jorenheit/bfcpu/doc/compiling.tex

\chapter{Introduction to Acus}

\section{What This is Not}
Acus\footnote{Latin for \emph{needle}, referring to the pointer in the BF computation model.} is not a BF compiler: it is a C++ library for the development of such compilers. This chapter is \emph{not} a guide on how to use Acus. For examples and extensive API-details, please visit the Github repository at \cite{acus}. Instead, this chapter goes through the most important concepts, methods and abstractions that allow for the translation of high-level programming concepts (like function-calls and flow-control) into BF.

\begin{figure}[H]
  \centering
  
\end{figure}

\section{Motivation and History}
Up to this point, almost every BF program used to test the computer was found online and used verbatim. On some occasions, simple BF routines were written to test very specific functions of the computer, but these were borderline trivial to produce. The next goal therefore was to create a compiler that takes human-readable source code and turns that in to BF which in turn can be assembled into the binary format understood by Synapse-191.

The author has attempted to create such a language and compiler in the past: \emph{BrainFix} \cite{brainfix} is a compiler that takes a C-style language and turns it into BF. This compiler works reasonably well but has some serious limitations:
\begin{itemize}\itemsep0em 
\item No (true) function-calls: all functions are inlined. Recursion is therefore \emph{not} possible.
\item Dynamic array accesses were implemented in a way that limits the maximum array size to 256 elements.
\item Only 8-bit numbers are supported (assuming the BF tape stores 8-bit integers in its cells).
\item No signed integers.
\item No pointers or function pointers.
\end{itemize}
%
These limitations derive from naive choices during early development of the compiler, where the focus was on parsing and language design: features were bolted on rather than planned for in early stages of development. In this second, more mature, attempt to build a compiler, we started out by building a backend rather than a full compiler: \emph{Acus}. Acus is a C++ library that exposes a set of elementary assembly-like instructions (like arithmetic operations, conditional expressions and jumps) that are compiled into BF. Acus is meant to be used a compiler back-end: a layer that accepts higher-level operations and emits BF code. A front-end can then link with Acus, parse an actual programming language, call the necessary Acus functions and produce the corresponding BF. Acus can also be used on its own, since its library-functions were designed to feel a bit like an actual language, as can be seem from the \emph{Hello World} snippet of Listing \ref{lst:acushello}\footnote{Note that using Acus in this way is unintended and inconvenient: the resulting binary is a program that, when run, prints a string of BF commands to the output. That string of commands then has to be written to a file, which can then be executed by a BF computer or interpreter. When the program is modified, the C++ source has to be recompiled and the resulting executable re-run to produce the updated BF source.}

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

    int main() {
      Assembler a;

      a.program("hello", "main").begin(); {

        a.function("main").begin(); {
          a.print(literal::string("Hello, World!\n"));
          a.returnFromFunction();
        } a.endFunction();

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

\section{Challenges and Design Goals}
The main goal was to make Acus capable enough that a frontend for a language like C would have no problem implementing most of its features. These include:
%
\begin{enumerate} \itemsep0em 
\item 8-bit and 16-bit integer datatypes;
\item signed integers (both 8-bit and 16-bit);
\item arrays and strings;
\item user-defined structured types (structs);
\item arithmetic operators (\texttt{+, -, *, /, \%});
\item logic operators (\texttt{and, or, not, xor});
\item function-calls and recursion;
\item pointers and pointer arithmetic;
\item labels and conditional jumps (\texttt{goto});
\item global data.
\end{enumerate}
%
Familiar features that were \emph{not} implemented include:
\begin{enumerate} \itemsep0em 
\item floating/fixed point numbers;
\item bitwise operators;
\item member functions;
\item control-flow mechanisms like \texttt{for, while, switch, if}.
\end{enumerate}
%
Many of the above can be implemented in terms of the features provided by Acus; it was a deliberate choice not to make these part of the library in order for the library to remain as fundamental as possible.

\chapter{Acus Program Model}

\section{Basic Block Scheduling}
In the Acus model, a program consists of a series of basic blocks, sequences of code that are always executed in order, and jumps between those blocks. Each basic block ($B_i$) is compiled into its corresponding BF instructions and wrapped in a BF loop-pair (i.e.  between \texttt{[} and \texttt{]}) whose entry is controlled by generated guard code $G_i$. The complete sequence of blocks is enclosed in a main-loop, conditional on the value in a special BF-cell, the \emph{Run}-cell, which can be reset by any block when the program should be terminated. Prior to entering the main-loop a \emph{head} section $H$ is responsible for the initial setup of the data-tape and the tail-code $T$ is responsible for resetting the pointer to the \emph{Run}-cell before the closing bracket of the main-loop is encountered:

\begin{center}
  
\end{center}

The aforementioned guard-code $G_i$ compares the block-index $i$ to the value stored in another predefined cell: the \emph{TargetBlock}-cell. Only when this cell contains the exact index of the block \emph{and} the \emph{Run}-cell is still nonzero, is the loop entered and its code executed. Therefore, each block should at some point set the index of next block to be executed to keep the program going (not setting a different \emph{TargetBlock} will cause the same block to be executed ad infinitum). This approach basically implements a state-machine that can be expressed in pseudo-code as shown in Listing \ref{lst:acusprogram}. Note that, on each iteration of the main-loop, all blocks are scanned until the scheduled block is encountered. In a worst-case scenario, when block \texttt{i} is scheduled by block \texttt{i+1} (the currently exectuted block), the system will first need to check all blocks from \texttt{i+2} up to \texttt{N} before looping back to block 1 and eventually block \texttt{i}.

\begin{lstfloat}[H]
  \begin{lstlisting}[style=pseudocode]
    B = {B1, B2, ..., Bn}

    Run = 1
    TargetBlock = 1 # not necessarily block 1

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

\section{Frames and Initialization}
Each function has its own chunk of memory that it operates on, called a frame. Calling a function has the effect of advancing the data-pointer one cell beyond the end of the current current function's frame. When a BF program is executed, the pointer starts at cell 0 in frame 0, which is dedicated to hold the global data (Section \ref{sec:compiling:globalframe}). Frame 1 starts just beyond the end of frame 0; the exact offset depends on the number of global variables and their sizes. The initialization code that runs prior to entering the main loop, needs to set up both frame 0 and frame 1:
%
\begin{enumerate}
\item Set a marker (the \texttt{SeekMarker}, Section \ref{sec:compiling:seekmarker}) at the start of the data-tape (cell 0). This marker can be used as a stop-sign during dynamic pointer movements to locate the start of the global data frame (and to prevent the pointer from moving into the (undefined) negative address-space).
\item Set another marker (the \texttt{FrameMarker}) that marks the start of frame 0 (the global data frame, Section \ref{sec:compiling:globalframe}). This might seem redundant as we already marked the start of this frame with a \texttt{SeekMarker}, but since every frame has a \texttt{FrameMarker}, the global frame needs it as well for generalized algorithms to work.
\item Calculate the size of frame 0 and move the pointer to the start of frame 1 (the frame that will be used by the function that is set as the entrypoint for the program). 
\item Mark the start of frame 1 by setting the \texttt{FrameMarker} here as well.
\item Move the datapointer to the \emph{Run}-cell of frame 1 and set its value to 1.
\item While the datapointer points to the \emph{Run}-cell of frame 1, open the main-loop (guaranteed to be entered as we just set this cell to 1).
\end{enumerate}

\section{Block Guards}
The guards $G_i$ compare the value stored in the \texttt{TargetBlock} cell to their index and check if the \emph{Run} flag is still set. The results of these comparisons are and'ed together and used as the loop-condition for the block that follows immediately after. Because the block-index is known at compile-time, it can simply be subtracted from (a copy of) the \texttt{TargetBlock} value. If the result is 0, this means we should enter the block given that the \emph{Run}-cell contains a nonzero (true) value. The logic necessary to implement these checks is discussed in more detail in Section \ref{sec:compiling:logic}. A simplified BF algorithm that implements this logic could look like the snippet of Listing \ref{lst:guard}; the real algorithm is more complicated because it needs to support 16-bit block-indices (otherwise each program would be limited to only 255 code-blocks), which requires 16-bit arithmetic and logic routines (Section \ref{sec:compiling:arithmetic}).

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

\end{lstlisting}
\caption{Simplified guard code for block 3 ($G_3$). The contents of block 3 will be executed only if \texttt{f} is nonzero.}
\label{lst:bfadd}
\end{lstfloat}

\section{Example: Fibonacci}
To illustrate how a program is divided into basic blocks, a simple fibonacci number generator is shown in Figure \ref{fig:fibexample}. It consists of three functions, each of which contains multiple basic blocks. The block-ID's are shown in square brackets at the start of each block. Blocks end at control-boundaries, i.e.~ places in the code where potential jumps take place or explicitly at predefined labels.

The program starts execution in block 10, which is set as the entry-point by the initialization code (note that the initialization code of Listing \ref{lst:acusprogram} sets the entry-point to block 1; the specific example from below requires the initialization sequence to set this value to 10 instead). A function-call is immediately encountered, ending the current block. After initializing a new stack frame (this will be covered later, Section \ref{sec:noideayet}), the \emph{TargetBlock} is set to block 1: the entry-block index of the callee. This will cause control flow to skip over block 11 and loop back to block 1, which will then be entered. When control hits the conditional statement of block 3, either block 4 or 5 will be set as the next target-block, depending on the result of evaluating \texttt{i < n}. In this case, both the \texttt{if}- and \texttt{else} body contain only a single block that immediately terminates in a jump. When control eventually reaches the end of \texttt{main}, the \emph{Run}-cell is set to zero, causing flow to exit the main loop and terminate the program.

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

\chapter{Tape Abstractions}
\section{Overview}
The data-tape is considered a stack, where each function owns a stack frame. Each frame contains a return-slot (if the function returns a value), argument-slots (if the function takes arguments) and local data (variables and temporaries used in the function). A slot is a series of (logical) cells that contains a variable of some data-type, used by the function. The size of a slot depends on the number of cells required to represent the type of the variable. Instead of using single BF-cells to compose slots, logical cells or macro-cells are used. Each macro-cell contains 9 actual BF-cells, referred to as \emph{fields} from now on, each of which serves a different purpose. Central to the macro-cells are the two value-fields that hold the actual value of the logical cell. By having two value fields, we allow for 16-bit datatypes to be implemented within the same logical-cell, rather than having to allocate two macro-cells for a single 16-bit variable. The other fields hold temporary data or metadata required to perform higher level functions like arithmetic, flow control and dynamic pointer movement. When the compiler needs to generate code that moves the BF-pointer to location known only at runtime (for example when dereferencing pointers or accessing array elements by a dynamic index), these fields can hold temporary values or metadata necessary to perform the move. Other non-value fields include temporary scratch-pads (heavily used when performing arithmetic operations), payload-fields (used to transport data to locations known only at runtime) and a flag cell that is dedicated to the evaluation of loop-conditions. Having all these fields near one another on the BF-tape has the nice consequence of BF-algorithms being relatively short due to tight pointer-move-sequences.

\subsection*{Example: Fibonacci (continued)}
Figure \ref{fig:tapehierarchy} shows the tape hierarchy described above, applied to the fibonacci example from before and evaluated immediately after \texttt{fib} was first called. Even though this program made no use of any global data, this frame is still depicted for completeness' sake. Zooming in on Frame 2, used by the \texttt{fib}-function, we see how a frame starts with the slots we previously encountered in Section \ref{sec:compiling:program}: the \texttt{TargetBlock} and \texttt{Run} slots, which are used to determine where to jump next and whether to continue execution at all. Since \texttt{fib} does not return anything, no return-slot has been allocated to this frame. Instead, the local data immediately follows: first the arguments passed to the function (initialized by the caller), then the local data used within the function. Only the variables \texttt{c} and \texttt{i} have been explicitly allocated by the programmer, but temporary slots have been created by the compiler to store the result of \texttt{a + b} and \texttt{i < n}.

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

Sections \ref{sec:compiling:first} through \ref{sec:compiling:last} below will go into more detail about each of the layers of abstraction.

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

\section{Cells and Macro-Cells}
BF operates on the most fundamental level of raw cells. Each consecutive sequence of 9 such cells constitutes a logical macro-cell as mentioned before in Section \ref{sec:compiling:tape}. In this section, we will cover each of the 9 fields of a macro-cell in more detail and cover some of their use cases. 

\subsection{\texttt{Value0} and \texttt{Value1}}
The value fields together hold the semantic value of the macro-cell. The \texttt{Value0} field contains the low byte and the the \texttt{Value1} field holds the high byte of an integer of at most 16 bits. Acus implements four integer data-types using these two fields: unsigned 8-bit (\texttt{u8}), unsigned 16-bit (\texttt{u16}), signed 8-bit (\texttt{s8}) and signed 16-bit (\texttt{s16}). When referring to 8-bit values, the \texttt{Value1} field is simply ignored. Signed integers are represented using two's complement; some algorithms need to do some additional work (like evaluating the sign-bit) before applying the usual operations.

\subsection{\texttt{Scratch0} and \texttt{Scratch1}}
Many BF algorithms need temporary cells as scratch-pads. These cells can be temporarily claimed by an algorithm and must be left behind empty for the next algorithm to use. An example of a simple algorithm that makes use of these values is the non-destructive addition. Say we want to add the contents of cell \texttt{x} to those of cell \texttt{y} without destroying \texttt{x} in the process. We can achieve this by decrementing \texttt{x} while at the same time incrementing \texttt{y} until \texttt{x} becomes zero. However, in order to restore \texttt{x} to its original value, we need to use a scratch-pad to construct a copy of \texttt{x} which is moved back after the addition has been completed. This algorithm is shown in Listing \ref{lst:bfadd}, where instead of denoting pointer-movement with sequences of \texttt{<} and \texttt{>}, we simply write the name of the variable/slot to indicate a move to that (known) location on the tape.

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

  # Step 1: add x to both y and tmp, destroying x
  x[- y+ tmp+ x]

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

\subsection{\texttt{Flag}}
The \texttt{Flag} field is reserved to store a value that determines whether or not a BF-loop should be entered. An algorithm can store an intermediate, temporary, value in the flag-cell and use that as a branch or loop-condition. Whereas scratch-cells are general purpose temporary storage locations, the flag-cell is meant to be used for this purpose alone to avoid confusion. The section below includes an example that also utilizes this field in Listing \ref{lst:bfseekframe}.

\subsection{\texttt{FrameMarker}}
The \texttt{FrameMarker} field is only set when the macrocell marks the start of a new frame. When performing dynamic pointer movements, a marker like this (the \texttt{SeekMarker} is used in a similar way) can be used to move from a still unknown to a known location on the tape. Let's say we know the data-pointer is somewhere in Frame 2, but we don't know where because we just performed some (dynamic) movement (i.e. an algorithm that moves the pointer by an amount that depends on runtime data). We know that the start of the frame is to the left of the current position, so we can perform the algorithm below and be sure that we're pointing at the start of the frame when the algorithm is finished. This algorithm is shown in the pseudo-BF of Listing \ref{lst:bfseekframe}. This works because every macro-cell has the same width and because exactly one FrameMarker is set at the start of the active frame.

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

    # Assumed: there already exist implementations for assignment and
    #          the logical NOT operator.
    
    ASSIGN(Flag, NOT(FrameMarker))
    Flag [-                            # Reset flag before moving away from it
      FrameMarker  <<<<<<<<<           # Move to the frame-marker field of
                                       #   neighboring macro-cell
      ASSIGN(Flag, NOT(FrameMarker))   # Compute exit-condition
      Flag                             # Check exit-condition
    ]

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

\subsection{\texttt{SeekMarker}}
The purpose of the \texttt{SeekMarker} field is very similar to that of the \texttt{FrameMarker} field, in the sense that it is used to mark certain cells to make dynamic movement possible. For example, a known location can be marked before performing a dynamic move, in order to be able to move back to that known location using an algorithm similar to that of Listing \ref{lst:bfseekframe}. Also, when a dynamic move has been completed, its location can be marked to make future excursions to this location more efficient. Contrary to the \texttt{FrameMarker}, which is specifically used to mark the start of a frame, the \texttt{SeekMarker} field may be set for any macro-cell on the tape.

\subsection{\texttt{Payload0} and \texttt{Payload1}}
The payload fields are used to store values that need to be transported along to dynamically determined locations. Algorithms that move the pointer to such locations can be trivially extended to move data along using these fields: one for the low byte and one for the high byte of the value. Additionally (but this is not the intended use-case), a payload cell may be used as a scratch-pad (when an algorithm has exhausted the available scratch cells), provided it is not being used to transport any values at that time.

\section{Slots}
A slot is a storage location for one object. Single 8 or 16-bit integers occupy a single macro-cell, while larger objects like arrays or structs occupy a sequence of macro-cells. A slot is bound to a stack frame; its offset is defined as the index of its first macro-cell with respect to the start of the frame, not the start of the actual BF data-tape.

In addition to a name and offset, a slot holds information about its scope (to determine access, allow for name-shadowing and keep track of lifetime) and its \emph{kind}. Most slots are of the \emph{local} kind, representing data local to the current function, but slots can also be tagged \emph{global}, \emph{available} (representing a free block of memory that was previously occupied), \emph{temp} (for temporary slots that should be freed after use) and \emph{cache} (Section \ref{sec:compiling:cache}). Figure \ref{fig:slots} shows a section of a frame and how local slots could be organized given their data-types and sizes. Note that the size of a slot is expressed in terms of the number of macro-cells rather than raw BF cells.

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

\subsection{Data Types}
Slots reserve space on the tape, but the compiler also needs to know how that space should be interpreted. This is the role of data types. A data type determines how many macro-cells are needed to store a value, which sub-slots exist inside that value, and which algorithms may be used to copy, compare, increment or otherwise manipulate it.

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

\texttt{s8} &
1 &
Signed 8-bit integer, stored using the same physical layout as \texttt{u8}. \\

\texttt{u16} &
1 &
Unsigned 16-bit integer stored across both value fields of a macro-cell. \\

\texttt{s16} &
1 &
Signed 16-bit integer, stored using the same physical layout as \texttt{u16}. \\

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

\texttt{ptr<T>} &
2 &
Pointer to a value of type \texttt{T}. The type parameter determines how dereferenced storage is interpreted. The first cell contains the \texttt{FrameDepth} of the pointer, i.e. how many frames back the pointee is actually stored. The second cell stores the offset of the pointee within its frame. Refer to section \ref{sec:compiling:pointers} for more details on pointers. \\

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

\subsection{Slot Proxies and Materialization}
Most expressions encountered by the compiler can be resolved directly into a slot. For example, assume \texttt{x} is an array of structs that contain an \texttt{age} field, e.g. 

\begin{lstlisting}
  struct Person {
    id:  u16
    age: u8
  };

  let x: array<Person, 5>;
\end{lstlisting}

In this context, the expressions \texttt{x}, \texttt{x[2]} and \texttt{x[2].age} all refer to known slots or sub-slots (assuming square brackets represent array indexing and a dot represents field access for struct objects). The compiler knows in which slot the array \texttt{x} is stored, it knows how to find the offset of element 2 and it knows how to find the offset of the \texttt{age} field.

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

For the purposes of this chapter, slot proxies should therefore be understood as compiler-level access paths. They bridge the gap between the static memory layout known at compile-time and the dynamic addresses that sometimes have to be computed at runtime. This idea becomes especially important in the caching system (Section \ref{sec:compiling:cache}), which is designed to limit unnecessary materialization and synchronization events.

\subsection{Local Memory Management}
Declaring a local variable means reserving a slot inside the current function frame. The slot is assigned a type, a size and an offset relative to the start of the frame. From that point onward, the variable name refers to this slot until it goes out of scope. Since the offset is fixed, accessing a local variable does not require a runtime search through the tape.

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

\section{Frames and Calls}
A frame groups all data belonging to one function activation. Each frame contains the local control cells, optional return storage, arguments, named locals and compiler-generated temporaries (and cached values). Function calls can then be viewed as transitions between frames: the caller prepares the callee frame, moves the data-pointer to the start of the frame and sets the \texttt{TargetBlock} value to the callee's entry block. When a function returns, the data-pointer is moved back to the caller's frame and execution continues at the first block beyond the call. Each of these steps will be described in more detail in the sections below.

\subsection{Reference Frames}
Each stack frame acts as a frame of reference, or coordinate system, to the data-pointer. Since function calls happen dynamically, stack frames are allocated dynamically as well. This means that the compiler has no way of knowing where the data-pointer is located in an absolute sense (i.e. with respect to the start of the BF-tape). Instead, it keeps track of the pointer-location with respect to the start of the current frame. Pushing a new frame on top of the stack and moving the pointer to the start of this frame can then be seen as performing a coordinate transformation - or rebase - of the pointer: the origin is now in the frame of the callee rather than the caller. 

\subsection{Global Data Frame}
Global data is allocated in its own frame at the very start of the data-tape, i.e. frame 0. This frame is not owned by any function and is accessible from any other frame to fetch data from or write to. Like dynamic array accesses or pointer dereferences, a global slot is accessed through a slot-proxy and will be materialized locally before any work can be done on it. This introduces synchronization issues accross call-boundaries, which will be addressed in Section \ref{sec:compiling:cache}. In the sections below, the concept of (stack) frames refers to a frames actually tied to the functions being executed, not the global frame.

\subsection{Frame Layout}
The exact layout of a frame depends on the nature of the function that it belongs to, depending on the return-type and number of arguments it takes. However, each instance of a function-call will cause an identical frame-layout to be generated as a result. In general, a frame is laid out as follows (in terms of macro-cells):
\begin{enumerate}
\item \texttt{TargetBlock}: a macro-cell who's \texttt{Value} fields are set to the index of the next block scheduled for execution and who's \texttt{FrameMarker} is set to 1, indicating the start of a new frame.
\item \texttt{Run}: a macro-cell dedicated to store a local copy of the program's \emph{run}-state. As soon as this flag is set to 0 (from any frame), none of the blocks will execute and the main loop will be aborted.
\item \texttt{ReturnSlot}: Depending on the return-type of the function, a slot is allocated to hold the return-value. Note that this slot is located at a fixed offset, so it can be reached easily even from within the caller's frame in order to fetch the return-value. If the function returns \texttt{void}, this slot does not exist at all.
\item \texttt{Locals}: Data local to the frame, which can be categorized further:
  \begin{enumerate}
  \item local variables (including function-arguments), organised in slots as discussed before in Section \ref{sec:compiling:slots}.
  \item compiler-generated temporaries
  \item cached materializations
  \end{enumerate}
\end{enumerate}

\subsection{Calls, Returns and Meta-Blocks}
\paragraph{Calls} To call a function, the caller has to perform the following actions:
\begin{enumerate}
\item Set the caller's \texttt{TargetBlock} to the ID of a compiler-generated meta-block. This is the continuation that will run after the callee returns (see Section \ref{sec:compiling:metablocks} below).
\item Copy or materialize the function arguments into the argument slots of the next frame. The offsets are known relative to the caller's frame, so this does not require a runtime search.
\item Initialize the control cells of the callee frame: its \texttt{Run} cell is set and its \texttt{TargetBlock} is set to the callee's entry block.
\item Move the data pointer to the start of the callee frame and treat this position as the new origin.
\end{enumerate}
After these steps, the runtime naturally dispactches to the block who's ID is now stored in the \texttt{TargetBlock} cell of the freshly initialized stack frame.

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

Propagatin the \emph{run}-flag like this makes early termination compositional: if a callee stops the program, the caller observes the same stopped state after the return metablock has run. This allows a (builtin) function like \texttt{abort()} to be implemented.

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

\chapter{Code Generation}
Before discussing larger compiler structures such as caching and dynamic access, it is useful to look at the small Brainfuck idioms from which Acus builds its generated code. Many of the algorithms in this section are simple in isolation, but together they form the vocabulary used to express higher-level operations on the tape. Moving or copying values, constructing constants or adding numbers together are all small patterns that appear repeatedly in the generated output.

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

\section{Clearing, Moving and Copying Values}
One of the simplest useful BF idiom is destructive movement: consume one cell while adding its value somewhere else. From that, one can build addition and non-destructive copying by introducing temporary storage. Basically all other algorithms rely on repeated applications of these idioms.

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

\section{Constant Factories}
Constructing known values is fundamental to creating meaningful programs. Even a simple \emph{Hello World} requires the compiler to construct those characters somewhere in memory. The simplest and most naive way of setting a BF cell to some known value, e.g. \texttt{n}, is to concatenate \texttt{n} plus-commands. For example, the expression \texttt{x = 20} can be compiled to:
\begin{lstlisting}[style=brainfuck]
  # SET(x, 20)
  x [-] ++++++++++ ++++++++++ # 23 characters + initial move sequence
\end{lstlisting}
Notice that the cell containing \texttt{x} is first cleared using \texttt{[-]}, since we generally cannot assume that it already contains zero (even if it was freshly allocated). This particular example adds 23 characters to the generated BF output (excluding the initial move); larger values obviously produce more characters. The number of characters needed to set a cell to some constant value $c$ is simply:
\begin{align}
  N_1(x\leftarrow c) = 3 + c + m(x)
\end{align}
where $m(x)$ is the number of move-commands necessary to reach the slot of \texttt{x} from the current pointer position.

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

\vspace{0.5cm}\noindent\begin{minipage}{\linewidth}
\begin{lstlisting}[style=brainfuck]
  # SET(x, 20)
  # Assumes s is an empty scratch cell
  
  x [-]         
  s ++++ [      
    x +++++     
    s -        
  ]
\end{lstlisting}
\end{minipage}
%
Instead of 23 characters, this algorithm adds only 15 non-movement characters to the program. In general, when $c$ can be factored into $a$ and $b$, the number of BF characters necessary to construct this value is:
\begin{align}
  N_2(x\leftarrow ab, s) = 6 + a + b + m(x) + 3m(x, s)
\end{align}
where $m(x,s)$ is the number of move-commands necessary to move between the scratch-cell \texttt{s} and the target cell \texttt{x}. This value depends on the exact layout of a macro-cell but can be as low as 2 when the scratch-fields are right next to the value-fields. In the case where $m(x,s)=2$, the difference between both methods for this specific example is
\begin{align}
  N_1 - N_2 &= 3 + 20 + m(x) - (6 + 4 + 5 + m(x) + 3\cdot 2) \\
            &= 23 - 21 = 2.
\end{align}
In this small example the saving is only two characters, while the runtime cost increases because the generated loop must be executed. Luckily the benefit from the second method increases along with the value of $c$. Acus has a precomputed table of factors for all numbers up to 128 (listed in Appendix \ref{sec:appendix:factorytable}). Larger values can be reached by decrementing using the minus command to come down from 255 rather than up from 0 (BF cells wrap around after being decremented beyond 0). Each factorization $a\times b$ is chosen in such a way that it minimizes the sum $a+b$ (and consequently the number of output characters). In some cases (e.g. when $c$ itself is prime), it is better to factor a number close to $c$ and correct for the difference after doing the multiplication. For example, the optimal way to construct the value 31 is to first construct 30, then add 1, i.e. $31 = 5\times6 + 1$ for a total cost of 24 characters (as opposed to 34) for a gain of 10 characters per construction. Figure \ref{fig:constants} shows the number of characters generated for every constant up to 128 (the graph would be symmetric around this number when going from 129 to 255), for both methods. Acus implements both the naive and factorizing method and picks whichever produces the least amount of code.

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

\section{Addition and Subtraction}
\subsection{Addition (8-bit)}
The algorithm for addition is much like that of copying, the difference being that the target cell is never cleared in advance. When the right-hand-side (rhs) of an expression of the form \texttt{x += y} may be destroyed, the algorithm is very short and efficient:

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

\subsection{Addition (16-bit)}
Adding 16-bit numbers together is much more involved and no BF pseudocode will be listed for this reason. Instead the higher-level pseudocode of Listing \ref{lst:16bitadd} illustrates the process. First, the low bytes are added together as usual. If the resulting value is less than its original value, this means that the cell has overflowed and we need to carry a 1 to the high byte. This requires multiple scratch-cells to hold temporary copies and helpers. Moreover, we need to be able to do a less-than comparison and branch on the result to carry if necessary. The implementation of this operator is discussed below in Section \ref{compiling:less}.

\vspace{0.5cm}\noindent\begin{minipage}{\linewidth}
\begin{lstlisting}[style=pseudocode]
  # 16-bit version of x += y
  xLowBefore = low(x)
  low(x) += low(y)          # normal 8-bit add
  if low(x) < xLowBefore:
    high(x) += 1            # carry on overflow
  high(x) += high(y)        # normal 8-bit add
\end{lstlisting}
\end{minipage}

\subsection{Subtraction}
The subtraction algorithms are symmetric to the ones for addition, where increments are substituted for decrement operations and instead of checking for overflow, we check for underflow in the 16-bit case (i.e. wether the result has grown after doing the 8-bit subtraction on the low byte).

\subsection{Signed Integers}
For signed integers, no special algorithms have to be used at all. Since signedness is encoded using two's complement representation, addition and subtraction already work out of the box. Signedness becomes more important for comparisons, where the same bit pattern may represent a different ordering depending on how it is interpreted (as signed or unsigned).

\section{Multiplication and Division}
\subsection{Multiplication (8-bit)} Multiplication can be implemented in terms of repeated addition, much like we already did in the constant factory optimization. To evaluate the expression \texttt{x *= y}, we do the following:
\begin{enumerate}
\item Make a copy of the operand \texttt{x}.
\item Clear \texttt{x}
\item Repeatedly decrease \texttt{y} while adding the original value of \texttt{x}, stored in the copy, to \texttt{x} itself.
\end{enumerate}
The steps above are the generalized version of the algorithm, which can be optimized further for edge cases where \texttt{y = 0}, \texttt{y = 1} or even for powers of 2.

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

\subsection{Multiplication (16-bit)} A naive 16-bit algorithm can simply follow the exact same procedure by relying on 16-bit addition. However this leads to a lot of additions for large factors, which can slow down the runtime significantly. Instead, we can perform a small series of 8-bit multiplications and additions to get the same result, realizing that the 16-bit number is stored as a 2-digit base-256 number. That is, every 16-bit integer $x$ can be written as
%
\begin{align}
  x = x_0 + 256\cdot x_1,
\end{align}
%
where $x_0$ and $x_1$ are the low and high bytes of $x$ respectively. Multiplication then becomes:
%
\begin{align}
  z = x \times y &= (x_0 + 256x_1)(y_0 + 256y_1) \\
                 &= x_0y_0 + 256\cdot(x_1y_0 + x_0y_1) + 256^2\cdot(x_1y_1)
\end{align}
%
The final term only contributes to bits beyond the lowest 16 bits, so it can be discarded when the result is stored as a 16-bit value. This means that the low and high byte of the product $z$ can be expressed as
%
\begin{align}
z_0 &= x_0 y_0 \bmod 256 \\
z_1 &= \left(x_0 y_1 + x_1 y_0 + \left\lfloor \frac{x_0 y_0}{256} \right\rfloor \right) \bmod 256 
\end{align}
%
Therefore, the 16-bit product can be computed using three 8-bit multiplications. The low byte of the result comes from the low byte of $x_0y_0$, while the high byte receives the carry from this product together with the low bytes of the two cross-products.

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

  low(z)  = low(p0)
  high(z) = low(p1 + p2) 
\end{lstlisting}
\end{minipage}

\subsection{Division (8-bit and 16-bit)}
Unsigned division is implemented using repeated subtraction. Given two values \texttt{x} and \texttt{y}, the goal is to compute a quotient \texttt{q} and remainder \texttt{r} such that
%
\begin{align}
x = qy + r, \qquad 0 \leq r < y.
\end{align}
%
The simplest way to do this is to repeatedly subtract \texttt{y} from a running remainder until doing so would make it negative. The number of successful subtractions is the quotient, while the value left behind is the remainder.

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

  while r >= y:
  r -= y
  q += 1
\end{lstlisting}
\end{minipage}

The actual BF implementation cannot test \texttt{r >= y} directly. Instead, this comparison is implemented using scratch cells: temporary copies of \texttt{r} and \texttt{y} are decremented together until one of them reaches zero. If the copy of \texttt{y} reaches zero first, the subtraction is safe and the loop may continue. If the copy of \texttt{r} reaches zero first, the next subtraction would underflow and the algorithm terminates. The original values must either be preserved during this test or reconstructed afterwards, which makes division considerably more expensive than addition or multiplication.

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

Division by zero is not meaningful in this model and has to be handled separately by the compiler or by the generated program. In the current arithmetic model, unsigned division should therefore be understood as an operation that assumes a nonzero divisor.

\subsection{Signed Multiplication and Division}
Signed multiplication and division are implemented as thin layers around the corresponding unsigned algorithms. First, the sign bit of the left-hand side is inspected. If it is set, the value is negated in-place and a temporary flag is set to indicate that the final result should be negative. The right-hand side is copied into temporary storage before its sign is inspected, so the original divisor or multiplier does not have to be modified. If this copy is negative, it is negated as well and the result-sign flag is toggled. At this point, both operands have been converted to positive values, while the temporary flag records whether the original operands had opposite signs.

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

\section{Boolean Operations}
All of the usual logic and comparison operators have been implemented in Acus, which allow the programmer to build complex logical expressions. Some of these logical building blocks will be explained below.

\subsection{Conversion to Bool}
The simplest boolean conversion is one where an integer is transformed into either a 0 or 1, depending on its truth-value (any non-zero is considered \emph{true}). To accomplish this, the value of the operand \texttt{x} is moved into a scratch cell, leaving \texttt{x} empty. We then branch off the value of \texttt{s}: if non-zero, \texttt{x} is set back to 1. If the conditional block is not entered, \texttt{x} remains 0.

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

\paragraph{Logical Not} The not-operator does the exact opposite of a boolean conversion. It transforms its operand into 1 when it's value equals 0 and vice versa for any non-zero values. The algorithm is almost identical to that of \texttt{BOOL(x)}: instead of setting \texttt{x} to 0 and incrementing it in the loop-block, we set it to 1 and decrement it inside the loop.

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

\subsection{Logical And}
The \texttt{AND} operator is implemented using a nested BF-loop block. The operands are used to decide if those blocks should be entered. The result is then set in the inner loop, which can only be reached if both operands evaluate to \emph{true}.

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

\subsection{Logical Or}
If we compare the logical \texttt{AND} algorithm to two switches wired in series, where current can only flow if both switches are turned on, the \texttt{OR} algorithm is its parallel counterpart. Each of the operands guards a loop and if either one of them is entered, the result is set to \emph{true}.

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

\subsection{Equality}
In testing for equality, we rely on the fact that $x-y=0$ when $x=y$ to implement a routine that calculates \texttt{NOT(x - y)}.

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

\subsection{Less Than}
This operator was already used before in the implementation of 16-bit addition, to determine the value of the carry-bit. It is implemented by reducing both of its operators simultaneously, until either one of them reaches zero. If the rhs is still non-zero when this happens, the lhs must have been the smaller of the two. This turns out to be a pretty tedious algorithm when expressed in BF so instead it is presented in pseudo-code below. Other comparison operators are implemented similarly.

\vspace{0.5cm}\noindent\begin{minipage}{\linewidth}
\begin{lstlisting}[style=pseudocode]
  # LT(x, y)

  while x AND y:
    --x
    --y

  x = NOT(y)
\end{lstlisting}
\end{minipage}

\subsection{Signed Comparisons}
Comparisons on signed integers cannot use the unsigned implementations discussed before. Instead, the exact form of the algorithm depends on the sign-bits of both of the argument. A runtime check has to be done to determine which one of four branches must be taken. For example, for the less-than operator, if its operands are both signed:

\begin{enumerate}
\item If both are positive, use the unsigned algorithm.
\item If the lhs is negative and the rhs is positive (or zero), return 1 immediately.
\item If the lhs is positive (or zero) and the rhs is negative, return 0 immediately.
\item If both are negative, use the unsigned greater-than algorithm on their absolute values.
\end{enumerate}

This requires an algorithm to evaluate the sign of an integer and one to take its absolute value. To get the sign-bit of an 8-bit value $x$ (1 if negative, 0 otherwise), we simply compute the result of $x >= 128$ (using the unsigned greater-equal operator). Values with bitpatterns identical to unsigned values from 128 on are interpreted as negative numbers (i.e. have their highest bit set) in two's complement representation.

To calculate the absolute value of a signed integer, its sign-bit is first calculated. If not set, the value can remain unmodified since it's already positive. If the sign-bit \emph{is} set, it can be negated simply by subtracting it from 0.

\vspace{0.5cm}\noindent\begin{minipage}{\linewidth}
\begin{lstlisting}[style=brainfuck]
  # ABS(x)
  # Assumes s to be an empty scratch-cell

  SUB_FROM(s, x)
  MOVE(s, x)
\end{lstlisting}
\end{minipage}

\section{Pointer Movement}
BF has no random access instruction; the only way to reach a cell is to move the data-pointer (simply referred to as the \emph{pointer} from now on) step by step. This makes pointer movement one of the central code-generation problems in Acus. 

\subsection{Static Pointer Movement}
In most scenario's, when the source and destination locations are known at compile time, pointer movement is straightforward: emit the required number of \texttt{<} or \texttt{>} commands. This is the common case for local slot operations within a frame, where the compiler can keep track of the current pointer position relative to the frame origin.

\subsection{Dynamic Pointer Movement}
The most interesting pointer-movement algorithms are the ones where the target is not known until runtime. Examples include array access by a runtime index and pointer dereferencing. These algorithms rely on metadata stored in macro-cells: markers, counters and payload fields are used so that the BF pointer can search through structured tape data and stop at the correct logical cell. We can distinguis between two different classes of dynamic pointer movement: \emph{marker-based} and \emph{offset-based} moves. In marker-based moves, the pointer moves along the tape until it hits some pre-set marker. In offset-based moves, the offset is stored in the payload cells and dragged along with the pointer while being reduced; when the payload becomes zero, the destination has been reached. 

\subsubsection{Marker-Based}
This method relies on a marker-field, the \texttt{FrameMarker} or \texttt{SeekMarker}, being set beforehand. We can then move the pointer into the corresponding field of the current cell and move in some direction until the marker is hit.

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

\subsubsection{Offset-Based}
The second class of dynamic pointer movement relies on a runtime value representing the offset being stored on the tape itself. For example, in the expression \texttt{x[i]}, \texttt{i} is a variable stored on the tape that contains the offset with respect to the start of the array \texttt{x} in terms of the size of the element-type of \texttt{x}. To reach a specific offset, the pointer is moved to the start of the array (known at compile-time) and the offset-value is copied or moved into its payload-fields (a single one for 8-bit values and both of them for 16-bit values). The pointer is then moved to the right while the payload is moved along and decremented. When the payload hits zero, the required offset has been reached.

\vspace{0.5cm}\noindent\begin{minipage}{\linewidth}
\begin{lstlisting}[style=brainfuck]
  # TO_OFFSET(b, i)
  # b = base address
  # i = index/offset wrt base

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

\subsection{Payload Transport}
Dynamic writes are harder than dynamic reads because data has to be carried to a location that is not statically known. Acus solves this by moving values through designated payload fields. The payload travels along with the dynamic traversal and is deposited when the target macro-cell is found.

For marker-based movements, the payload can simply be moved along with the pointer because the payload fields are not used to perform the move itself. For offset-based movements, the payload-fields already serve the purpose of containing the offset itself and cannot be used to transport the new value. Instead the usual offset-based method described in Section \ref{sec:compiling:dynamicmove:offset} is used to find the element, where a marker is planted. Then, the marker-based method is used to move the payload to that position and overwrite its value-field(s).

\chapter{Caching} \label{sec:compiling:cache}
Slot proxies (Section \ref{sec:compiling:slotproxies}) allow expressions to remain abstract until their value is needed. However, repeatedly materializing the same proxy can duplicate work. For example, accessing the same array element several times in a block should not require materializing the element locally each time. Instead, multiple accesses can be cached and a writeback occurs only when necessary, for example at control-flow boundaries.

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

To implement this caching system, dependencies between proxies need to be carefully maintained. During compilation, a dependency graph is built and used to determine which cache-entries have become dirty and which ones need to be flushed back into their actual storage location. This section will go over the different techniques and compromises that were made in their implementation.

\section{Cache Graphs}
A cache entry connects a logical proxy to a concrete slot that currently holds its materialized value. Entries can be marked dirty when modified or invalidated/removed when there is no guarantee that its value still represents the actual referred-to data.

Figure \ref{fig:cachegraph} shows a simplified representation of a cache graph, where each entry (node) contains information about the proxy that it represents, the physical location of the cached slot, and its parent- and child-nodes. An proxy \texttt{A} is considered a parent of proxy \texttt{B} if the canonical storage location of \texttt{B} is a subset of that of \texttt{A}. For example, given the expression \texttt{x[i][j]}, the expression \texttt{x[i]} is represented by a proxy that itself will be cached (assuming \texttt{i} is not known at compile-time). Therefore, to materialize the element \texttt{x[i][j]} we first need to materialize \texttt{x[i]} and their cache-entries are in a parent-child relation: \texttt{x[i]} is the parent of \texttt{x[i][j]} because the storage slot of \texttt{x[i]} encloses that of \texttt{x[i][j]}.

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

\section{Flushing and Invalidation}

\subsection{Dirty Entries} In the example of Figure \ref{fig:cachegraph}, all entries are \emph{clean} (i.e. not \emph{dirty}), since none of the expressions involving them modified their contents. The expression \texttt{x[i][j] = 3} would have the effect of writing the value 3 to the cache slot and marking its corresponding entry as dirty. Dirty entries must at some point be flushed into their parent to make sure that all changes applied to a cached object eventually propagate into canonical storage. 

\subsection{Flushing} Flushing an entry means writing its contents back into its parent (either another cached slot or canonical storage). An entry needs to be flushed in the following scenarios:
%
\begin{enumerate}
\item The entry is marked \emph{dirty} and a parent somewhere up in the cache hierarchy is materialized. If the dirty entry is multiple parents removed, this causes all intermediate parents to be flushed as well. For example, if \texttt{x[i][j]} is dirty and \texttt{x} is materialized, the dirty \texttt{x[i][j]} is flushed into \texttt{x[i]}, which then becomes dirty and is subsequently flushed into \texttt{x} itself. The entire path from \texttt{x[i][j]} to \texttt{x} is now clean.
\item Whenever a control-flow boundary is crossed. For example, at jumps or function-calls, the entire cache is cleared by flushing all entries (starting at the deepest child-nodes) back into their canonical storage. This makes sure that all flow-paths see the correct data.
\item Whenever a pointer is dereferenced. Because pointers can refer to anything (of some type) at runtime, the entire cache is cleared to make sure that the pointee is up-to-date when fetched by the dereferencing algorithm.
\item Before cache-invalidation. In scenario's where a cache entry is invalidated (removed from the tree), it is flushed back before doing so. Cache invalidation is discussed in more detail below.
\end{enumerate}

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

\subsection{Invalidation} Entries can be invalidated when an external dependency or (indirect) parent is modified. In the example of Figure \ref{fig:cachegraph} the entries \texttt{x[i]} and \texttt{x[i][j]} have been materialized in cache using the value stored in slot \texttt{i} at that time. When the value of \texttt{i} is modified, the proxy refers to a new object and the entry has become invalid. When this is about to happen, the invalidated proxy has to be flushed (if dirty) \emph{before} modifying the dependency, after which it (and its descendants) can be removed from the cache tree.

\subsection{Writes}
Writing to a proxy will, as mentioned before, cause its cached entry to be marked \emph{dirty}. When the object is overwritten independently from its original value, there is no need to materialize that value at all. For example, when compiling the expression \texttt{x[i][j] = 3}, the value stored initially in \texttt{x[i][j]} is completely irrelevant. In such cases, a new entry for the proxy \texttt{x[i][j]} is created and marked dirty immediately and no materialization algorithm has to be executed.

\subsection{Example} The listing below shows a more complete version of code that leads to the cache hierarchy of Figure \ref{fig:cachegraph}. At the lines marked \texttt{(a)} and \texttt{(b)}, the graph from Figure \ref{fig:cachegraph} is generated. Then, at line \texttt{(c)}, a new value is assigned to \texttt{x[i][j]}. This assignment expression will write the value \texttt{3} directly to the already cached slot for the proxy \texttt{x[i][j]} and mark this entry as \emph{dirty}. At the next expression (line \texttt{(d)}), a new proxy (\texttt{x[i][k]}) is materialized, which shares a parent (\texttt{x[i]}) with the now dirty entry \texttt{x[i][j]}. Therefore, before materializing \texttt{x[i][k]}, the dirty entry is flushed upwards into \texttt{x[i]}, after which its dirty-state is cleared and \texttt{x[i][k]} can be materialized. Finally, at line \texttt{(e)}, the value of \texttt{i} is modified. All cache-entries that depend on \texttt{i} (the left branch of the graph) therefore need to be invalidated. In this example these entries have just been flushed and are still clean, so there is no need to flush them prior to deletion.

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
