jorenheit/bfcpu/website/content/tex/compilation.tex

\chapter{Introduction to Acus}
\label{sec:compilation:introduction}

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

\begin{figure}[H]
  \centering
  
\end{figure}

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

    int main() {
      Assembler a;

      a.program("hello", "main").begin(); {

        a.function("main").begin(); {
          a.print(literal::string("Hello, World!\n"));
          a.returnFromFunction();
        } a.endFunction();

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

\chapter{Acus Program Model}
\label{sec:compilation:programmodel}

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

\begin{center}
  
\end{center}

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

\begin{lstfloat}[H]
  \begin{lstlisting}[style=pseudocode]
    B = {B1, B2, ..., Bn}

    Run = 1
    TargetBlock = 1 # not necessarily block 1

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

\section{Frames and Initialization}
\label{sec:compilation:framesinit}
Each function has its own chunk of memory that it operates on, called a frame. Calling a function has the effect of advancing the data-pointer one cell beyond the end of the current current function's frame. When a BF program is executed, the pointer starts at cell 0 in frame 0, which is dedicated to hold the global data (Section \ref{sec:compilation:globalframe}). Frame 1 starts just beyond the end of frame 0; the exact offset depends on the number of global variables and their sizes. The initialization code that runs prior to entering the main loop, needs to set up both frame 0 and frame 1:
%
\begin{enumerate}
\item Set a marker (the \texttt{SeekMarker}, Section \ref{sec:compilation:seekmarker}) at the start of the data-tape (cell 0). This marker can be used as a stop-sign during dynamic pointer movements to locate the start of the global data frame (and to prevent the pointer from moving into the (undefined) negative address-space).
\item Set another marker (the \texttt{FrameMarker}) that marks the start of frame 0 (the global data frame, Section \ref{sec:compilation:globalframe}). This might seem redundant as we already marked the start of this frame with a \texttt{SeekMarker}, but since every frame has a \texttt{FrameMarker}, the global frame needs it as well for generalized algorithms to work.
\item Calculate the size of frame 0 and move the pointer to the start of frame 1 (the frame that will be used by the function that is set as the entrypoint for the program). 
\item Mark the start of frame 1 by setting the \texttt{FrameMarker} here as well.
\item Move the datapointer to the \emph{Run}-cell of frame 1 and set its value to 1.
\item While the datapointer points to the \emph{Run}-cell of frame 1, open the main-loop (guaranteed to be entered as we just set this cell to 1).
\end{enumerate}

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

The program starts execution in block 10, which is set as the entry-point by the initialization code (note that the initialization code of Listing \ref{lst:acusprogram} sets the entry-point to block 1; the specific example from below requires the initialization sequence to set this value to 10 instead). A function-call is immediately encountered, ending the current block. After initializing a new stack frame (this will be covered later, Section \ref{sec:compilation:frames}), the \emph{TargetBlock} is set to block 1: the entry-block index of the callee. This will cause control flow to skip over block 11 and loop back to block 1, which will then be entered. When control hits the conditional statement of block 3, either block 4 or 5 will be set as the next target-block, depending on the result of evaluating \texttt{i < n}. In this case, both the \texttt{if}- and \texttt{else} body contain only a single block that immediately terminates in a jump. When control eventually reaches the end of \texttt{main}, the \emph{Run}-cell is set to zero, causing flow to exit the main loop and terminate the program.

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

The sections below go into more detail about each of the layers of abstraction.

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

\section{Cells and Macro-Cells}
\label{sec:compilation:macrocells}
BF operates on the most fundamental level of raw cells. Each consecutive sequence of 9 such cells constitutes a logical macro-cell as mentioned before in Section \ref{sec:compilation:tape}. In this section, we will cover each of the 9 fields of a macro-cell in more detail and cover some of their use cases. 

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

  # Step 1: add x to both y and tmp, destroying x
  x[- y+ tmp+ x]

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

In addition to a name and offset, a slot holds information about its scope (to determine access, allow for name-shadowing and keep track of lifetime) and its \emph{kind}. Most slots are of the \emph{local} kind, representing data local to the current function, but slots can also be tagged \emph{global}, \emph{available} (representing a free block of memory that was previously occupied), \emph{temp} (for temporary slots that should be freed after use) and \emph{cache} (Section \ref{sec:compilation:cache}). Figure \ref{fig:slots} shows a section of a frame and how local slots could be organized given their data-types and sizes. Note that the size of a slot is expressed in terms of the number of macro-cells rather than raw BF cells.

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

\texttt{s8} &
1 &
Signed 8-bit integer, stored using the same physical layout as \texttt{u8}. \\

\texttt{u16} &
1 &
Unsigned 16-bit integer stored across both value fields of a macro-cell. \\

\texttt{s16} &
1 &
Signed 16-bit integer, stored using the same physical layout as \texttt{u16}. \\

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

\begin{lstlisting}
  struct Person {
    id:  u16
    age: u8
  };

  let x: array<Person, 5>;
\end{lstlisting}

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

For the purposes of this chapter, slot proxies should therefore be understood as compiler-level access paths. They bridge the gap between the static memory layout known at compile-time and the dynamic addresses that sometimes have to be computed at runtime. This idea becomes especially important in the caching system (Section \ref{sec:compilation:cache}), which is designed to limit unnecessary materialization and synchronization events.

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

When a slot is freed, either because a local variable leaves scope or because a temporary can be dismissed, its region is marked as available. The contents of the underlying macro-cells are not necessarily cleared immediately; freeing a slot only means that the compiler is allowed to reuse that region for later storage. When a new slot is allocated, a sufficiently large available region may be split into an occupied part and a smaller remaining available part. Conversely, when a slot is freed, neighbouring available regions are merged back together. This prevents the local frame from becoming unnecessarily fragmented and allows larger slots to be allocated later when enough adjacent macro-cells have become free. This management system is discussed in more detail in Section \ref{sec:compilation:memorymanagement}.

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

\subsection{Global Data Frame}
\label{sec:compilation:globalframe}
Global data is allocated in its own frame at the very start of the data-tape, i.e. frame 0. This frame is not owned by any function and is accessible from any other frame to fetch data from or write to. Like dynamic array accesses or pointer dereferences, a global slot is accessed through a slot-proxy and will be materialized locally before any work can be done on it. This introduces synchronization issues accross call-boundaries, which will be addressed in Section \ref{sec:compilation:cache}. In the sections below, the concept of (stack) frames refers to a frames actually tied to the functions being executed, not the global frame.

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

\subsection{Calls, Returns and Meta-Blocks}
\label{sec:compilation:metablocks}
\paragraph{Calls} To call a function, the caller has to perform the following actions:
\begin{enumerate}
\item Set the caller's \texttt{TargetBlock} to the ID of a compiler-generated meta-block. This is the continuation that will run after the callee returns (see Section \ref{sec:compilation:metablocks} below).
\item Copy or materialize the function arguments into the argument slots of the next frame. The offsets are known relative to the caller's frame, so this does not require a runtime search.
\item Initialize the control cells of the callee frame: its \texttt{Run} cell is set and its \texttt{TargetBlock} is set to the callee's entry block.
\item Move the data pointer to the start of the callee frame and treat this position as the new origin.
\end{enumerate}
After these steps, the runtime naturally dispactches to the block who's ID is now stored in the \texttt{TargetBlock} cell of the freshly initialized stack frame.

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

\chapter{Memory Management}\label{sec:compilation:memorymanagement}
\section{Overview}
Whenever a variable is declared to Acus, the allocator will look for available space in the current stack-frame. From the allocator's point of view, named locals, compiler temporaries and cache slots are all typed slots inside the current frame. They differ only in who requests them and when they are released.

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

\begin{enumerate}\itemsep0em
\item Freed slots are marked \texttt{Available} and can be re-used.
\item Declarations can be scoped to reduce the lifetime of variables. Variable slots will become \texttt{Available} when the variable goes out of scope.
\item Temporary slots declared by the compiler are freed immediately after use.
\item Adjacent \texttt{Available} slots are merged to accommodate larger data types.
\item \texttt{Available} slots will split into smaller parts when a variable with a size smaller than that of the slot is allocated to it.
\end{enumerate}

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

\subsection{Heap Allocation}
While technically possible, Acus does not support heap-allocation. This would require a separate heap-frame and a runtime system that keeps track of the memory layout in that frame (including de-allocation, block splitting and block merging). The runtime overhead that would arise from managing the heap at runtime would be so costly that it was decided to not implement this as a feature. However, a front-end might emulate heap-allocation using the global frame. One could certainly write algorithms on top of Acus to reserve a specific amount of raw data in the global frame and manage it using existing features.

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

\section{Clearing, Moving and Copying Values}
\label{sec:compilation:movecopy}
One of the simplest useful BF idiom is destructive movement: consume one cell while adding its value somewhere else. From that, one can build addition and non-destructive copying by introducing temporary storage. Basically all other algorithms rely on repeated applications of these idioms.

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

  low(z)  = low(p0)
  high(z) = low(p1 + p2) 
\end{lstlisting}
\end{minipage}

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

  while r >= y:
  r -= y
  q += 1
\end{lstlisting}
\end{minipage}

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

\vspace{0.5cm}\noindent\begin{minipage}{\linewidth}
\begin{lstlisting}[style=pseudocode]
  # LT(x, y)

  while x AND y:
    --x
    --y

  x = NOT(y)
\end{lstlisting}
\end{minipage}

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

  SUB_FROM(s, x)
  MOVE(s, x)
\end{lstlisting}
\end{minipage}

\section{Pointer Movement}
\label{sec:compilation:pointers}
BF has no random access instruction; the only way to reach a cell is to move the data-pointer (simply referred to as the \emph{pointer} from now on) step by step. This makes pointer movement one of the central code-generation problems in Acus. 

\subsection{Static Pointer Movement}
\label{sec:compilation:staticmove}
In most scenario's, when the source and destination locations are known at compile time, pointer movement is straightforward: emit the required number of \texttt{<} or \texttt{>} commands. This is the common case for local slot operations within a frame, where the compiler can keep track of the current pointer position relative to the frame origin.

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

\section{Flushing and Invalidation}
\label{sec:compilation:flushinvalidate}

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

\section{Move Semantics}
The algorithms for moving and copying BF cells are very similar: copying means we simultaneously move to the target-cell and a scratch cell, only for the scratch-cell to be emptied back into the source location. Obviously, we should move and avoid the full copy algrithm whenever possible. Therefore, if we can prove that the source is expendible, we can just move its contents out of it to a new location. Acus tries to find as many opportunities as possible to move instead of copy. For example in the following situations:
\begin{enumerate}\itemsep0em
\item Assignment from a temporary expression. e.g. \texttt{x = y + z}, where \texttt{y + z} is a temporary which does not outlive the statement anyway. 
\item Flushing cache-entries that are about to be deleted. When a cache-tree is flushed prior to it being deleted, we can move instead of copy towards the root.
\end{enumerate}

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

\section{Primitive and BF Merging}
\subsection{Merging Primitives}
Before generating actual BF characters, Acus will produce a series of primitives, each of which represents a relatively simple sequence of BF instructions on a slightly higher level (Table \ref{tab:primitives}). Sequences of primitives can sometimes be merged into shorter sequences or even no-ops. For example, if the primitive \texttt{MoveRelative(3)} is immediately followed by the primitive \texttt{MoveRelative(6)}, they can be merged into a single \texttt{MoveRelative(9)}. This leads to a series of merge-rules, listed in Table \ref{tab:mergerules}. By applying these rules iteratively to the generated sequence of primitives, the program can be shrunk significantly in post-processing.

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

  \texttt{MovePointerRelative(x)} & Move the pointer by \texttt{x} cells (positive means to the right). \\
  \texttt{ChangeValue(c)} & Change the current value by an amount \texttt{c}. \\
  \texttt{ZeroCell} & Set the current value to \texttt{0} using \texttt{[-]}. \\
  \texttt{ZeroCellPlus} & Set the current value to \texttt{0} using \texttt{[+]}. \\
  \texttt{ConstructConstant(c)} & Construct the value \texttt{c} in the current cell. \\
  \texttt{MoveData(x)} & Move the contents of the current cell to relative position \texttt{x}. \\
  \texttt{CopyData(x)} & Copy the contents of the current cell to relative position \texttt{x}. \\
  \texttt{Add(x)} & Add the value of the cell at relative position \texttt{x} to the value of the current cell. \\
  \texttt{Subtract(x)} & Subtract the value of the cell at relative position \texttt{x} from the value of the current cell. \\
  \texttt{Boolean} & Set the current cell to its boolean value. \\
  \texttt{Not} & Set the current cell to its logical not value. \\
  \texttt{Or(x)} & Set the current value to the logical OR of this value and the value inside the cell at relative offset \texttt{x}. \\
  \texttt{And(x)} & Set the current value to the logical AND of this value and the value inside the cell at relative offset \texttt{x}. \\
  \texttt{Xor(x)} & Set the current value to the logical XOR of this value and the value inside the cell at relative offset \texttt{x}. \\
  \texttt{Equal(x)} & Set the current value to 1 if it's equal to the value in the cell at relative offset \texttt{x}, 0 otherwise. \\
  \texttt{Less(x)} & Set the current value to 1 if it's less than the value in the cell at relative offset \texttt{x}, 0 otherwise. \\
  \texttt{LessOrEqual(x)} & Set the current value to 1 if it's less than or equal to the value in the cell at relative offset \texttt{x}, 0 otherwise. \\
  \texttt{Greater(x)} & Set the current value to 1 if it's greater than the value in the cell at relative offset \texttt{x}, 0 otherwise. \\
  \texttt{GreaterOrEqual(x)} & Set the current value to 1 if it's greater than or equal to the value in the cell at relative offset \texttt{x}, 0 otherwise. \\
  \texttt{Cmp(c)} & Set the current value to 1 if it's equal to the compile-time constant \texttt{c}, 0 otherwise. \\
  \hline
  \caption{Acus primitives.}
  \label{tab:primitives}   
\end{longtable}

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

\texttt{ZeroCell} & \texttt{ZeroCell} & \texttt{ZeroCell} \\
\texttt{ZeroCell} & \texttt{ZeroCellPlus} & \texttt{ZeroCell} \\
\hline

\texttt{ZeroCellPlus} & \texttt{ZeroCellPlus} & \texttt{ZeroCellPlus} \\
\texttt{ZeroCellPlus} & \texttt{ZeroCell} & \texttt{ZeroCellPlus} \\
\hline

\texttt{MovePointerRelative(x)} & \texttt{MovePointerRelative(y)} & \texttt{MovePointerRelative(x + y)} \\
\hline

\texttt{ConstructConstant(c)} & \texttt{ChangeBy(d)} & \texttt{ConstructConstant(c + d)} \\
\texttt{ConstructConstant(c)} & \texttt{ConstructConstant(d)} & \texttt{ConstructConstant(d)} \\
\texttt{ConstructConstant(c)} & \texttt{ZeroCell} & \texttt{ZeroCell} \\
\texttt{ConstructConstant(c)} & \texttt{ZeroCellPlus} & \texttt{ZeroCellPlus} \\
\texttt{ConstructConstant(c)} & \texttt{Boolean} & \texttt{ConstructConstant(c != 0)} \\
\texttt{ConstructConstant(c)} & \texttt{Not} & \texttt{ConstructConstant(c == 0)} \\
\texttt{ConstructConstant(c)} & \texttt{Cmp(d)} & \texttt{ConstructConstant(c == d)} \\
\hline

\texttt{ChangeBy(c)} & \texttt{ChangeBy(d)} & \texttt{ChangeBy(c + d)} \\
\texttt{ChangeBy(c)} & \texttt{ZeroCell} & \texttt{ZeroCell} \\
\texttt{ChangeBy(c)} & \texttt{ZeroCellPlus} & \texttt{ZeroCellPlus} \\
\texttt{ChangeBy(c)} & \texttt{ConstructConstant(d)} & \texttt{ConstructConstant(d)} \\
\hline

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

\texttt{Boolean} & \texttt{Boolean} & \texttt{Boolean} \\
\texttt{Boolean} & \texttt{Not} & \texttt{Not} \\
\hline

\texttt{Not} & \texttt{Boolean} & \texttt{Not} \\
\texttt{Not} & \texttt{Not} & \texttt{Boolean} \\
\hline

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

\hline
\caption{Primitive merge rules.}
\label{tab:mergerules} 

\end{longtable}

\subsection{Merging BF}
As a final pass, after all primitives have been lowered into actual BF character, Acus will scan the resulting source code for cancellation opportunities: sequences of consecutive \texttt{+} and \texttt{-} or \texttt{<} and \texttt{>} commands that can be collapsed. The primitive-merging rules already do this to some extend by merging \texttt{ChangeValue} and \texttt{MovePointerRelative} primitives, but that does not capture all opportunities. For example, when a \texttt{MovePointerRelative} primitive is followed by another that, when lowered to BF, starts with a sequence of \texttt{>} commands, these can be merged or cancelled in the final result.
