jorenheit/bfcpu/doc/img/images.odp

Memory

Program

Data

CPU

Registers

R1

⋮

Rn

ALU

Control Unit

IO

Output Devices

Input Devices

## Slide 2

CPU

Registers

R1

⋮

Rn

ALU

Control Unit

IO

Output Devices

Input Devices

Program Memory

Data
Memory

## Slide 3

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
Control Unit

Control Unit

⋮

⋮

Instruction
Flags
Cycle

Control signals

A,V

S

FB

4

Flags

Cycle

CC

3

Z

Instruction

ROM

DP

16

Data Bus

RAM

Address Bus

Keyboard

Screen

SP

8

## Slide 4

Address:

Data Array:

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
Data Pointer

## Slide 5

Address:

Data (RAM)

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
Data Pointer
(DP = 4)

## Slide 6

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
Microcode ROM’s

State

Instruction

Cycle

ROM 2

ROM 1

ROM 0

Address

16-23

8-15

0-7

⋮

## Slide 7

PLACEHOLDER

## Slide 8

555 Output

Flip-Flop Output

Decoder Clock

Module Clock

## Slide 9

Button

Monostable 1

Monostable 2
