jorenheit/bfcpu/doc/architecture.tex

\chapter{Synapse-191 Architecture} \label{sec:architecture}
\section{Hardware Overview} \label{sec:architecture:overview}
A true BISC implementation is a direct representation of the abstract BF machine described in Section \ref{sec:brainfck}, consisting of an array of memory-cells together with a pointer pointing to one of these cells. The pointer can move along the array while modifying its contents one step at a time. Figure \ref{fig:simplerepresentation} illustrates an example intermediate state of such a system. Consider the BF program ``\texttt{>>>>>+.}'', applied to the initial conditions shown in the example. The pointer would take 5 steps to the right, landing on cell 9 which contains the number 41. It will then increment and output this value, displaying 42 on the screen (assuming a screen of some sort is used as the output device and it is displaying numbers directly rather than interpreting them as ASCII).

\begin{figure}[H]
  \centering
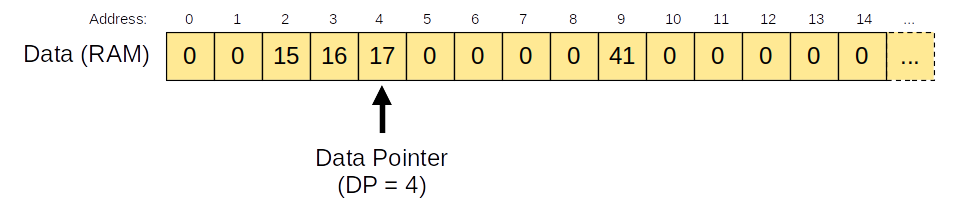
[picture p33: doc/img/simple_representation.png]
  
  \caption{Example state of a BF machine.}
  \label{fig:simplerepresentation}
\end{figure}

In a physical system, the data-tape would be a large memory space in RAM and the data pointer is a register that holds a value representing an address within that space. The pointer is moved by simply changing the value stored in the data pointer register. Modifying values in regular systems happens inside the ALU (Arithmetic and Logic Unit), which is capable of addition, subtraction, multiplication and many more mathematical and logical operations. No full-blown ALU is needed in a BISC implementation because of the simplicity of the modifying operations: values only need to be incremented or decremented (this goes for both the data pointer and the data itself), which can be done directly at the register level when up/down binary counters like the 74LS193 integrated circuit are used. The program (a sequence of BF instructions) is stored in Read-Only Memory (ROM), whereas the data is stored in Random Access Memory (RAM). Instructions (4-bit) are fed from ROM into a control unit (CU) together with a set of flags (see \ref{sec:architecture:flags}) that encode the state of the machine. Depending on the state and current instruction, the CU sets the appropriate control signals for each of the modules (memory, registers and I/O) in order for the system to perform the appropriate actions. Table \ref{tab:modules} lists the components of this BISC implementation, whereas Figure \ref{fig:architecture} shows the (conceptual) connections between those modules. In the sections below, each of these connections will be clarified further. The actual implementation on the logic/hardware level is described in Chapter \ref{sec:implementation}.

\begin{table}[H]
  \centering
  \begin{tabulary}{\linewidth}{|C|C|C|}
    \hline
    \textbf{Full Name} & \textbf{Short Name} & \textbf{Description} \\
    \hline
    Data Memory & RAM & Represents the data tape in the BF model; this is where the data is stored. \\\hline
    Program Memory & ROM & Separate from RAM, which is where the program's instructions are stored. \\\hline
    Data Pointer Register & DP & 16-Bit counting register that represents the pointer in the BF model; points to data in RAM. \\\hline
    Data Register & D & 8-Bit counting register that represents the value currently pointed to by the DP. \\\hline
    Instruction Pointer Register & IP & 16-Bit Counting register that contains the address of the current instruction; points to data in ROM.\\\hline
    Stack Pointer Register & SP & 8-Bit counting register that holds a value pointing inside the stack-space in RAM; used to implement loops.\\\hline
    Loop Skip Register & LS & 8-Bit counting register, used to skip over loops.\\\hline
    Flag Registers A \& B & FA/FB & 4-Bit registers used to buffer flag values that encode the state of the system. \\\hline
    Instruction Register & I & 4-Bit register that buffers the currently active instruction. \\\hline
    Control Unit & CU & System that translates the current instruction into sequences of control signals. \\\hline
    Register Driver & RD & Subsystem of the CU that centralizes increment and decrement operations. \\ \hline
  \end{tabulary}
  \caption{Overview of the modules that make up the physical BISC implementation.}
  \label{tab:modules}
\end{table}

\begin{figure}[H]
  \centering
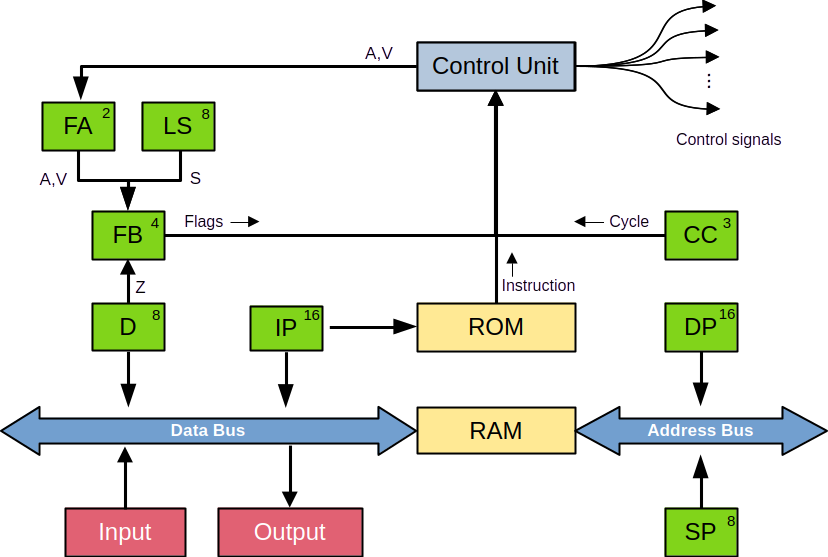
[picture p34: doc/img/bfcpu_architecture.png]
  
  \caption{Connections between modules in the BF processor.}
  \label{fig:architecture}
\end{figure}

\section{Flags} \label{sec:architecture:flags}
The state of the system is encoded using five flags: K, V, A, S, and Z. These flags were introduced to simplify control logic and enable performance optimizations during execution. Each flag serves a specific purpose, as explained below:

\paragraph{K-Flag} The K-flag is used for communication between the system and the IO Module, which run asynchronously. The flag is set by the IO Module and reset by the system to let each other know when certain data transactions have been completed.

\paragraph{A-Flag} The A-flag is set when the value in the DP register was modified, i.e.~when the data pointer has been shifted to a new cell. This is an architectural optimization to minimize the number of reads from and writes to RAM. Consider a long sequence of \texttt{+} or \texttt{-} instructions, which are very common in BF programs. A naive implementation of, for example, the \texttt{+} instruction, would consist of 3 steps: read the current value from RAM into D, increment the value in D, write the result back to RAM. However, when it is known that the data pointer has not been changed, we can keep operating on the copy in D. Only when the address has been changed (A was set), should we load the new value into D before modifying it.

\paragraph{V-Flag} The V-flag allows for another optimization, similar to that of the A-flag. Whenever the value in the D register has been modified, the V-flag is set. When the DP is about to change its value, through the \texttt{<} and \texttt{>} commands, the V-flag is checked. If set, we store the modified value back into RAM before moving the pointer. If not, the value hasn't changed and does not need to be synchronized into RAM. The number of cycles to complete long sequences of pointer move-commands is decreased substantially using this approach.

\paragraph{S-Flag} The S-flag is used to skip over blocks of code, primarily when skipping over loop-blocks. It is set when a loop should not be entered, causing all following commands to be ignored until the matching closing bracket is reached. Similarly, it is used at boot to skip over entire programs until the selected program is reached (when multiple BF programs have been written to the same program ROM).

\paragraph{Z-Flag} The Z-flag is set by the D register whenever it contains the value zero. This allows control-flow to branch on the value of the current cell, allowing for the implementation of loops.

\paragraph{Performance Gains} The number of cycles saved from using the A and V flags depends on the program that is running; programs with long and frequent sequences of \texttt{+}, \texttt{-}, \texttt{<} or \texttt{>} commands will benefit more than those with fewer or shorter sequences. To investigate the actual impact, a test suite of BF programs was put together and run in an emulator (a modified version of the C example shown in Listing \ref{lst:bfint}). The BF source for each of these programs is shown in Appendix \ref{sec:appendix:testsuite}. The modified interpreter contains a table of the number of cycles necessary to execute each instruction, depending on the aforementioned flags. This allows for a quantitative comparison between the naive implementation (load, modify, store) and the cache-like approach using the A and V flags. The results are shown in Figure \ref{fig:avresults}; a 16 to 22\% decrease was observed when using the A and V flags.

\begin{figure}[H]
  \centering
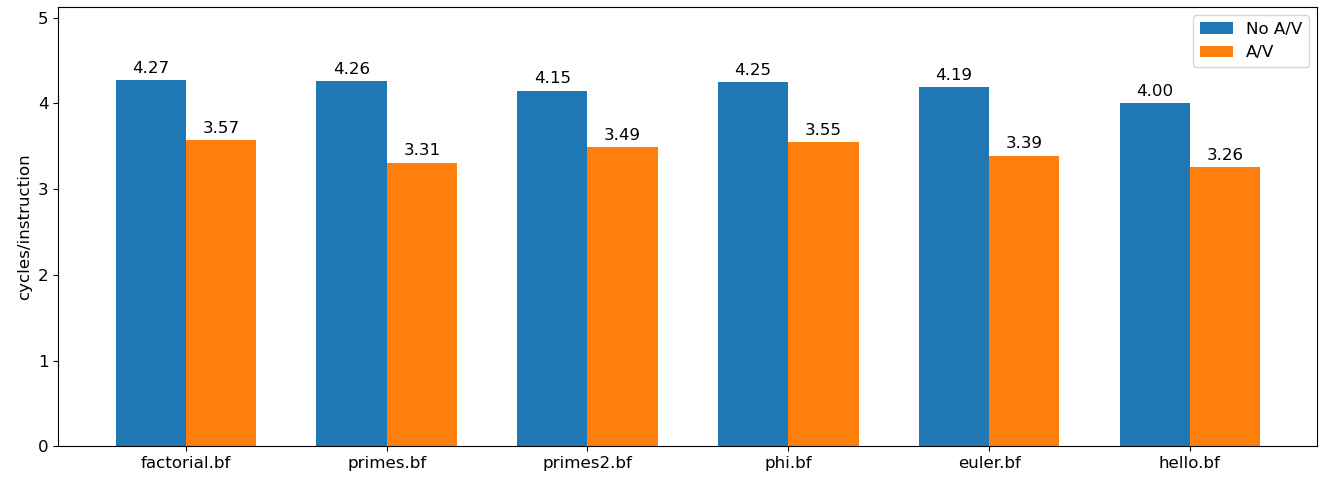
[picture p35: doc/img/avresults.png]
  
  \caption{The number of cycles per BF instruction drops by around 20\% when using the A and V flags.}
  \label{fig:avresults}
\end{figure}

\section{Data Pointer Register (DP)} \label{sec:architecture:dp}
The data-pointer corresponds to the pointer as specified in the BF-language. It points to some value in memory beyond the stack ($\ge$ 0x0100, see \ref{sec:architecture:sp}) and can be either incremented (moved right) or decremented (moved left) using the \texttt{>} and \texttt{<} instructions. Whenever the value pointed to by DP is modified by \texttt{+} or \texttt{-}, it is loaded into the D-register (see \ref{sec:architecture:d}), where it can be modified before being stored back into RAM.

\subsection*{Inputs}
The DP should be able to increment and decrement (corresponding to the \texttt{<} and \texttt{>} commands), and should be able to be enabled/disabled because of its connection to the address bus of the RAM (the Stack Pointer (SP; see \ref{sec:architecture:sp}) is also connected to this bus). While all other modules have the ability to be reset, the DP is the only register that can be reset (to 0x0100) at runtime. This is necessary during boot, when all the data cells need to be initialized to 0 (see \ref{sec:sequences:bootloading}).

\begin{enumerate}
\itemsep0em 
\item EN - Enable - Assert the stored 16-bit value onto the address bus.
\item U - Up - Increment the stored value.
\item D - Down - Decrement the stored value.
\item R - Reset - Reset the value to 0x0100, the start of the data section of RAM.
\end{enumerate}

\subsection*{Outputs}
\begin{enumerate}
\itemsep0em   
\item DP\_OUT - 16 bits, asserted onto the address bus when enabled (EN high).
\end{enumerate}

\section{Data Register (D)} \label{sec:architecture:d}
The data register holds a representation of the value currently pointed to by the DP and can be incremented and decremented (using the \texttt{+} and \texttt{-} commands). This register provides the Z-flag to signify that its current value is 0. Among other things, this flag can be used to determine whether or not to enter a loop.

\subsection*{Inputs}
\begin{enumerate}
\itemsep0em   
\item D\_IN - 8 bits - Data inputs, connected to the data bus.
\item EN - Enable - Assert the stored value onto the data bus.
\item LD - Load - Load data from the bus into D.
\item U - Up - Increment the stored value.
\item D - Down - Decrement the stored value.
\end{enumerate}

\subsection*{Outputs}
\begin{enumerate}
\itemsep0em 
\item D\_OUT - 8 bits - Data outputs, connected to the data bus.
\item SET\_Z - Set Zero Flag - High when the register stores a zero, connected to FB.
\end{enumerate}

\section{Instruction Pointer Register (IP)} \label{sec:architecture:ip}
The IP Register stores the instruction pointer (16-bits), which keeps track of the instruction that is currently being executed. It points to a certain address in ROM (which stores the program) and is usually incremented after each instruction has finished executing, in order to move to the next instruction. However, when the processor encounters the \texttt{[}-instruction (and a loop is entered), its value is stored in RAM at the location pointed to by the stack pointer (SP, see \ref{sec:architecture:sp}). When the matching \texttt{]}-instruction is encountered, this value can be loaded back into the IP in order to jump back to the start of the loop if needed.

\subsection*{Inputs}
\begin{enumerate}
\itemsep0em 
\item IP\_IN - 16 bits - Data inputs, connected to the data bus.
\item EN - Enable - Assert the stored value onto the data bus.
\item LD - Load - Load data from the bus into IP.
\item U - Up - Increment the stored value.
\end{enumerate}

\subsection*{Outputs}
\begin{enumerate}
\itemsep0em 
\item IP\_OUT - 16 bits - Data outputs, connected to the data bus and the address inputs of program-ROM;
\end{enumerate}

\section{Stack Pointer Register (SP)} \label{sec:architecture:sp}
The stack is the first part of RAM (addresses 0x0000 - 0x00FF) and is reserved to keep track of addresses in ROM that might need to be jumped to when flow encounters a loop-end instruction (\texttt{]}). The stack-pointer (SP) points to an address in this space; it is incremented whenever a new jump-address is pushed to the stack and decremented whenever an address is popped off the stack. In this implementation, the SP is an 8-bit value, which means that at most 256 different values can be stored onto the stack before the SP overflows (wraps around back to 0) and starts overwriting previous values. This would happen if a BF program was loaded that has more than 256 nested \texttt{[]}-pairs (and each of those loops is entered). Although possible, it is very unlikely to happen for the simple programs we intend to run. In Chapter \ref{sec:results}, where the required stack size is measured for a suite of test programs, this is confirmed; the largest value found for any required stack size in these programs was only 17, leaving plenty of space for even more complex programs.
  
\subsection*{Inputs}
\begin{enumerate}
\itemsep0em 
\item EN - Enable - Assert the stack-pointer onto the address-bus.
\item U - Up - Increment the stack-pointer.
\item D - Down - Decrement the stack-pointer.
\end{enumerate}

\subsection*{Outputs}
\begin{enumerate}
\itemsep0em 
\item SP\_OUT - 8 bits - connected to the address bus of RAM.
\end{enumerate}

\section{Loop Skip Register (LS)} \label{sec:architecture:ls}
The Loop Skip (LS) register is a counter that indicates whether or not we're in the process of skipping a loop. In BF, a loop (\texttt{[}) is only entered when the value currently pointed to is nonzero. In the case that it is zero, execution resumes beyond its matching loop-end instruction (\texttt{]}). When it is determined that a loop must be skipped (based on the Z-flag provided by the D-register), the LS register is incremented from 0 to 1 and the S-flag is set. This flag will remain set as long as the value in LS is nonzero, indicating that the system is in a skip-state. Subsequent instructions are then skipped until either another (nested) loop-start or a closing loop-end is encountered. On the former, the LS is incremented again while on the latter the LS is decremented. This has the effect that the LS becomes 0 again after the \texttt{]} that matches the original \texttt{[} which led to the skip. Normal execution occurs as soon as LS has become 0 again and the S-flag is reset back to 0.

\subsection*{Inputs}
\begin{enumerate}
  \itemsep0em
\item U - Up - Increment the stored value.
\item D - Down - Decrement the stored value.
\end{enumerate}

\subsection*{Outputs}
\begin{enumerate}
\itemsep0em 
\item SET\_S - Skip flag - set when its value is nonzero, connected to FB.
\end{enumerate}

\section{Flag Registers (FA and FB)} \label{sec:architecture:flag-registers}
\paragraph{FA} The first flag register (FA) holds two flag values, A and V, which are used to indicate that either the address (A) or value (V) has changed during one of the previous instructions. For instance, if D was incremented (or decremented), the V-flag is set to indicate a change of the \emph{value} being pointed to: the value in RAM is now outdated. When DP is incremented (or decremented), the A-flag is set to indicate a change of the current \emph{address}, meaning that the value in D is now outdated. For a more detailed description of the function and application of these flags, refer to Sections \ref{sec:sequences:+-} and \ref{sec:sequences:<>}.

\paragraph{FB} On the zeroth cycle of every instruction, these flags are latched into the FB register together with the Z and S-flags (set by the D and LS registers) for a total of 4 flags. This happens simultaneously with loading the next instruction into the instruction register (I, see \ref{sec:architecture:i}) and is not refreshed until loading the next instruction to make sure that the flag-state remains constant throughout the execution of the current instruction.

\paragraph{K-Flag} The previously mentioned K-flag is specific to interactions with the IO-module and is not buffered in either of the flag registers. It is discussed more thoroughly in Sections \ref{sec:sequences:output} and \ref{sec:sequences:input}.

\subsection*{Inputs}
\begin{enumerate}
\itemsep0em 
\item SET\_A - Assert the address-change-flag onto FA.
\item SET\_V - Assert the value-change-flag onto FA.
\item LD(FA) - Load A and V into FA (if set).
\item LD(FB) - Load A, V (previously buffered in FA), Z and S (from D and LS) into FB. 
\end{enumerate}

\subsection*{Outputs}
\begin{enumerate}
\itemsep0em 
\item F\_OUT - 4 bits - connected to the instruction decoder inside the Control Unit.
\end{enumerate}

\section{Instruction Register (I)} \label{sec:architecture:i}
The instruction register I buffers the current instruction pointed to by the IP. The instruction is loaded from program ROM into I at the start of every new instruction (cycle 0), right after IP has been incremented. Its outputs are used as part of the microcode address that goes into the decoder of the CU (see Figure \ref{fig:decoder} in Chapter \ref{sec:sequences}).

\subsection*{Inputs}
\begin{enumerate}
\itemsep0em 
\item LD(I) - Load the instruction pointed to by IP.
\end{enumerate}

\subsection*{Outputs}
\begin{enumerate}
\itemsep0em 
\item I\_OUT - 4 bits - connected to the instruction decoder inside the Control Unit.
\end{enumerate}

\section{Register Driver} \label{sec:architecture:registerdriver}
Rather than having a separate signal for each of the INC/DEC inputs of each register (e.g.~INC\_D, INC\_LS, etc.), a driver module was designed (see \ref{sec:implementation:registerdriver}) to drive registers that support modification of their contents (increment/decrement). In addition to a universal INC/DEC signal, three Register Select (RS) bits are used to index the target register. This approach has two advantages:
\begin{enumerate}
\item It decreases the number of control signals needed;
\item The logic needed to drive the counting registers (74LS193) only needs to be implemented once.
\end{enumerate}

The driver module accepts 5 control signals: 3 register-select signals (RS0 through RS2), INC and DEC. Using 3 register-select signals, up to 8 ($2^3$) registers can be selected, though only 5 need to be driven by the driver. Table \ref{tab:registers} contains an overview of each of the registers and the control signals they support. When all RS-signals are off, no register is selected.

\begin{table}[H]
  \centering
  \begin{tabular}{c|c|c|c|c|c|c}
    Register & \#Bits & EN  & LD  & INC  & DEC & RS2$|$RS1$|$RS0 \\ \hline 
    D        & 8      & x   & x   & x    & x   & 0$|$0$|$1 \\
    DP       & 16     & x   &     & x    & x   & 0$|$1$|$0 \\ 
    SP       & 8      & x   &     & x    & x   & 0$|$1$|$1 \\ 
    IP       & 16     & x   & x   & x    &     & 1$|$0$|$0 \\ 
    LS       & 8      &     &     & x    & x   & 1$|$0$|$1 \\ 
    FA       & 4      &     & x   &      &     & not addressable \\ 
    FB       & 4      &     & x   &      &     & not addressable  \\
    I        & 4      &     & x   &      &     & not addressable \\
  \end{tabular}
  \caption{Control signals available on each of the registers. The flag and instruction registers are not connected to the register driver.}
  \label{tab:registers}
\end{table}

\subsection*{Inputs}
\begin{enumerate}
  \itemsep0em
\item RS0 - Register Select Bit 0
\item RS1 - Register Select Bit 1
\item RS2 - Register Select Bit 2
\item INC - Increment selected register
\item DEC - Decrement selected register
\end{enumerate}

\subsection*{Outputs}
\begin{enumerate}
\itemsep0em 
\item U - 5 bits - Up signals - Connected to the U input of all registers that support the INC operation.
\item D - 5 bits - Down-signals - Connected to the D input of all registers that support the DEC operation.
\end{enumerate}

\section{Cycle Counter (CC)} \label{sec:architecture:cc}
Almost every BF instruction requires multiple cycles to complete. Therefore, in addition to the instruction and state, a cycle counter is used to determine the control signals that should be sent out at each step of the instruction. This cycle counter is implemented as a 3-bit counting register (allowing for at most 8 cycles per instruction) that increments on every clock cycle and sends its output to the control unit. Its only control signal is the clear signal (CLR) which resets the count to 0, in order to fetch the next instruction.

\subsection*{Inputs}
\begin{enumerate}
\itemsep0em
\item CLR - Cycle Reset - Reset the count to 0;
\end{enumerate}

\subsection*{Outputs}
\begin{enumerate}
\itemsep0em
\item CC\_OUT - 3 bits - Current value of the register (0--7).
\end{enumerate}

\section{Data Memory (RAM)}  \label{sec:architecture:ram}
RAM is divided into two parts: stack and data. The first 256 bytes (0x0000 - 0x00FF) make up the stack and are indexed by the stack pointer (\ref{sec:architecture:sp}). The data (corresponding to the BF tape) is stored at addresses 0x0100 through 0xFFFF and is indexed by the data pointer (\ref{sec:architecture:dp}). Its address lines are connected to the address bus, which in turn receives its value from either the DP or the SP. Its data lines are bidirectional and are connected to the data bus. When the Write Enable (WE) signal is active, data can be read from the bus and written into RAM. When instead the Output Enable (OE) signal is active, the current value in RAM (determined by the address on the address bus) is asserted onto the data bus.

\subsection*{Inputs}
\begin{enumerate}
\itemsep0em 
\item DATA\_IN - 16 bits - Input data, connected to the data bus.
\item ADDR\_IN - 16 bits - Address lines, connected to the address bus;
\item OE - Output Enable - Assert the value stored at the current address onto the data bus;
\item WE - Write Enable - Write the value on the data bus into the current address.
\end{enumerate}

\subsection*{Outputs}
\begin{enumerate}
\itemsep0em 
\item DATA\_OUT - 16 bits - Output data, connected to the data bus (same physical lines as DATA\_IN).
\end{enumerate}

\section{Program Memory (ROM)} \label{sec:architecture:rom}
The actual BF instructions are stored in Read-Only-Memory (ROM) and are addressed by the IP (\ref{sec:architecture:ip}). A 4-bit instruction is stored at the address pointed to by the IP. It is sent to the CU where it is used to determine the set of control signals, together with the flags and cycle counter.

\subsection*{Inputs}
\begin{enumerate}
\itemsep0em 
\item ADDR\_IN - 16 bits - Address lines, connected to the IP.
\end{enumerate}

\subsection*{Outputs}
\begin{enumerate}
\itemsep0em 
\item INS\_OUT - 4 bits - Instruction data, connected to the CU.
\end{enumerate}

\section{Screen (SCR)}  \label{sec:architecture:scr}
The output module (which is assumed to be a screen) will be attached to the data bus and will display whatever is on the bus when enabled using the EN signal. Because the output is handled asynchronously by some peripheral that will, from the perspective of the CPU, be viewed as a black box, it needs a flag to acknowledge a successful data-transfer. This is done through the K-flag, which is set by the peripheral after reading data from the data bus (this flag is shared with the input device for a similar purpose). The K-flag can only be reset by the CU using the CLR\_K signal, indicating that the transfer procedure has been completed.
\subsection*{Inputs}
\begin{enumerate}
\itemsep0em 
\item DATA\_IN - 8 bits - connected to the data bus.
\item EN: Enable - Display the contents of the bus. The format of the output (ASCII, hex, etc) may vary depending on the implementation of the output device.
\item CLR\_K - Clears the K-flag - connected to the CU (this signal is shared with the input module, KB; see \ref{sec:architecture:kb}).
\end{enumerate}

\subsection*{Outputs}
None.

\section{Keyboard (KB)} \label{sec:architecture:kb}
The input device to the computer is assumed to be a keyboard of some sort\footnote{At a later stage in the process of building the CPU, a Random Number Generator (RNG) was implemented as a second input device to support a common Brainfuck extension, where the \texttt{?}-command is used to generate a random number in the currently active cell.} that implements a buffer from which some 8-bit value can be requested. The control unit can assert the enable signal of this device and should then wait until the K-flag is set, at which point the data should be ready to be read from the data bus. It is left up to the implementation of the peripheral to decide what to do when there is nothing in the input buffer (either wait for user input or return 0). The K-flag, which is shared with the output peripheral, is reset to communicate that the data has been transferred and the input device can yield control of the data bus back to the system.

\subsection*{Inputs}
\begin{enumerate}
\itemsep0em 
\item EN - Enable - Make the contents of the input buffer available on the data bus.
\item CLR\_K - Clears the K-flag - connected to the CU (this signal is shared with the output module, SCR; see \ref{sec:architecture:scr}).
\end{enumerate}

\subsection*{Outputs}
\begin{enumerate}
\itemsep0em 
\item DATA\_OUT - 8 bits - Output data, connected to the data bus.
\end{enumerate}

\section{Control Unit} \label{sec:architecture:cu}
Each of the aforementioned components/modules has one or more control inputs that determine what happens on the next clock cycle. For example, some register-modules can be told to load a value from their input, increment or decrement the currently stored value, or do nothing at all. It is the Control Unit (CU) that supplies the appropriate control signals to each of the modules before the next clock pulse occurs, depending on the current instruction and state determined by the flags and cycle counter. The implementation details of how this is done in hardware are discussed in Chapter \ref{sec:implementation}.

\subsection*{Inputs}
\begin{enumerate}
\itemsep0em
\item CC\_IN - 3 bits - Cycle counter input lines.
\item INS\_IN - 4 bits - Instruction input lines (from program ROM).
\item FLAGS\_IN - 5 bits - Flag input lines (from FB and K).
\end{enumerate}

\subsection*{Outputs}
\begin{enumerate}
\itemsep0em 
\item HLT - Halt Clock
\item RS0 - Register Select, bit 0
\item RS1 - Register Select, bit 1
\item RS2 - Register Select, bit 2
\item INC - Increment selected register
\item DEC - Decrement selected register
\item CLR\_DP - Reset DP
\item EN\_SP - Enable SP to address bus \footnote{Note that there is no EN\_DP since this signal is mutually exclusive with EN\_SP; whenever one is set, the other is unset and vice versa.}
\item OE\_RAM - Output Enable RAM
\item WE\_RAM - Write Enable RAM
\item EN\_IN - Enable input (keyboard) to data bus
\item EN\_OUT - Enable output device
\item SET\_V - Set V-flag in FA
\item SET\_A - Set A-flag in FA
\item LD\_FBI - Load FB and I
\item LD\_FA - Load FA
\item EN\_IP - Enable IP
\item EN\_D - Enable D to data bus
\item LD\_D - Load D
\item LD\_IP - Load IP
\item CLR\_CC - Reset Cycle Counter
\item CLR\_K - Clear the K-flag in the IO module
\item END - Program End Signal
\item ERR - Error Signal
\end{enumerate}
