jorenheit/bfcpu/doc/flashback.tex

\chapter{Flashback} \label{sec:appendix:flashback}
\newpage

\vfill
\begin{figure}[H]
  \center
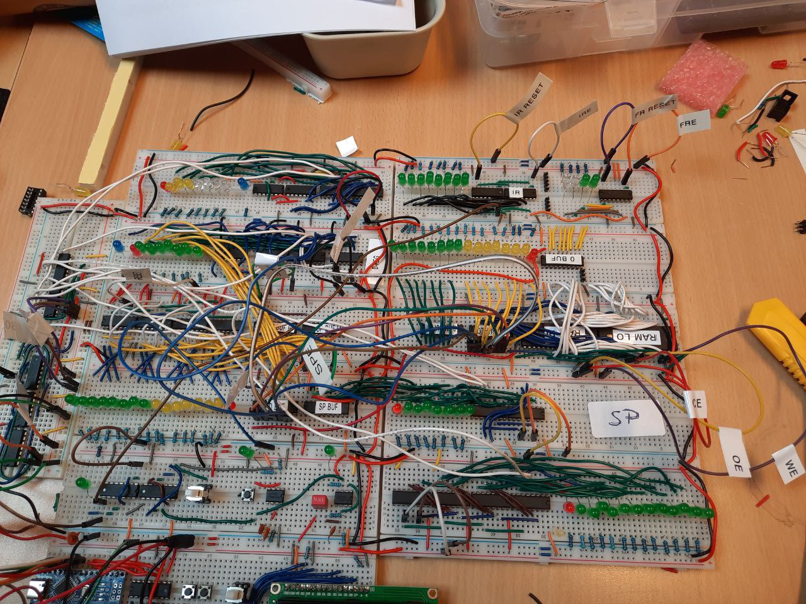
[picture p44: doc/img/pics/9.jpg]
  
  \caption{Early prototyping in 2024.}
  \label{fig:prototype1}  
\end{figure}
\vfill
\begin{figure}[H]
  \centering
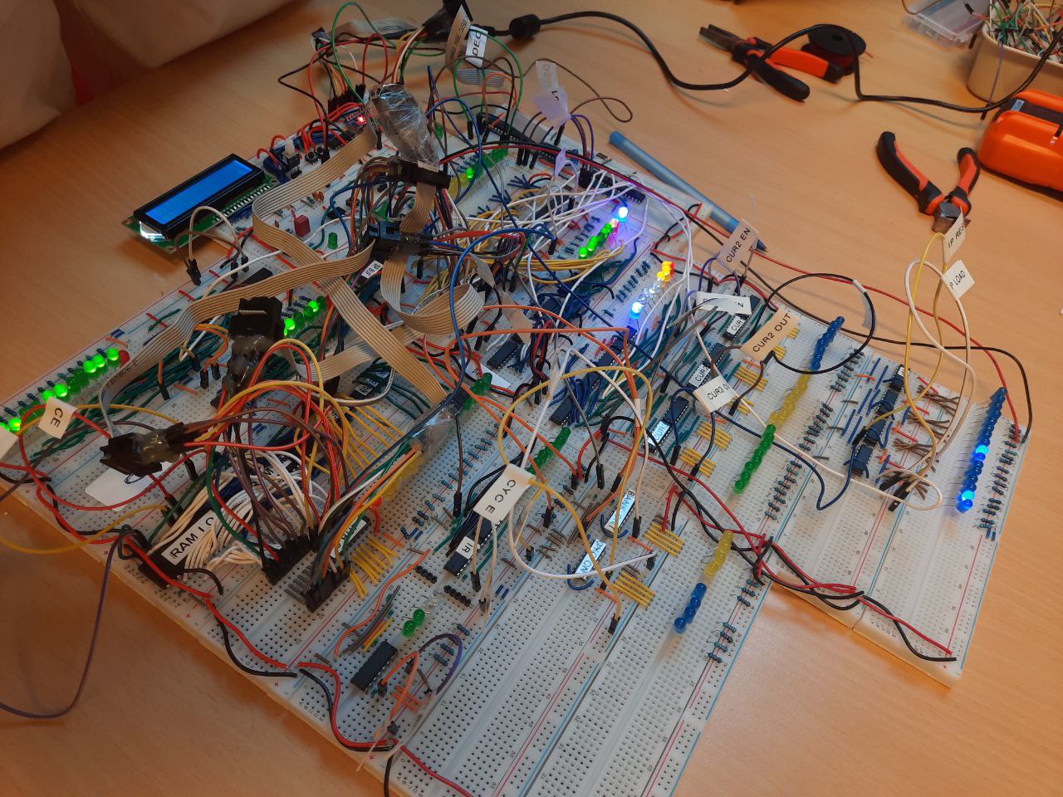
[picture p45: doc/img/pics/10.jpg]
  
  \caption{Early prototyping in 2024.}
  \label{fig:prototype2}
\end{figure}
\vfill

\newpage

\vfill
\begin{figure}[H]
  \centering
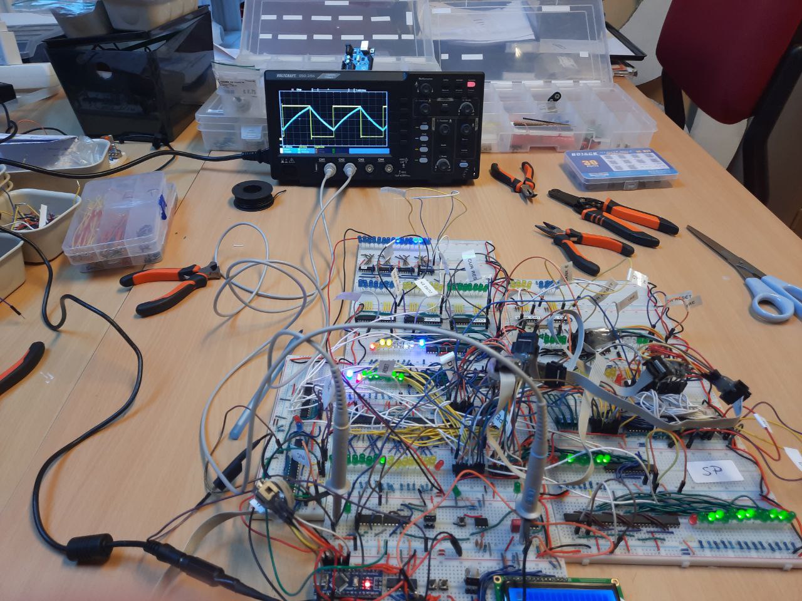
[picture p46: doc/img/pics/11.jpg]
  
  \caption{Early prototyping in 2024.}
  \label{fig:prototype3}
\end{figure}
\vfill
\begin{figure}[H]
  \centering
  
  \caption{Early prototyping in 2024.}
  \label{fig:messy1}
\end{figure}
\vfill

\newpage

\vfill
\begin{figure}[H]
  \centering
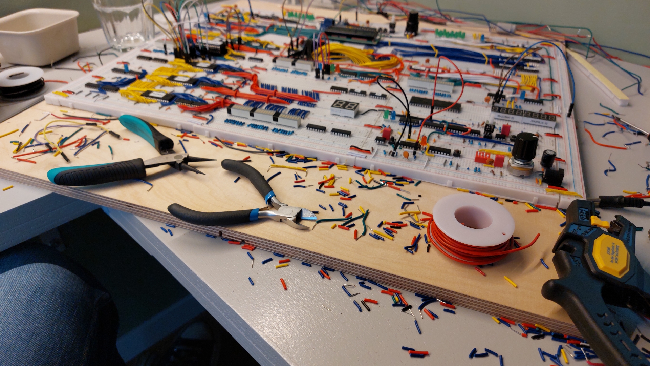
[picture p47: doc/img/pics/IMG-20250208-WA0007.jpeg]
  
  \caption{Wire stripping can quickly lead to a mess.}  
  \label{fig:messy2}
\end{figure}
\vfill
\begin{figure}[H]
  \centering
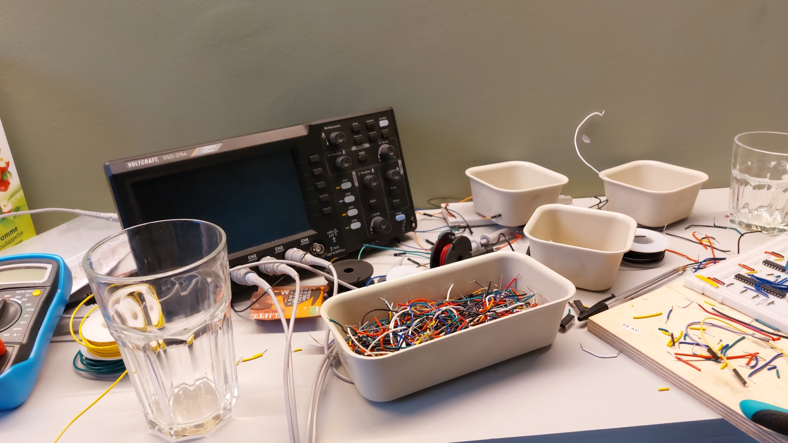
[picture p48: doc/img/pics/IMG-20250208-WA0010.jpeg]
  
  \caption{A typical view when building and debugging the system.}
  \label{fig:earlybuild1}
\end{figure}
\vfill

\newpage

\vfill
\begin{figure}[H]
  \centering
  
  \caption{Registers and RAM first put together, the system starts to take shape.}  
  \label{fig:earlybuild2}    
\end{figure}
\vfill
\begin{figure}[H]
  \centering
  
  \caption{An early version of the IO module, including an Arduino Nano, was added to the system.}
  \label{fig:earlybuild3}
\end{figure}
\vfill

\newpage

\vfill
\begin{figure}[H]
  \centering
  
  \caption{The (segmented) control unit starts to take shape. The bottom-middle section contains the logic for sequentially fetching the three parts of the control word from different sections in the MC EEPROM chip.}
  \label{fig:earlybuild4}
\end{figure}
\vfill
\begin{figure}[H]
  \centering
  
  \caption{The (segmented) control unit starts to take shape even more. A display for showing the current instruction was added (7-segment display, bottom left).}
  \label{fig:earlybuild5}
\end{figure}
\vfill

\newpage

\vfill
\begin{figure}[H]
  \centering
  
  \caption{First (somewhat) working version of the system.}
  \label{fig:firstbuild}
\end{figure}

\vfill
\begin{figure}[H]
  \centering
  
  \caption{Final build of the system, including 3D-printed parts and many pretty lights.}
  \label{fig:finalbuild}
\end{figure}
\vfill
