jorenheit/bfcpu/doc/references.tex

\begin{thebibliography}{99} \label{resources}
\bibitem{bfwiki} Wikipedia, \emph{Brainfuck}, https://en.wikipedia.org/wiki/Brainfuck
\bibitem{esolangs-bf} Esolangs, \emph{Brainfuck}, https://esolangs.org/wiki/Brainfuck
\bibitem{esolangs-rbf} Esolangs, \emph{Brainfuck}, https://esolangs.org/wiki/Random\_Brainfuck
\bibitem{vonneumann-wiki} Wikipedia, \emph{Von Neumann Architecture},\\https://en.wikipedia.org/wiki/von\_neumann\_architecture
\bibitem{beneater} Ben Eater, \emph{Build an 8-bit computer from scratch}, https://eater.net/8bit
\bibitem{stefanheule} Stefan Heule, \emph{How Many x86-64 Instructions Are There Anyway?},\\https://stefanheule.com/blog/how-many-x86-64-instructions-are-there-anyway/, 2016
\bibitem{danielmangum} Daniel Mangum, \emph{RISC-V Bytes: Introduction to Instruction Formats},\\https://danielmangum.com/posts/risc-v-bytes-intro-instruction-formats/, 2021
\bibitem{hello} unknown author, \emph{Wikipedia} https://en.wikipedia.org/wiki/Brainfuck
\bibitem{brainfix} Joren Heit, \emph{GitHub} https://github.com/jorenheit/brainfix
\bibitem{acus} Joren Heit, \emph{GitHub} https://github.com/jorenheit/acus
\bibitem {firstfit} Wikipedia, \emph{First-fit bin packing} https://en.wikipedia.org/wiki/First-fit\_bin\_packing
\bibitem{phi} Marijn Stevens, \emph{GitHub}, \\https://github.com/MarijnStevens/brainfuck-collection/blob/master/bf/golden2.b
\bibitem{euler} Daniel B. Cristofani, \emph{brainfuck.org}, https://brainfuck.org/e.b
\bibitem{primes} Troemax, \emph{Reddit}, \\https://www.reddit.com/r/brainfuck/comments/847vl0/prime\_number\_generator\_in\_brainfuck/
\bibitem{primes2} Alexandru, \emph{Stack Exchange}, \\https://codegolf.stackexchange.com/questions/84/interpret-brainfuck
\bibitem{tictactoe} Mixtela, \emph{GitHub}, https://github.com/mitxela/bf-tic-tac-toe
\bibitem{ls00} Texas Instruments, \emph{Quadruple 2-Input Positive-NAND Gates}, 74LS00 Data Sheet, Dec. 1983 (Rev. 2003)
\bibitem{ls02} Texas Instruments, \emph{Quadruple 2-Input Positive-NOR Gates}, 74LS02 Data Sheet, Dec. 1983 (Rev. 1988)
\bibitem{ls04} Texas Instruments, \emph{Hex Inverters}, 74LS04 Data Sheet, Dec. 1983 (Rev. 2004)
\bibitem{ls08} Texas Instruments, \emph{Quadruple 2-Input Positive-AND Gates}, 74LS08 Data Sheet, Dec. 1983 (Rev. 1988)
\bibitem{ls14} Texas Instruments, \emph{Hex Schmitt-Trigger Inverters}, 74LS14 Data Sheet, Dec. 1983 (Rev. 2016)
\bibitem{ls32} Texas Instruments, \emph{Quadruple 2-Input Positive-OR Gates}, 74LS32 Data Sheet, Dec. 1983 (Rev. 1988)
\bibitem{ls48} Texas Instruments, \emph{BCD-To-Seven-Segment Decoders/Drivers}, 74LS48 Data Sheet, Mar. 1974 (Rev. 1988)
\bibitem{ls74} Texas Instruments, \emph{Dual D-Type Positive-Edge-Triggered Flip-Flops with Preset and Clear}, 74LS74 Data Sheet, Oct. 1983 (Rev. 1988)
\bibitem{ls76} Texas Instruments, \emph{Dual JK-Flip-Flops with Preset and Clear}, 74LS76 Data Sheet, Dec. 1983 (Rev. 1988)
\bibitem{ls86} Texas Instruments, \emph{Quadruple 2-Input Exclusive-OR Gates}, 74LS86 Data Sheet, Dec. 1972 (Rev. 1988)
\bibitem{ls123} Texas Instruments, \emph{Retriggerable Monostable Multivibrators}, 74LS123 Data Sheet, Dec. 1983 (Rev. 1988)
\bibitem{ls138} Texas Instruments, \emph{3-Line to 8-Line Decoders/Demultiplexers}, 74LS138 Data Sheet, Dec. 1972 (Rev. 1988)
\bibitem{ls157} Texas Instruments, \emph{Quadruple 2-Line to 1-Line Data Selectors/Multiplexers}, 74LS157 Data Sheet, Dec. 1982 (Rev. 2022)
\bibitem{ls161} Texas Instruments, \emph{Synchronous 4-Bit Counters}, 74LS161 Data Sheet, Oct. 1976 (Rev. 1988)
\bibitem{ls173} Texas Instruments, \emph{4-Bit D-Type Registers with 3-State Outputs}, 74LS173 Data Sheet, Oct. 1976 (Rev. 1999)
\bibitem{ls193} Texas Instruments, \emph{Synchronous 4-Bit Up/Down Counters}, 74LS193 Data Sheet, Dec. 1972 (Rev. 1988)
\bibitem{ls245} Texas Instruments, \emph{Octal Bus Transceivers With 3-State Outputs}, 74LS245 Data Sheet, Oct. 1976 (Rev. 2016)
\bibitem{hc595} Texas Instruments, \emph{8-Bit Shift Registers With 3-State Output Registers}, 74HC595 Data Sheet, Dec. 1982 (Rev. 2021)
\bibitem{555} Texas Instruments, \emph{xx555 Precision Timers}, NE555 Data Sheet, Sep. 1973 (Rev. 2014)
\bibitem{28c64} Atmel, \emph{64K (8K x 8) Parallel EEPROM with Page Write and Software Data Protection}, AT28C64B Data Sheet, 2009
\bibitem{6c4008} Alliance Memory Inc., \emph{512K X 8 BIT LOW POWER CMOS SRAM}, AS6C4008 Data Sheet, Aug. 2009
\bibitem{14078B} Motorola, \emph{B-Suffix Series CMOS Gates}, MC14078B Data Sheet, Aug. 2009
\bibitem{7226B} Intersil, \emph{8-Digit, Multi-Function, Frequency Counter/Timer}, ICM7226B Data Sheet, Aug. 2009
\end{thebibliography}
