jorenheit/bfcpu/website/content/tex/control_sequences.tex

\chapter{Opcodes and Control Sequences} \label{sec:sequences}

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

In Section (\ref{sec:architecture:overview}) it was mentioned that the BF program is stored in ROM as a series of opcodes, each of which corresponds 1-to-1 to a BF command. However, the system needs to perform some additional non-BF actions to prepare itself for execution. For one, the data-tape is assumed to be zero-initialized; a freshly powered on SRAM chip will contain random garbage, so we need to take care of that before the first BF command is executed. Moreover, the system is designed to accept a ROM chip containing multiple programs for convenience. This means that before blindly running the first program, there must exist some mechanism that looks for the index corresponding to the program the user is intending to run. To account for these issues, the binary format on the EEPROM expected by the system is as listed below. The \texttt{bfasm} utility was designed to translate any canonical BF source to the corresponding opcodes and dresses them with the necessary housekeeping instructions. The control sequences that implement the initialization and bootloading steps are further discussed in Section \ref{sec:sequences:bootloading}.

\begin{enumerate}
\item One or more INIT instructions to (partially) initialize the data-tape.
\item One INIT\_FINISH instruction to return the datapointer to the start of the datasection. This instruction also signals to the IO module that the system has been fully initialized.
\item One LOAD\_SLOT instruction. The program index is supplied to the bus by the IO module and used to move the IP to the start of the corresponding program.
\item A sequence of BF programs, each preceded by a PROG\_START instuction and ended by a PROG\_END instruction. The PROG\_START instructions serves as a barrier between programs and is used to skip over programs in order to find the correct program to run. The PROG\_END simply halts the clock and lights up an LED to indicate successful termination of the program.
\end{enumerate}

\section{Instruction Decoding}
By setting the control signals as described in Section \ref{sec:architecture} appropriately, modules can work together to perform each of the BF and supporting instructions. The Control Unit implements this as a lookup-table in 3 ROM chips, where the instruction taken from program ROM (4 bits), flags (5 bits) and cycle counter (3 bits) act as an address into this table (Figure \ref{fig:decoder}). Given that the CU has to be able to supply a total of 24 different control signals, three 8-bit EEPROM chips have been used to store the microcode lookup-table for a maximum of 24 signals (all of them used). More details on the implementation can be found in Section \ref{sec:implementation:cu}. 
\begin{figure}[h]
  \centering
  
  \caption{Decoding an instruction: the current instruction, flags and cycle-count are used as an index to the three ROM chips that output the control signals corresponding to the current state of the system.}
  \label{fig:decoder}
\end{figure}

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

\section{Cycle 0: Instruction Fetch}
The first cycle of each instruction is identical\footnote{The OUT instruction is slightly different but this can be ignored for now. For more information, refer to \ref{sec:sequences:output}}: A, V, S and Z are loaded into the FB register and the current instruction (pointed to by IP) is loaded from program ROM into the instruction register (I). This provides the CU with all the necessary information to determine the control signals for cycle 1: LD\_FB, LD\_I.

\section{Modifying Data: \texttt{+} and \texttt{-}} \label{sec:sequences:+-}
\paragraph{PLUS} The sequence of instructions necessary to execute a \texttt{+} command depends on the state of the system. Three different scenario's have to be taken into account:

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

\item (A = 1, S = 0) - However, when the A-flag \emph{was} set, this means that the address has recently changed and the value inside D does not correspond to the value pointed to by the DP in RAM. We therefore need to fetch the current value from RAM by enabling the DP register on cycle 1, enabling the RAM to output its content on the databus and loading the resulting value into D.
  From hereon, the control signals are identical to those described above in the case where A was not set.

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

\section{Moving the Pointer: \texttt{<} and \texttt{>}} \label{sec:sequences:<>}
\paragraph{RIGHT} Moving the data pointer one cell to the right requires similar instructions compared to PLUS instruction, the difference being that we increment the DP-register rather than the D-register. Similarly, we consider three different scenario's, branching on the V-flag instead of the A-flag:

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

  \begin{labeledenum}{Cycle}
  \item INC, RS1, SET\_A, LD\_FA
  \item INC, RS2, CR
  \end{labeledenum}
  
\item (V = 1, S = 0) - In the case that V \emph{was} set during one of the previous instructions, we need to write the updated value (present in the D-register) back to RAM before moving the pointer. This is achieved by enabling the value in D onto the databus and setting the RAM module to write-mode. Furthermore, the V-flag needs to be cleared. This is achieved by loading FA without setting any signals; this will effectively reset both A and V back to zero.

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

\end{labeledenum}

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

\section{Conditional Jumping: \texttt{[} and \texttt{]}}
These are by far the most complicated instructions that require lots of additional logic. Because the BF instruction set lacks a JMP-instruction where some argument holds the destination address, the computer has to store the address of the opening \texttt{[}-command in case it needs to loop back when the time comes. When a loop is skipped, the LS (Loop Skip) register is used to determine when execution should resume. This leads to multiple scenario's depending on the state of A, Z and S.
  
  \paragraph{LOOP\_START} 

\begin{labeledenum}{Scenario}
  \item (A = 0, Z = 1, S = 0) - In the first scenario, where A is not set (the D-register is up-to-date) and the Z-flag is set, we can immediately conclude that this loop should be skipped. Hence, the LS-register is incremented and the next instruction is loaded (to be ignored until the LS-register becomes 0 again). Since LS is addressed by the register driver at address 101, both RS0 and RS1 need to be asserted to the register driver. In the second cycle, the IP is incremented and the cycle-counter is reset to move to the next instruction.

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

  \item (A = 0, Z = 0, S = 0) - In the second scenario, the A-flag is still not set but the Z-flag for the D-register is not set either, meaning that control \emph{should} enter the loop (the current value is nonzero). It takes 3 cycles to do so: increment the stack-pointer (cycle 1), write the current IP (address 011) to this address on the stack by enabling (cycle 2) and move to the next instruction (cycle 3). The corresponding control sequences are therefore:

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

    \begin{labeledenum}{Cycle}
    \item OE\_RAM, LD\_D, LD\_FA, CR
    \end{labeledenum}
    
  \item (S = 1) - In the final scenario, we are in the process of skipping code, indicated by the S-flag (S = 1). In this case, we have encountered a nested loop that needs to be skipped over, so we increment the LS-register once more to account for another pair of nested \texttt{[]}'s (cycle 1) and then continue to the next instruction (cycle 2). The control sequences are therefore identical to those in the first scenario:
    
    \begin{labeledenum}{Cycle}
    \item INC, RS0, RS2
    \item INC, RS2, CR
    \end{labeledenum}

\end{labeledenum}

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

      \begin{labeledenum}{Cycle}
      \item OE\_RAM, LD\_D, LD\_FA, CR
      \end{labeledenum}
      
    \item (S = 1) - Finally, when already in the process of skipping a loop, the LS-register is decremented before moving to the next instruction before resetting the cycle counter and incrementing the IP.
      
      \begin{labeledenum}{Cycle}
      \item DEC, RS0, RS2
      \item INC, RS2, CR
      \end{labeledenum}
  \end{labeledenum}

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

  \caption{}
  \label{fig:loopalg}
\end{figure}

\section{Output: \texttt{.}} \label{sec:sequences:output}

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

\begin{labeledenum}{Step}
\item First, the data is loaded into D if not already present (A=1). The CU then asserts the EN\_OUT signal and enables D such that its contents appear on the databus. It will keep EN\_OUT high and keep the data asserted onto the data bus for as long as necessary, as indicated by the K-flag. 
\item The output module notices the EN\_OUT signal and reads the value from the bus. When done, it sets the K-flag.
\item When K is seen to go high, the bus is de-asserted, K is reset and the transaction has finished.
\end{labeledenum}

\paragraph{Implementation}
When the OUT instruction hits its first cycle, it will first synchronize D with RAM if the A-flag or V-flag is set. This is necessary because these flags are then both set to 1 to indicate a wait-state; synchronizing D allows these flags to both be safely reset when the instruction has finished. In cycle 2, A and V are latched into FB and the CC is reset, in order for the microcode to branch into the wait-loop on the next cycle 0. Now that the system is back in cycle 0 with both A and V set the system goes into a busy-loop. The EN\_OUT and EN\_D signals are continuously asserted for as long as the K-flag is still low; an immediate cycle reset leaves the system in cycle 0.  All other commands reload the flags and instruction in cycle 0; to maintain stable data on the bus without interruptions (due to resetting to the default cycle 0), we need the special A=V=1 state to encode this situation. When K finally goes high (K does not have to be latched, so its current value is always available), cycle 0 branches to a different sequence, where the A, V and K flag are cleared and the IP is incremented to move to the next instruction.

\begin{labeledenum}{Scenario}
  \item (A = 0, V = 0) - No need to synchronize; go into wait-state by setting A and V to 1. Latch these in FB immediately to make them available on the next cycle 0.
    \begin{labeledenum}{Cycle}
    \item EN\_A, EN\_V, LD\_FA
    \item LD\_FB, CR
    \end{labeledenum}

  \item (A = 0, V = 1) - Synchronize D to RAM and go into the wait-state like before.
    \begin{labeledenum}{Cycle}
    \item EN\_A, EN\_V, LD\_FA, EN\_D, WE\_RAM
    \item LD\_FB, CR
    \end{labeledenum}

  \item (A = 1, V = 0) - Synchronize RAM to D and go into the wait-state like before.
    \begin{labeledenum}{Cycle}
    \item EN\_A, EN\_V, LD\_FA, LD\_D, OE\_RAM
    \item LD\_FB, CR
    \end{labeledenum}

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

  \item (A = 1, V = 1, K = 1) - K has gone high; break out of the wait-state by clearing A and V (loading FA without asserting any signals) and move to the next instruction.
    \begin{labeledenum}{Cycle}[0]
    \item LD\_FA, CLR\_K, INC, RS2
    \item LD\_FB, LD\_I, CR
    \end{labeledenum}
\end{labeledenum}

\section{Input: \texttt{,}} \label{sec:sequences:input}
\paragraph{Handshake} Similar to the output command, the input command implements a handshake protocol to make sure that the databus is claimed by the input-device for the exact right amount of time, in order for the system to reliably read its contents. This happens using the same K-flag that was used in the output handshake.

\begin{labeledenum}{Step}
\item The CU then asserts the EN\_IN signal and will keep this control line asserted until K is set by the IO module, indicating that the data is ready.
\item The input module notices EN\_IN, waits until the keyboard buffer contains a value and puts this on the bus, then it sets K.
\item When K is seen to go high, the value on the bus is loaded into D and K is cleared to complete the handshake.
\end{labeledenum}

\paragraph{Implementation}
The microcode for the sequences described above is very similar to those of the OUT instruction. Again, the wait-state is encoded by setting A and V to 1, allowing the system to spin in cycle 0 while K is not yet set by the IO module. When K goes high, the data on the bus is latched into D, the A and K flags are cleared, V is set and the next instruction is reloaded. As was the case with the OUT instruction, we need an explicit LD\_FB before resetting the CC: to compensate for the fact that the flags have to be already up-to-date when cycle 0 loads in order to implement the busy-loop (all other commands refresh the flags in cycle 0). In this case, there is no need to synchronize D and RAM before setting the flags to the wait-state. Since we expect a new value to be read into D as a result of this instruction, the V-flag should be set and the A-flag should be reset regardless of the state of the computer on entering this instruction.

\begin{labeledenum}{Scenario}
  \item (A = 0, V = 0) - Go into wait-state.
    \begin{labeledenum}{Cycle}
    \item EN\_A, EN\_V, LD\_FA
    \end{labeledenum}

  \item (A = 0, V = 1) - Go into wait-state.
    \begin{labeledenum}{Cycle}
    \item EN\_A, EN\_V, LD\_FA
    \end{labeledenum}

  \item (A = 1, V = 0) - Go into wait-state.
    \begin{labeledenum}{Cycle}
    \item EN\_A, EN\_V, LD\_FA
    \end{labeledenum}

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

  \item (A = 1, V = 1, K = 1) - K has gone high; load the data, break out of the wait-loop by setting V and resetting A, clear K and move to the next instruction.
    \begin{labeledenum}{Cycle}[0]
    \item LD\_D
    \item EN\_V, LD\_FA, CLR\_K, INC, RS2
    \item LD\_FB, LD\_I, CR
    \end{labeledenum}
\end{labeledenum}

\paragraph{Input-Modes} The input peripheral (probably) manages an internal buffer to serve subsequent bytes from to the system, which might be empty when the request for input arrives. When this happens, it is up to the peripheral to decide upon one of 2 options:

\begin{enumerate}
\item Wait for the buffer to contain data. Only then set the K-flag (buffered mode).
\item Assert zero's to the bus and set the K-flag immediately (immediate mode).
\end{enumerate}
In our implementation of the IO-module (see \ref{sec:implementation:io}), both modes are supported and can be selected from the options menu.

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

\paragraph{INIT}
In any BF program it is assumed that all memory is zero-initialized. In practice, SRAM-modules will contain random values at startup, so the assembler must add a preamble to the main code in order to initialize the RAM (or at least part of it) to 0. While this could in principle be implemented in terms of canonical BF commands (initializing one cell at a time using a sequence of \texttt{[-]} commands) it is much faster to write a bunch of known zeroes directly to RAM. This is the purpose of the INIT instruction: for each INIT instruction, a contiguous chunk of 256 memory-cells will be zero-initialized. Since it is guaranteed that the D register contains a zero after reset, this value can be directly written into RAM on the first cycle of INIT while also incrementing the LS and DP registers. DP is incremented to move through the memory-space whereas LS is incremented in order to count to 256, at which point the S-flag will go low again due to the LS register overflowing back to 0. If more memory needs to be initialized, the assembler can simply concatenate multiple INIT instructions.

\begin{labeledenum}{Cycle}
\item EN\_D, WE\_RAM, INC, RS0, RS2 (write a zero to the current cell)
\item LD\_FBI, INC, RS1 (increment the LS-register)
\item Depending on whether the LS-register wrapped around (256 cells initialized), either move to the next cell or finalize by incrementing the IP and resetting the cycle-counter.

  \begin{labeledenum}{Scenario}
  \item (S = 0) - INC, RS2, CR
  \item (S = 1) - CR
  \end{labeledenum}

\end{labeledenum}
After the appropriate number of INIT instructions have been execured, the INIT\_FINISH instruction (see below) must be called in order for the DP to return back to the start of the memory (0x0100).

\paragraph{INIT\_FINISH}
The INIT\_FINISH opcode is designed to do two things: it resets the DP to the start of the data section (0x0100) and it resets the K-flag. The former is necessary after initialization, which leaves the DP at whatever the last cell was that was initialized, and is achieved by asserting the CLR\_DP signal. The latter will tell the IO module that initialization is finished (the IO module sets the K-flag at boot). The IO module will respond to this by taking ownership of the bus and writing the program slot to it. The LOAD\_SLOT instruction (which is always immediately following the INIT\_FINISH instuction) will use this value to skip to the desired program.

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

\paragraph{PROG\_START}
The only opcode that performs non-trivial actions while the system is in skip-mode (initiated by incrementing LS as described above) is PROG\_START. It checks the value in D, which was initially populated with the index of the desired program (0, 1, 2, ...), to see if the IP has arrived at the correct location: if the Z-flag is set (D = 0), we exit skip-mode and enter the program following the current PROG\_START instruction. If the Z-flag is not set (D $\ge$ 0), we decrement D and keep scanning. In other words, D is decremented on each PROG\_START until it hits zero, i.e.~the selected program slot has been reached.

\begin{labeledenum}{Scenario}
  \item (S = 1, Z = 0) - D still holds a nonzero value. Decrement D and continue in skip-mode:
  \begin{labeledenum}{Cycle}
  \item DEC, RS0
  \item INC, RS2
  \end{labeledenum}

  \item (S = 1, Z = 1) - D is zero. Exit skip-mode (decrement LS) to run subsequent code.
  \begin{labeledenum}{Cycle}
  \item DEC, RS0, RS2
  \item INC, RS2
  \end{labeledenum}
\end{labeledenum}

Note that, while skipping over entire programs, the LOOP\_START and LOOP\_END instructions will still have the effect of incrementing and decrementing LS. However, since LS starts out at 1 and programs are guaranteed to contain matching brackets (enforced by the assembler), it is guaranteed to contain the value 1 when the entire program is skipped over (it will have undergone an equal amount of increment and decrement operations). Decrementing it a final time (Cycle 1 of Scenario 2) is therefore guaranteed to bring it back to 0, disabling the S-flag.

\section{Convenience Opcodes} \label{seq:sequences:convenience}
While all of the opcodes above would be sufficient to run any BF program, it is still convenient to be able to halt the clock, indicate that an error occurred or tell the user that the end of the program was reached succesfully. Furthermore, the common extension \emph{Random Brainfuck} \cite{esolangs-rbf} is implemented as an additional instruction (RAND) that acts just like the IN instruction, except now a random number appears on the bus rather than user input (handled by the IO module as well). All non-BF opcodes are listed and described below.

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

\begin{labeledenum}{Cycle}
\item INC, RS2, CR
\end{labeledenum}

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

\begin{labeledenum}{Cycle}
\item HLT
\item INC, RS2, CR
\end{labeledenum}

\paragraph{PROG\_END}
The PROG\_END instruction is basically a HALT instruction that also lights up an LED by asserting the END signal. This let's the user know that the end of the program was reached gracefully. Contrary to the HALT instruction, no Cycle 2 has been defined. Trying to resume the clock after a PROG\_END was reached will therefore result in the ERR signal being raised (see below).

\begin{labeledenum}{Cycle}
\item HLT, END
\end{labeledenum}

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
