jorenheit/bfcpu/website/content/tex/introduction.tex

\chapter{Introduction} \label{sec:introduction}
The Brainfuck (BF) programming language is an esoteric programming language that is essentially impossible - or at least highly impractical - to actually write useful programs in. Even if you became a very skilled programmer in this language, the resulting programs would be incredibly slow to execute. Despite this, many programmers have challenged themselves to write stunning pieces of code just for fun, or for the learning experience it offers. In doing so, it teaches us about computer architecture, compilers/interpreters, memory, pointers and much more. For more information on the language itself, see Section \ref{sec:brainfck}.

\paragraph{Goals} The main goal of this project was to build a computer that can actually run BF code natively. Normally, after having written some new piece of BF, the programmer presents this code to some program that either compiles it to an executable native to the host architecture, or interprets it in a virtual BF machine. However, instead of treating BF as a language that requires compilation or interpretation, why not view it as the instruction set of a, yet to exist, BF-CPU?

Our goal was to build this BF-CPU without making use of any programmable chips, relying solely on Transistor-Transistor-Logic (TTL) chips such as registers, buffers and (de)multiplexers in addition to the necessary RAM and ROM. The computer was to be implemented entirely on breadboards, as it was inspired by Ben Eater's 8-bit breadboard computer \cite{beneater}. It should be able to run any compliant BF program directly, as long as it fits in the program ROM and does not exhaust the available amount of memory or stack-space. In other words: the computer should be capable of running canonical BF without doing any preprocessing steps like pre-calculating jump-addresses.

\paragraph{Outcome}
Over roughly 2.5 years (intermittently), the design evolved into a stable microcoded CPU with a Harvard-like memory map, a two-phase clock that can drive the system at over 200kHz, and a supporting software toolchain (assembler, EEPROM programmer, microcode compiler and emulation library) that makes prototyping, editing, assembling, and flashing programs and microcode practical. It has a sophisticated IO module that handles both input (both random numbers and keyboard input) and output (to a 4x20 character LCD display). This IO module is driven by an Atmega328P to be able to manage IO buffers, implement the PS2 protocol and drive the screen, in addition to managing all the IO settings (echo, autoscroll, output modes, etc) and to provide a user interface for selecting the active program at runtime. A deliberate choice was made to use a programmable chip in this case, since it is not really part of the CPU itself and makes the IO capabilities a lot more advanced and convenient. To the CPU core, the outside world is a black box that accepts certain control signals and acts accordingly; similar to the fact that the BF input and output commands (\texttt{.} and \texttt{,}) are interacting with an abstract external world.

The machine has been tested by running many different BF programs on it that can be found online, validating its stability and BF-standard conformity (if such a thing even exists). The source code for all supporting software is available on Github at \url{https://github.com/jorenheit/bfcpu}.

\newpage
\paragraph{Document structure}
\begin{itemize} \setlength\itemsep{0em}
  \item Section~\ref{sec:brainfck} recaps the BF programming language: how does this language work, what does a simple interpreter look like and how does it relate to the architecture of Synapse-191?
  \item Section~\ref{sec:architecture} describes the architecture from a modular perspective: what is the purpose of each of the high-level modules, what control signals do they accept and what actions do they perform when clocked?
  \item Section~\ref{sec:sequences} explains microcode and control sequences; how do all these signals and modules work together to perform the computations necessary to run BF programs?
  \item Section~\ref{sec:implementation} discusses hardware implementation: what kinds of chips and techniques were used to implement the modules on a hardware level?
  \item Section~\ref{sec:utilities} covers supporting utilities, like the assembler, microcode compiler, EEPROM programming utilities, etc. 
  \item Section~\ref{sec:results} goes through a number of test programs that were used during development.
    \item Section~\ref{sec:finalthoughts} lists a number of possible improvements that could still be implemented in the future, as well as some more general final thoughts.
  \item We conclude in Section~\ref{sec:conclusion} with a brief retrospective on the project.
\end{itemize}

\vfill
\begin{center}
  
\end{center}

\section{Brainfuck}\label{sec:brainfck}
\subsection{Language Description}
Brainfuck is a popular esoteric programming language. Just like any other programming language, it allows the programmer to write programs consisting of commands that are executed in order. The key limitation is that the language provides only eight commands to the programmer, all written as a single character: ``\texttt{+-<>[].,}''. Each of these commands corresponds to an operation on an array of memory or a pointer, pointing to some location within this memory. At the start of the program, every cell in (an infinite amount of) memory is initialized to 0 and the pointer is pointing to the very first element (index 0, see Figure \ref{fig:bfmachine_initial}).
%
\begin{figure}[H]
  \centering
  
  \caption{Initial state of the BF machine.}
  \label{fig:bfmachine_initial}
\end{figure}
%
The commands then modify the contents of memory or the pointer as follows:
\begin{itemize}
\item \texttt{+} : add 1 to the current cell;
\item \texttt{-} : subtract 1 from the current cell;
\item \texttt{<} : move the pointer 1 cell to its left;
\item \texttt{>} : move the pointer 1 cell to its right;
\item \texttt{[} : if the current cell is nonzero, continue to the next instruction. Otherwise, skip all instructions and continue beyond the matching closing \texttt{]};
\item \texttt{]} : if the current cell is zero, exit the loop and continue to the next instruction. Otherwise, loop back to its matching opening \texttt{[};
\item \texttt{.} : send the value in the current cell to the output device;
\item \texttt{,} : read a value from the input device and store it into the current cell.
\end{itemize}
Although the instruction set is minimal, it has been proven to be sufficient for performing any possible computation or program, also known as Turing-completeness \cite{esolangs-bf}. The catch is that this requires an unbounded (or infinite) amount of memory, which is obviously impossible. However, the same caveat holds for traditional systems, so we should be safe to assume that BF is Turing complete for all practical purposes.

\subsection{Interpreters}
To run a BF program, one usually feeds these commands into an interpreter written in a more common language. These interpreters are very straightforward to write. Listing \ref{lst:bfint} shows a very basic implementation (about 40 lines) a BF-interpreter written in C. This implementation initializes a block of memory to zero and defines a pointer to its first element. This pointer can be incremented or decremented to move along the array, increment/decrement the value it's pointing to or print it to the standard output. Most of its complexity is embedded in the handling of the loop-operators. When an opening bracket is encountered, the index of this instruction is stored in a jump-table. When control reaches its matching closing bracket and the value of the cell pointed to is nonzero, this stored index is reloaded in order to return to the start of the loop. When skipping a loop, i.e.~the current cell holds a zero when the opening bracket is evaluated, all commands up to and including the matching closing bracket are skipped.

\begin{lstfloat}[H]
  \lstinputlisting[linerange={bfint\_begin-bfint\_end}, language=C]{../src/simple_int/bfint.c}  
\caption{Very basic implementation of a BF interpreter in C.}
\label{lst:bfint}
\end{lstfloat}

When the Hello World program from Wikipedia \cite{bfwiki} is fed into the function of Listing \ref{lst:bfint}, it prints out the string \texttt{Hello World!}, as expected.
\vspace{0.5cm}
\begin{lstlisting}[language=bash]
  $ ./bfint "++++++++[>++++[>++>+++>+++>+<<<<-]>+>+>->>+[<]<-]>>.> \
             ---.+++++++..+++.>>.<-.<.+++.------.--------.>>+.>++."
  Hello World!
\end{lstlisting}

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

\paragraph{Harvard Architecture} Modern computers are built according to the von Neumann architecture \cite{vonneumann-wiki}, which specifies a CPU (containing registers and an ALU), a single unit of memory and input/output devices. In this architecture, both the program's instructions and data are stored in RAM. This allows for programs to change their own code at runtime (self-modifying code) because the program itself is data in a sense. This model does \emph{not} naturally fit the Brainfuck model, which has a strict seperation between instructions and data; the data pointer can never point to the instructions that govern it. This is why a Harvard architecture was adopted. In the Harvard architecture two kinds of memory exist: program memory containing the instructions - stored in read-only memory (ROM) - and data memory - stored in random-access-memory (RAM) - containing the modifyable data (Figure \ref{fig:harvard}).

\begin{figure}[H]
  \centering
  
  \caption{Schematic overview of the Harvard architecture.}
  \label{fig:harvard}
\end{figure}
