jorenheit/bfcpu/doc/img/_processor.jpeg

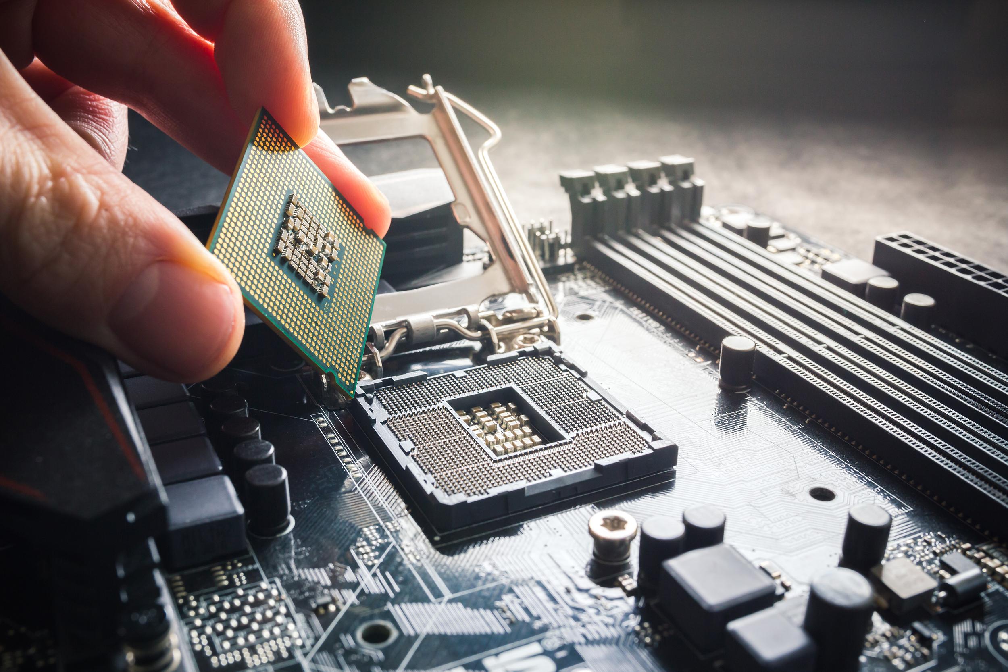
doc/img/_processor.jpeg
