jorenheit/bfcpu/doc/img/actual_driver_module_implementation.png

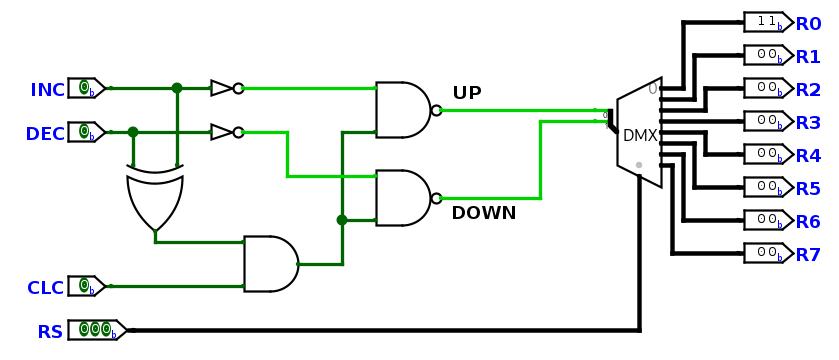
doc/img/actual_driver_module_implementation.png
