jorenheit/bfcpu/doc/img/astable.jpg

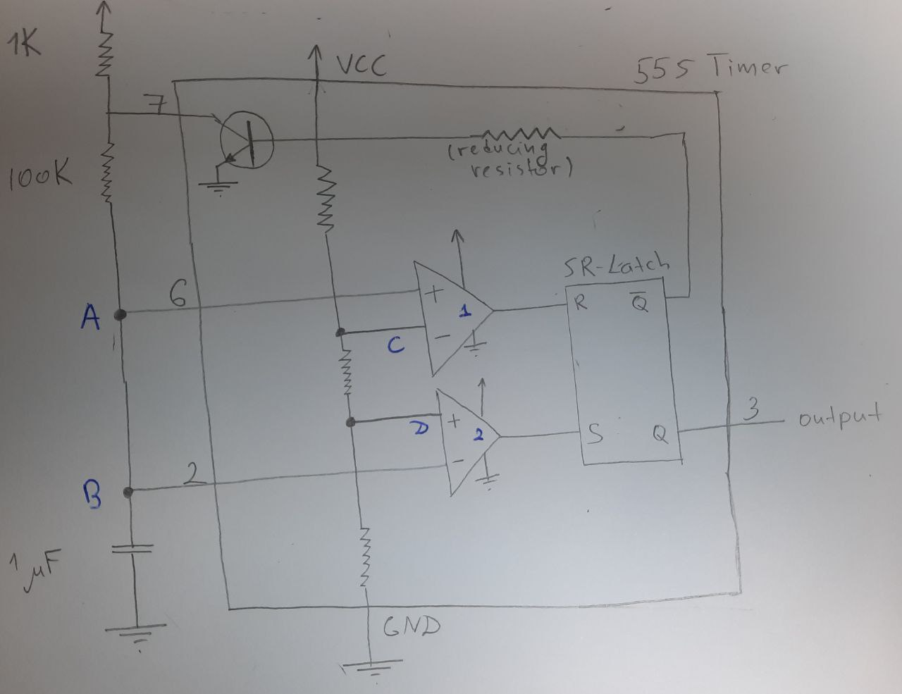
doc/img/astable.jpg
