jorenheit/bfcpu/doc/img/bank_loading_timing.png

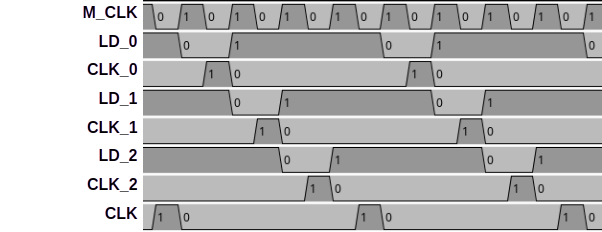
doc/img/bank_loading_timing.png
