jorenheit/bfcpu/doc/img/bank_separation_example.png

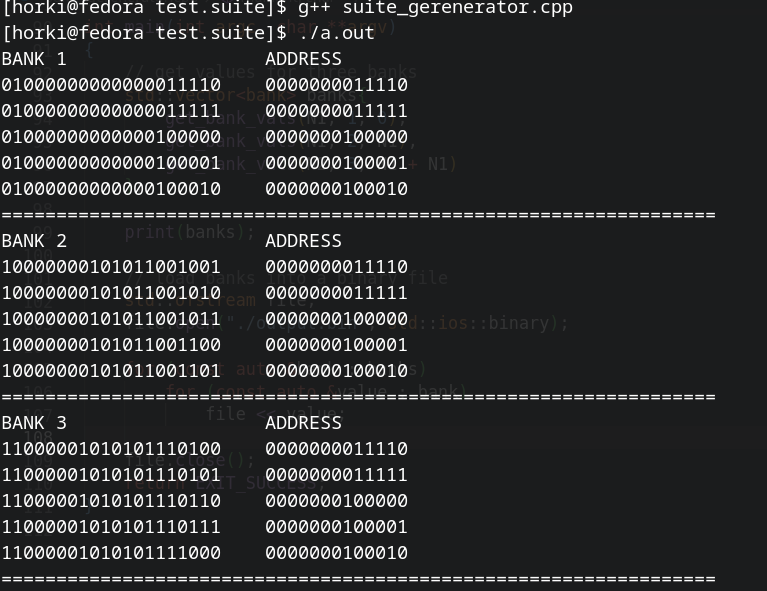
doc/img/bank_separation_example.png
