jorenheit/bfcpu/doc/img/clock_scope.jpg

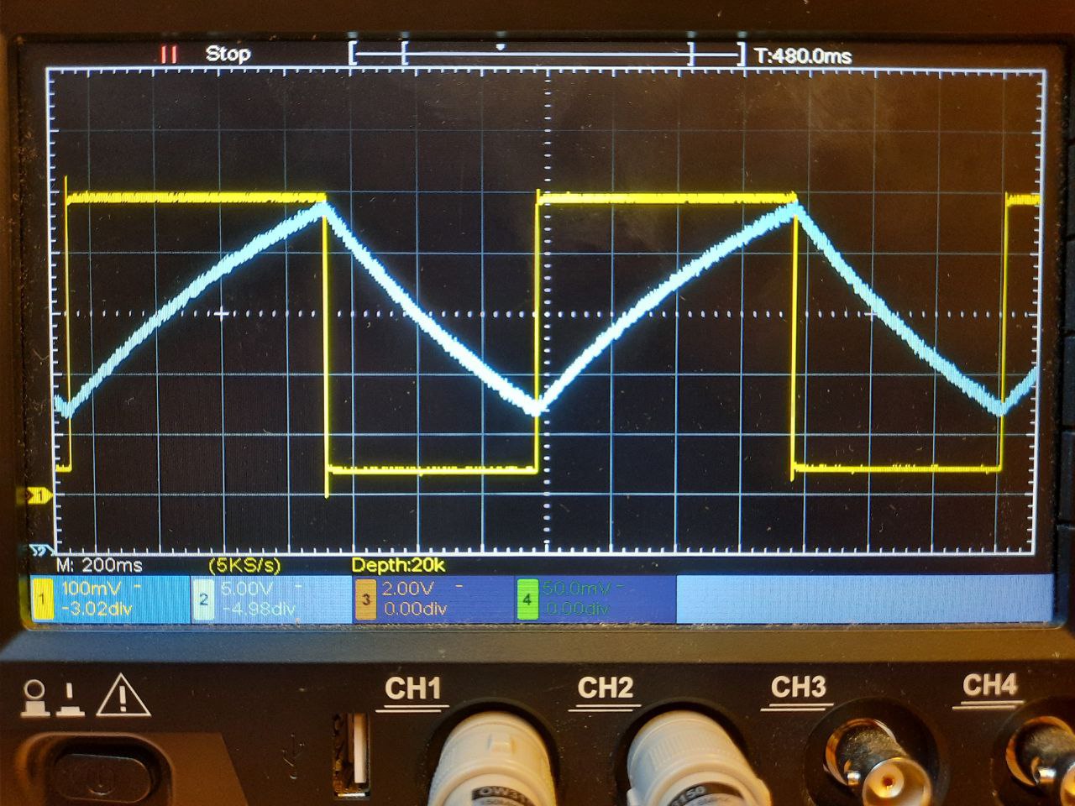
doc/img/clock_scope.jpg
