jorenheit/bfcpu/doc/img/computer.png

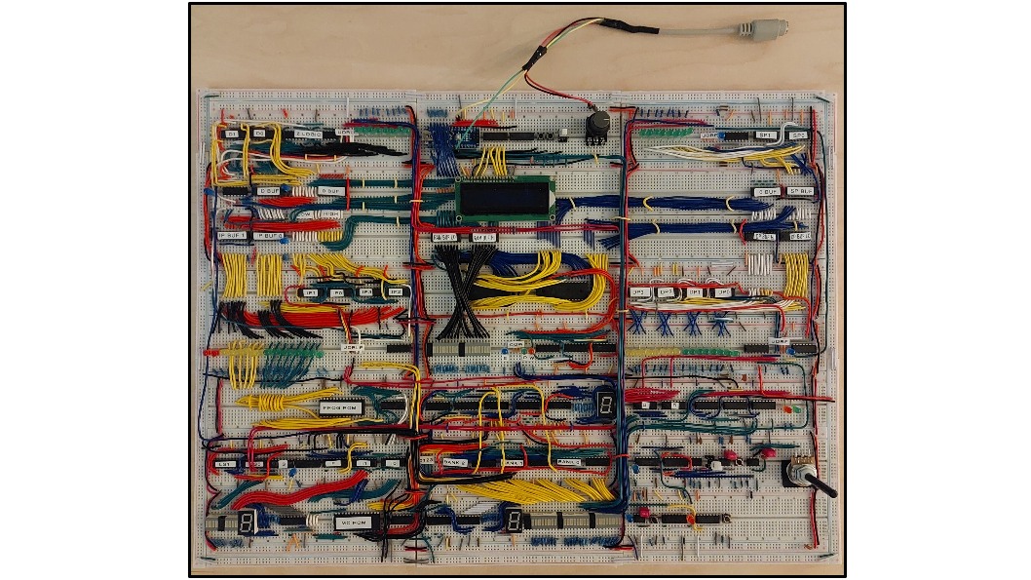
doc/img/computer.png
