jorenheit/bfcpu/doc/img/counter_circuit_logisim.png

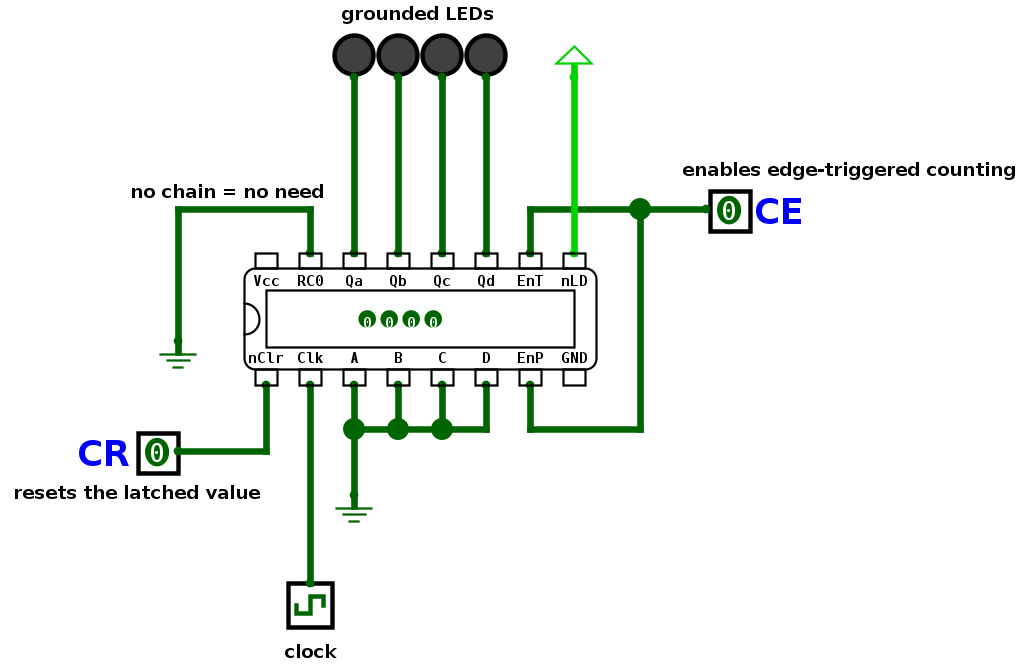
doc/img/counter_circuit_logisim.png
