jorenheit/bfcpu/doc/img/counters.jpg

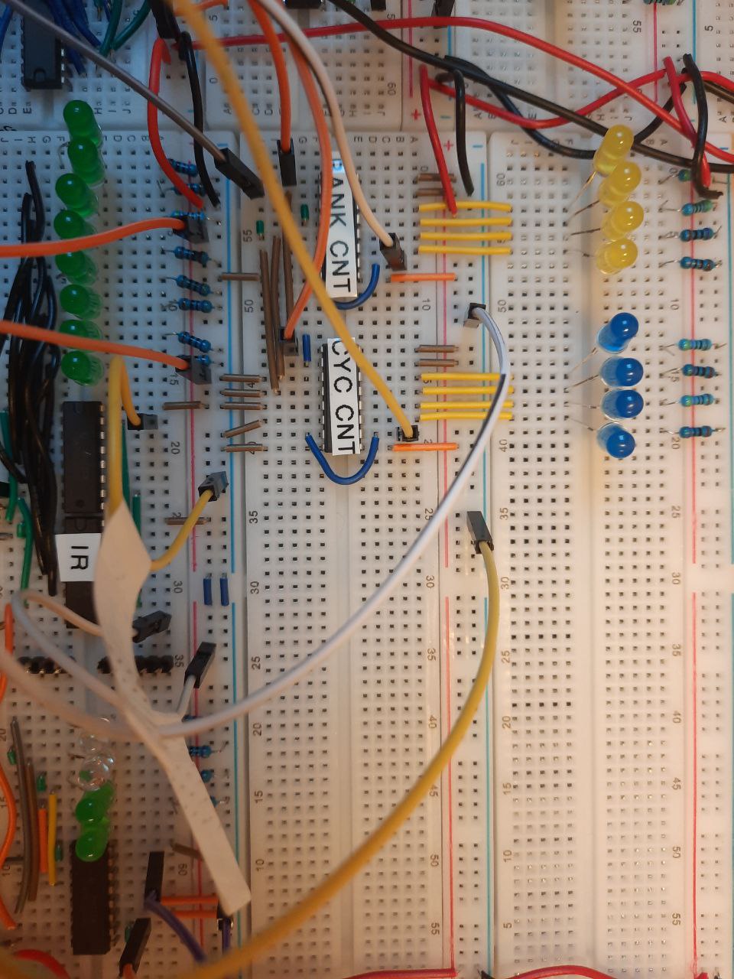
doc/img/counters.jpg
