jorenheit/bfcpu/doc/img/CU.png

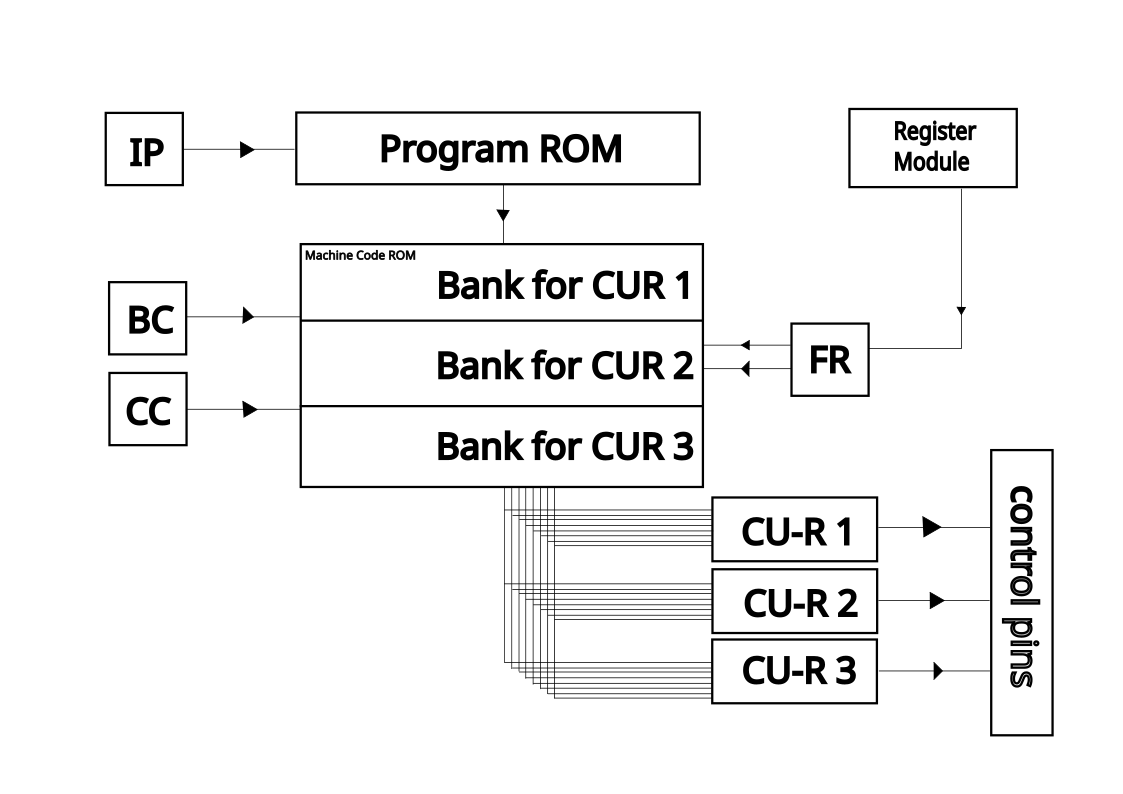
doc/img/CU.png
