jorenheit/bfcpu/doc/img/CU_clock.png

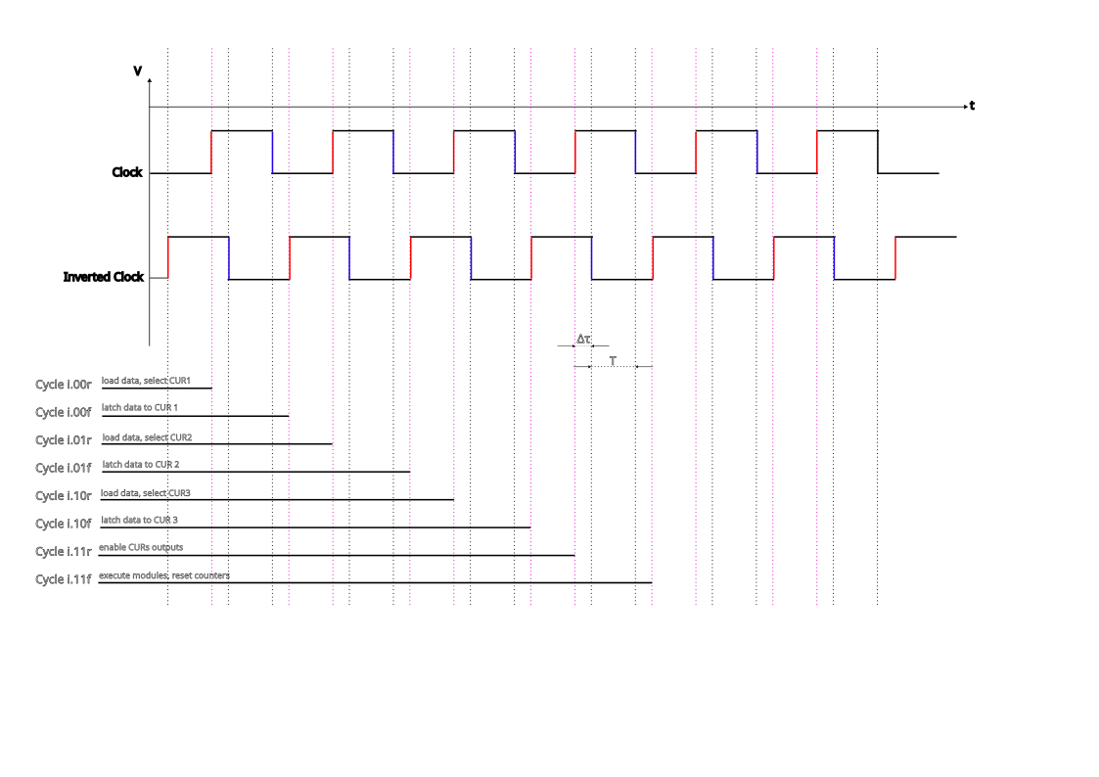
doc/img/CU_clock.png
