jorenheit/bfcpu/doc/img/curs.jpg

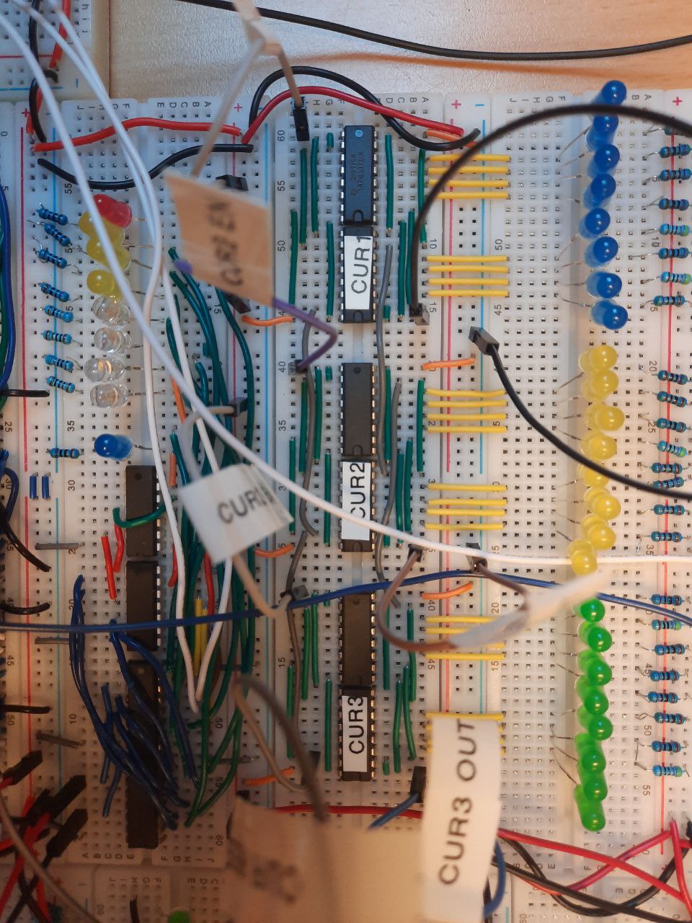
doc/img/curs.jpg
