jorenheit/bfcpu/doc/img/data_pointer_register_implementation.png

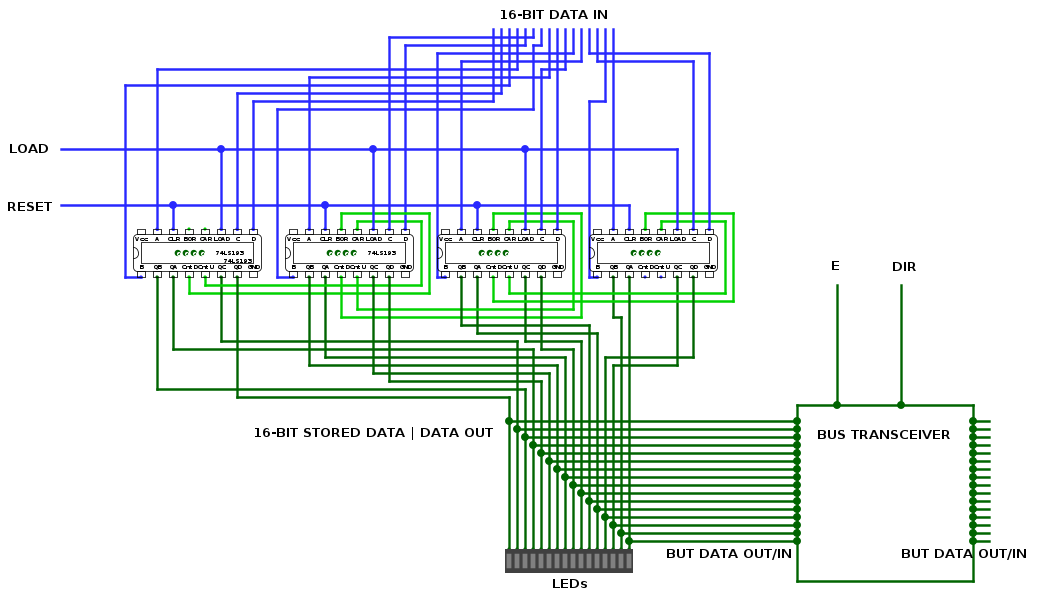
doc/img/data_pointer_register_implementation.png
