jorenheit/bfcpu/doc/img/data_register_implementation.png

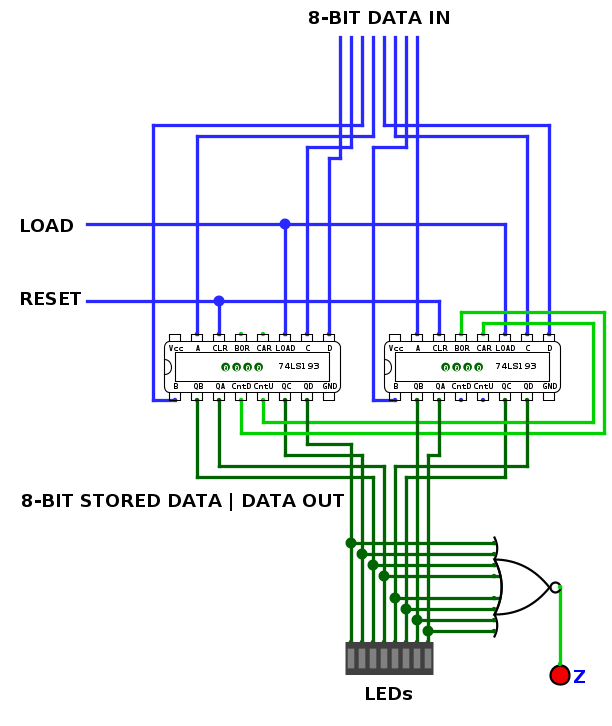
doc/img/data_register_implementation.png
