jorenheit/bfcpu/doc/img/dpregcloseup.png

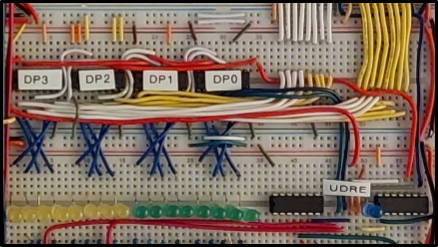
doc/img/dpregcloseup.png
