jorenheit/bfcpu/doc/img/elong_wires_ram.png

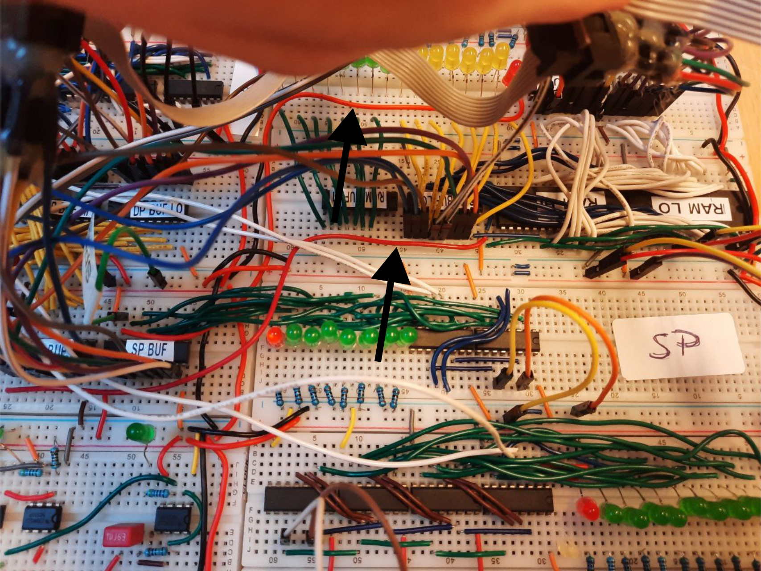
doc/img/elong_wires_ram.png
