jorenheit/bfcpu/doc/img/euler.jpeg

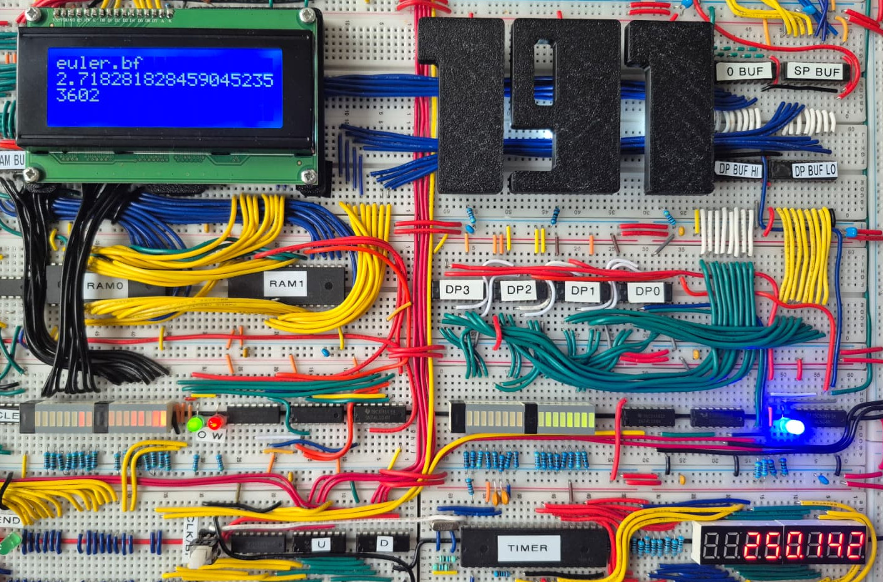
doc/img/euler.jpeg
