jorenheit/bfcpu/doc/img/eulerstats.png

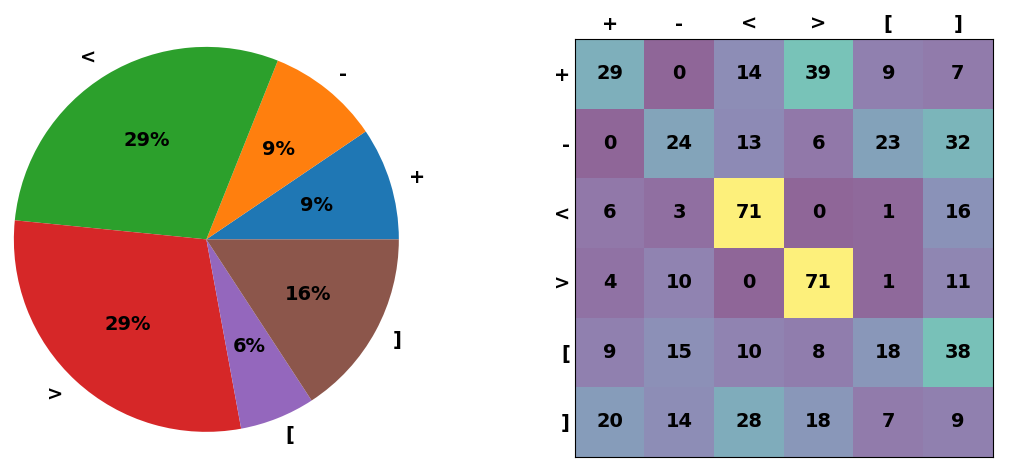
doc/img/eulerstats.png
