jorenheit/bfcpu/doc/img/factorialstats.png

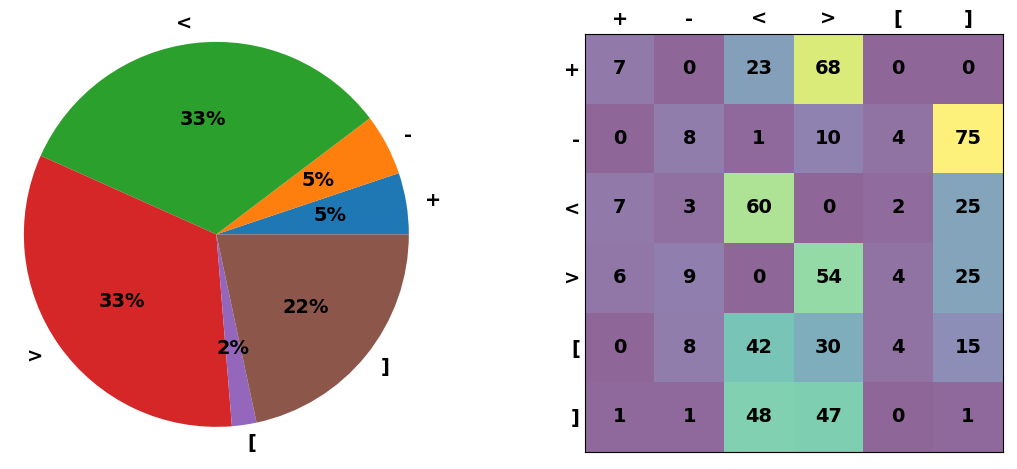
doc/img/factorialstats.png
