jorenheit/bfcpu/doc/img/hellostats.png

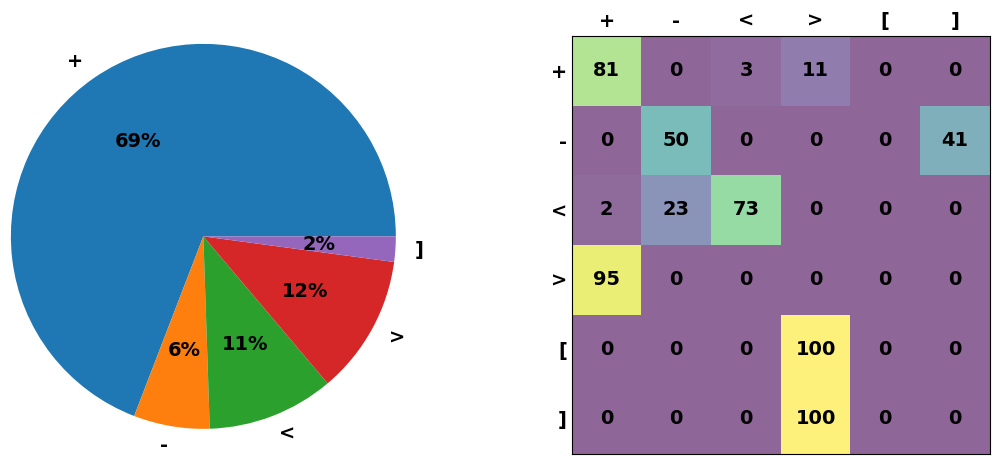
doc/img/hellostats.png
