jorenheit/bfcpu/doc/img/inputbufalg.png

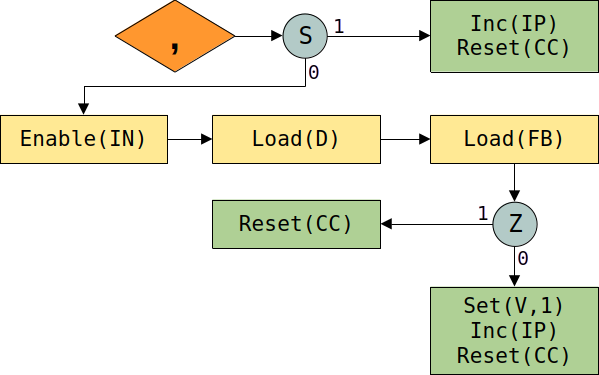
doc/img/inputbufalg.png
