jorenheit/bfcpu/doc/img/inputimalg.png

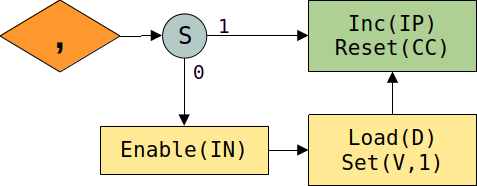
doc/img/inputimalg.png
