jorenheit/bfcpu/doc/img/loop.png

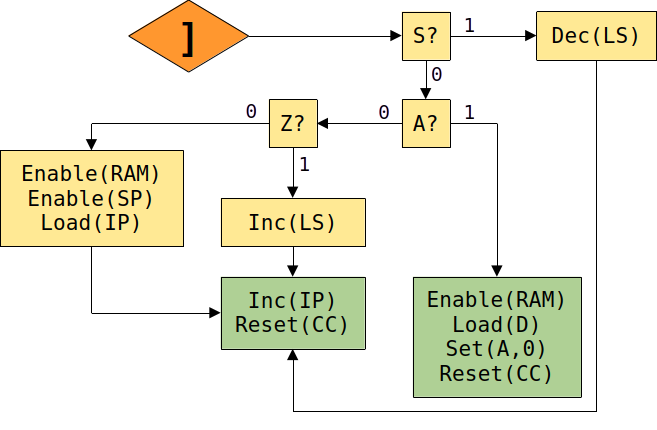
doc/img/loop.png
