jorenheit/bfcpu/doc/img/masterclockcloseup.png

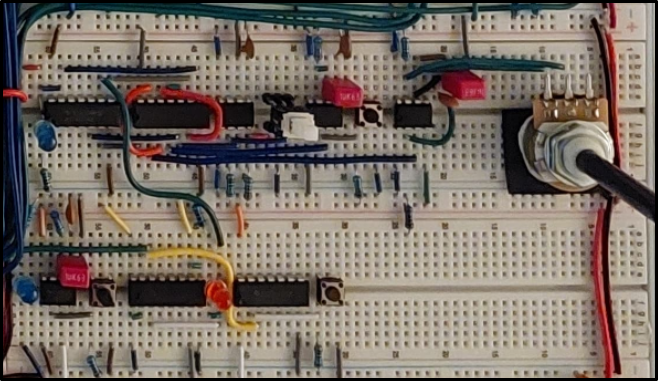
doc/img/masterclockcloseup.png
