jorenheit/bfcpu/doc/img/monostable.jpg

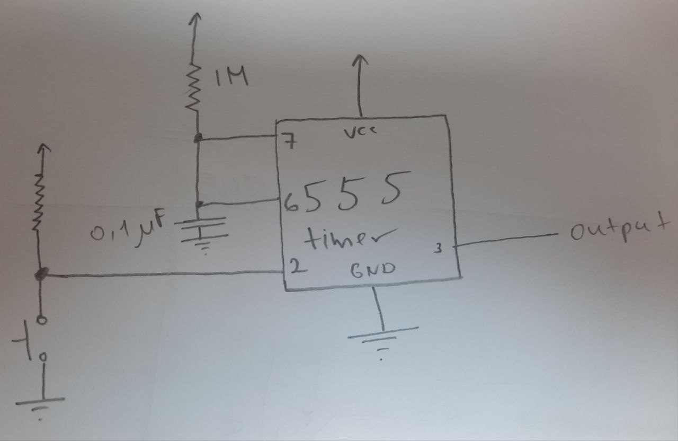
doc/img/monostable.jpg
