jorenheit/bfcpu/doc/img/phi.jpeg

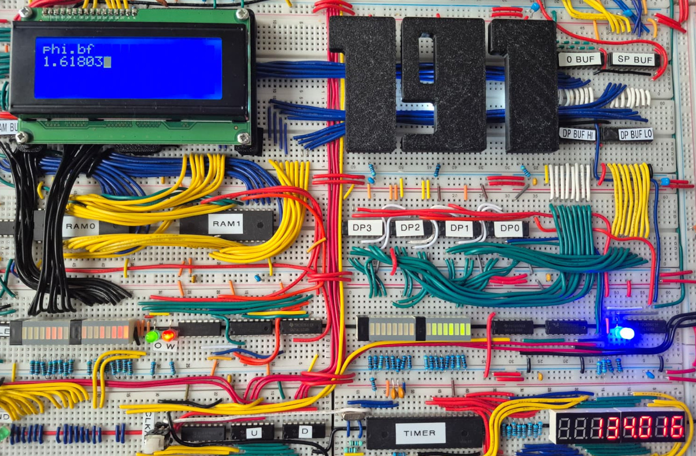
doc/img/phi.jpeg
