jorenheit/bfcpu/doc/img/phistats.png

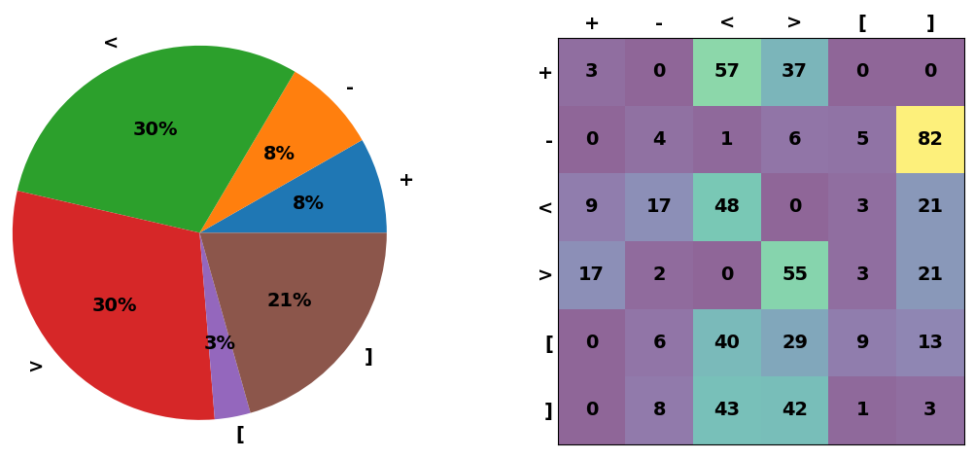
doc/img/phistats.png
