jorenheit/bfcpu/doc/img/pics/1.jpg

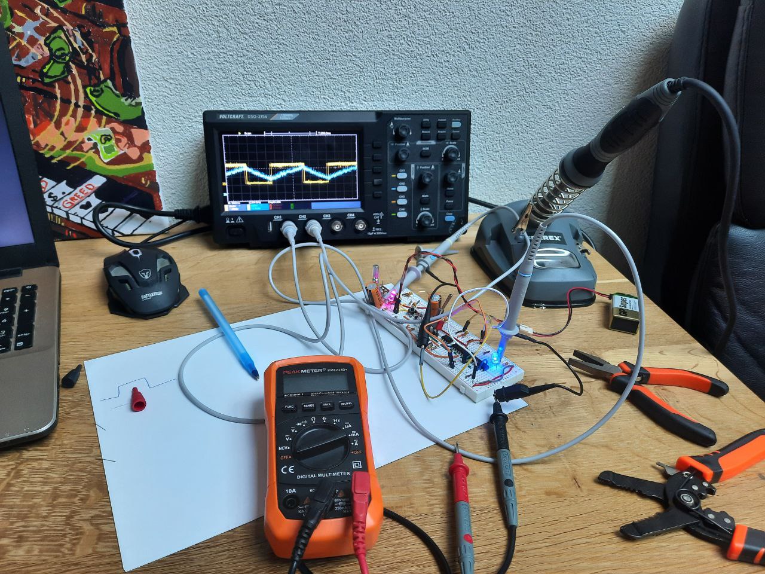
doc/img/pics/1.jpg
