jorenheit/bfcpu/doc/img/pics/2.jpg

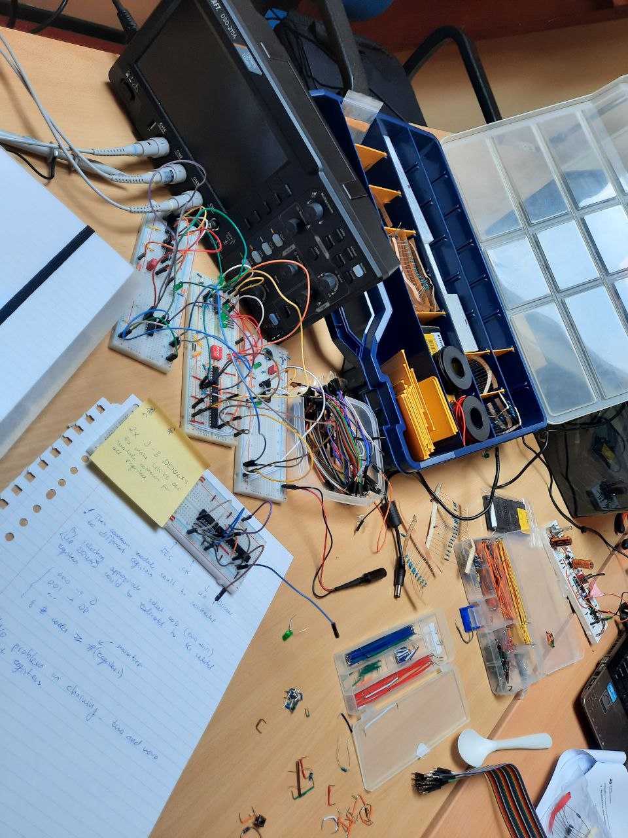
doc/img/pics/2.jpg
