jorenheit/bfcpu/doc/img/pics/3.jpg

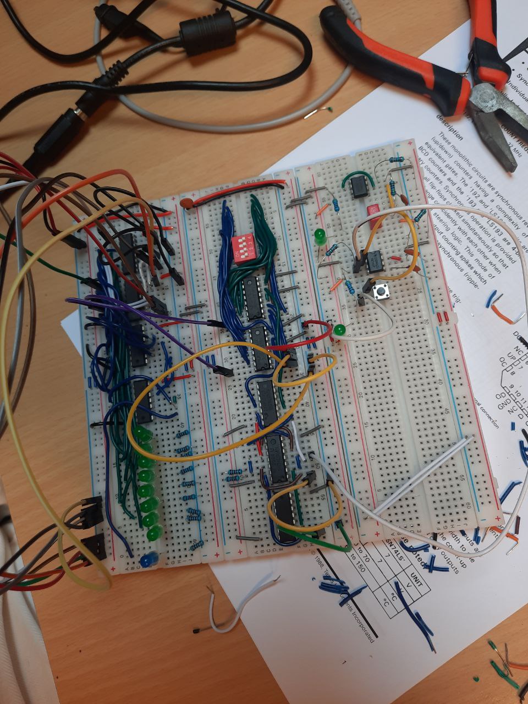
doc/img/pics/3.jpg
