jorenheit/bfcpu/doc/img/pics/4.jpg

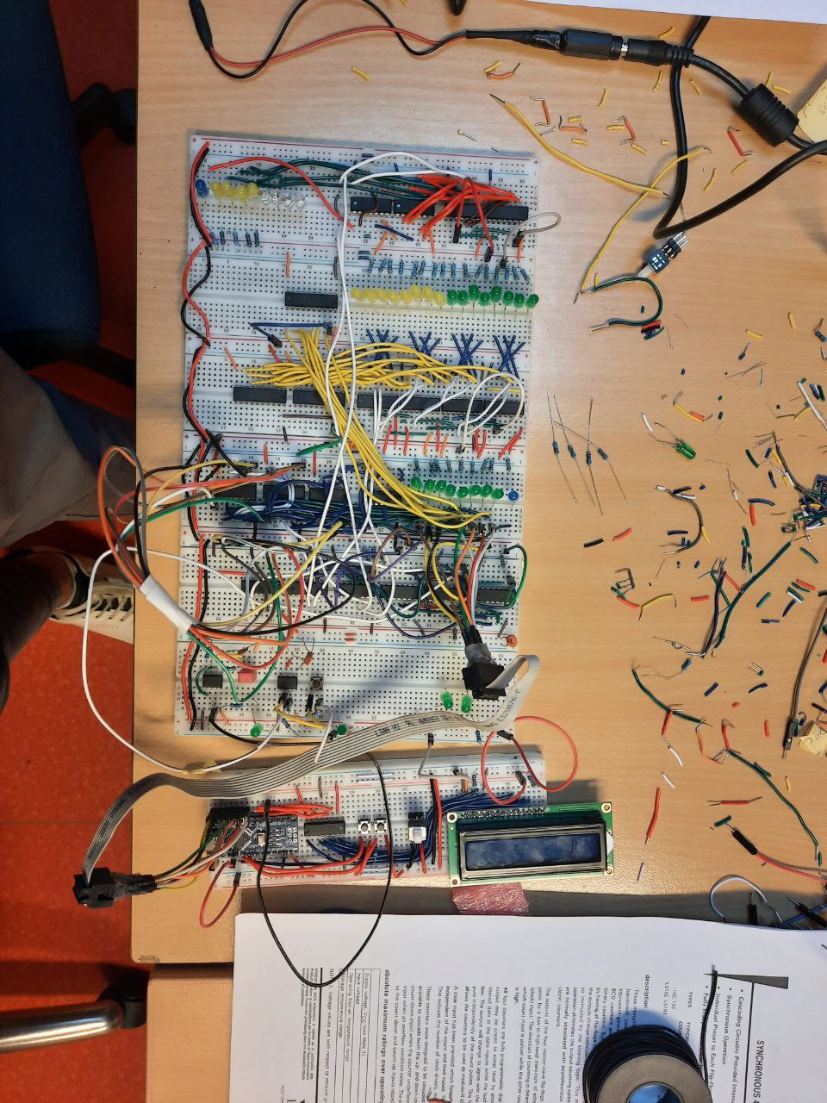
doc/img/pics/4.jpg
