jorenheit/bfcpu/doc/img/pics/5.jpg

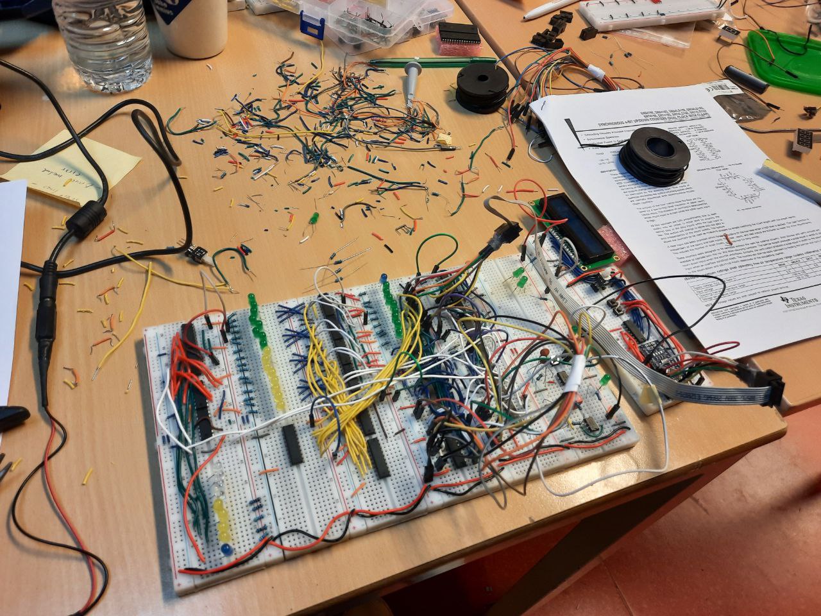
doc/img/pics/5.jpg
