jorenheit/bfcpu/doc/img/pics/6.jpg

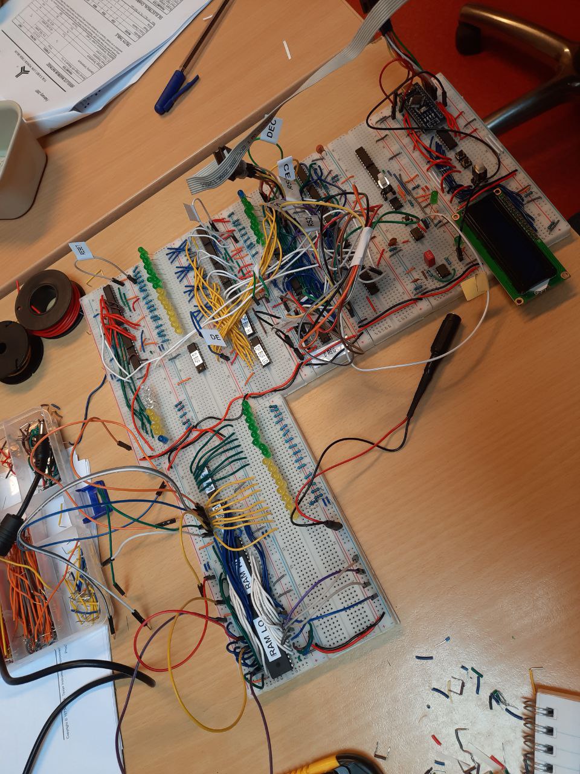
doc/img/pics/6.jpg
