jorenheit/bfcpu/doc/img/pics/7.jpg

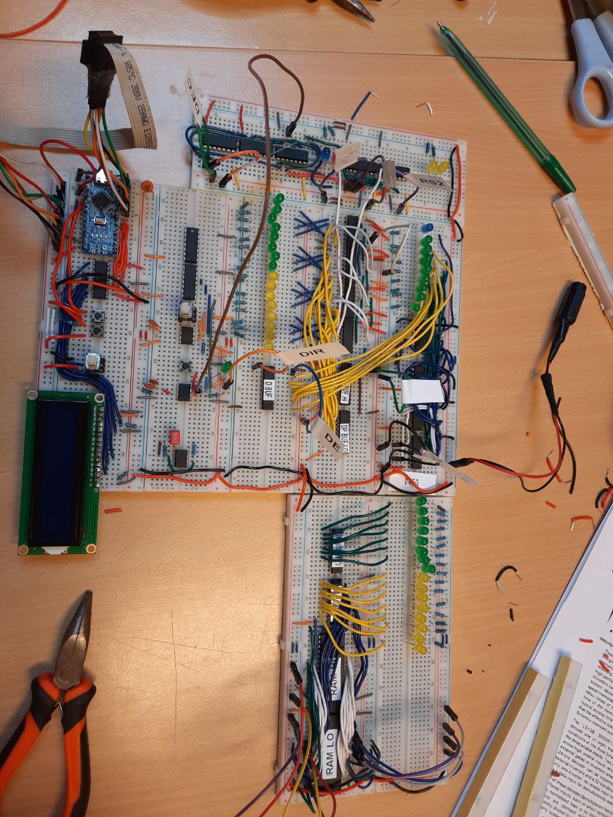
doc/img/pics/7.jpg
