jorenheit/bfcpu/doc/img/pics/8.jpg

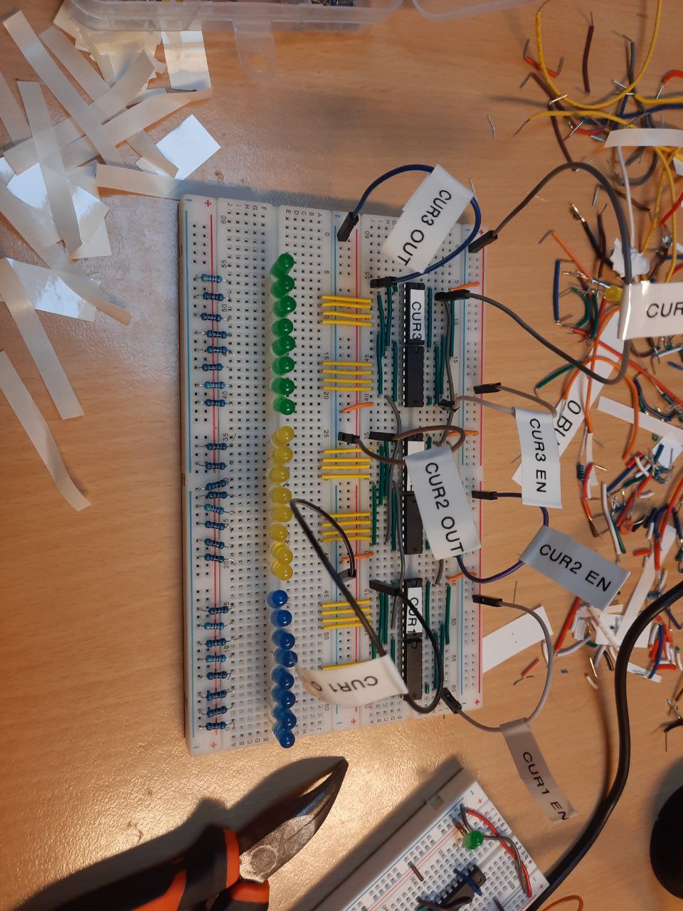
doc/img/pics/8.jpg
