jorenheit/bfcpu/doc/img/pics/1000041101.jpg

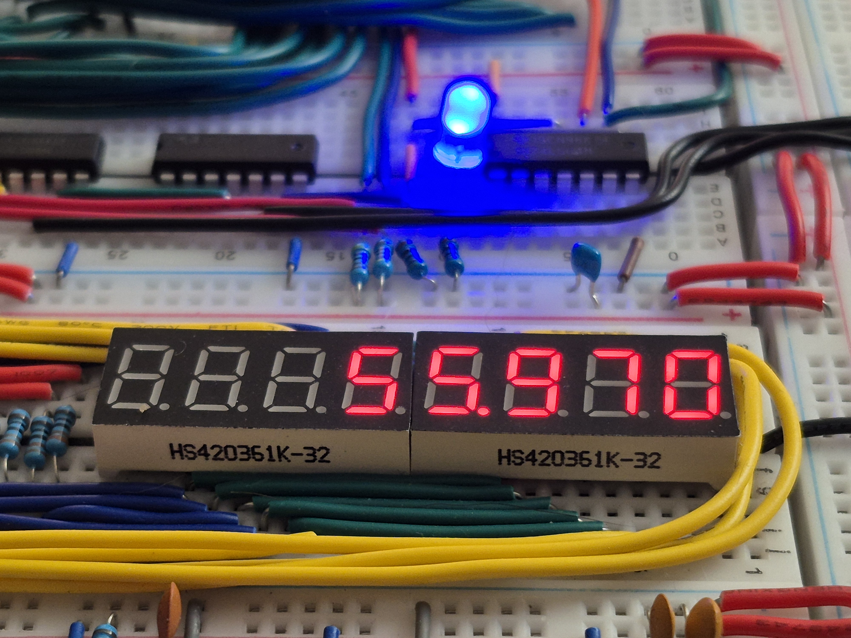
doc/img/pics/1000041101.jpg
