jorenheit/bfcpu/doc/img/pics/1000041103.jpg

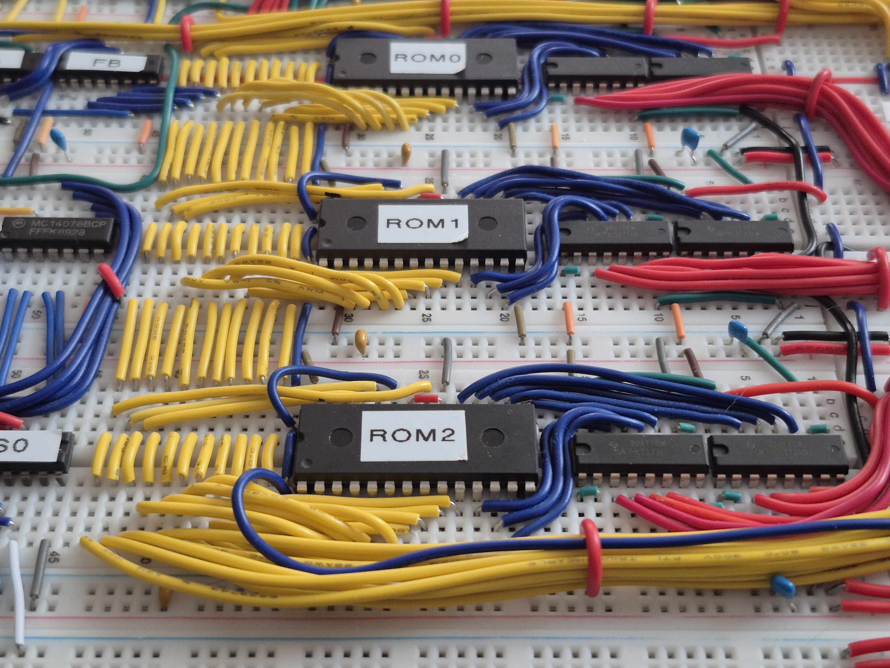
doc/img/pics/1000041103.jpg
