jorenheit/bfcpu/doc/img/pics/1000041105.jpg

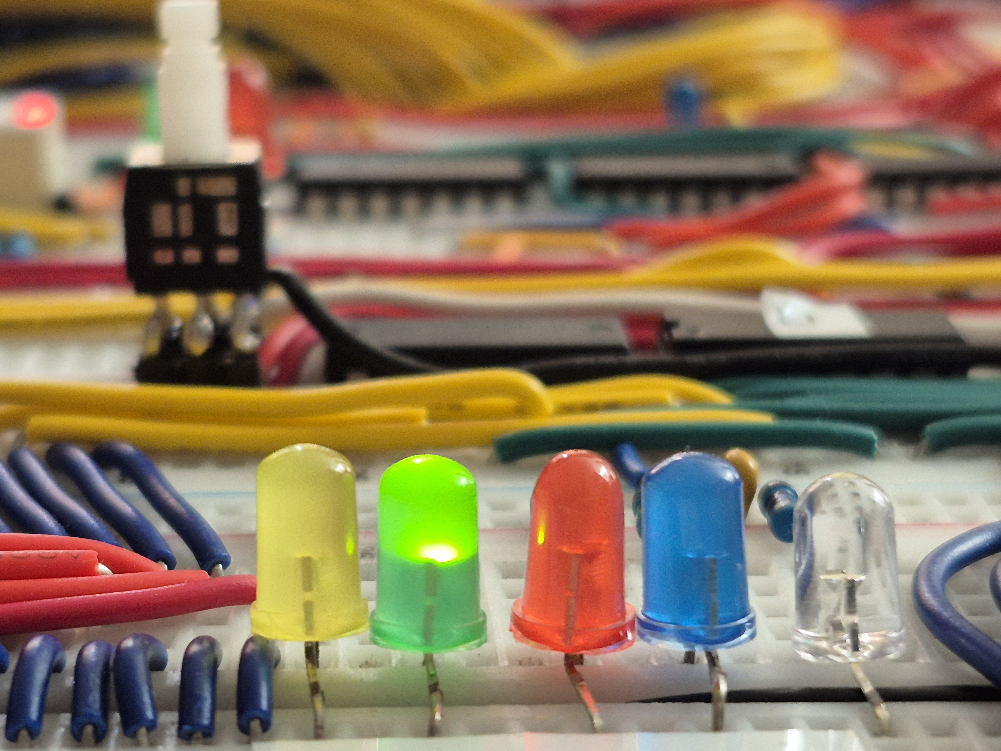
doc/img/pics/1000041105.jpg
