jorenheit/bfcpu/doc/img/pics/1000041107.jpg

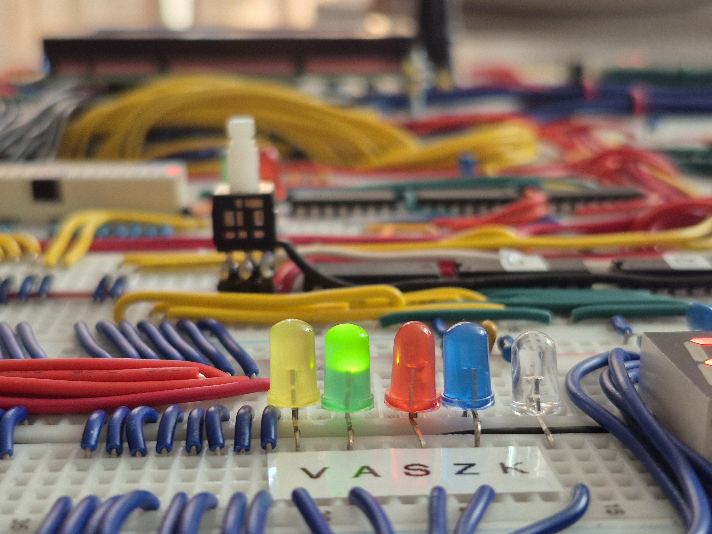
doc/img/pics/1000041107.jpg
