jorenheit/bfcpu/doc/img/pics/1000041108.jpg

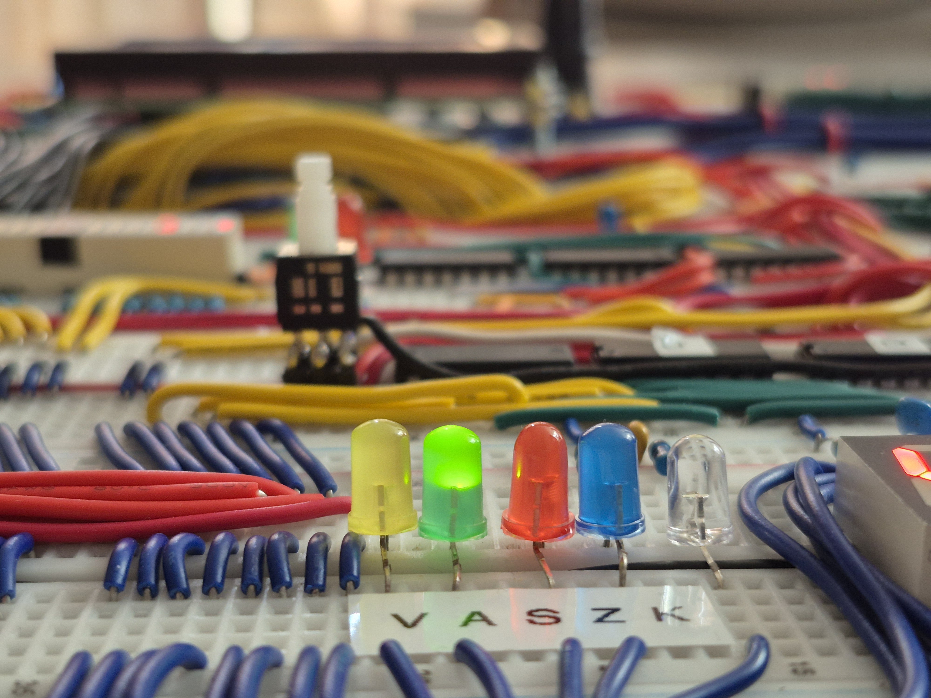
doc/img/pics/1000041108.jpg
