jorenheit/bfcpu/doc/img/pics/1000041109.jpg

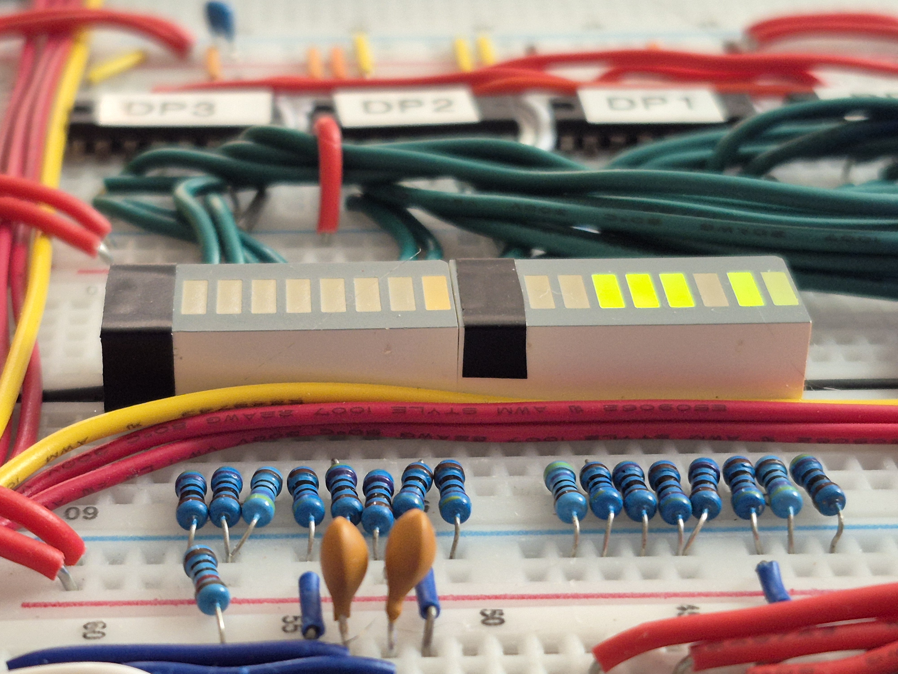
doc/img/pics/1000041109.jpg
