jorenheit/bfcpu/doc/img/pics/1000041110.jpg

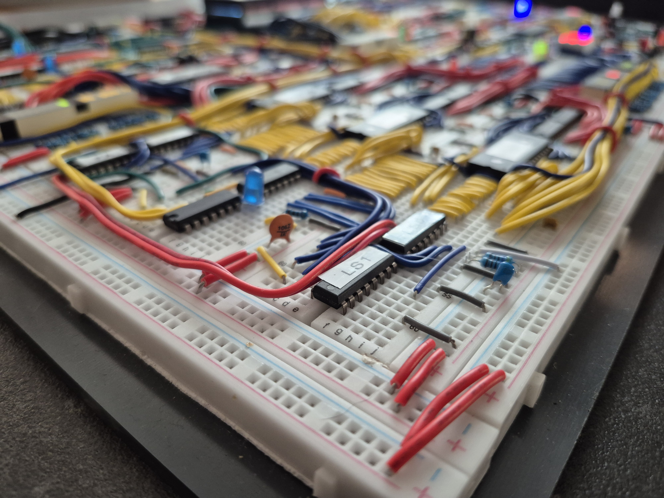
doc/img/pics/1000041110.jpg
