jorenheit/bfcpu/doc/img/pics/1000041111.jpg

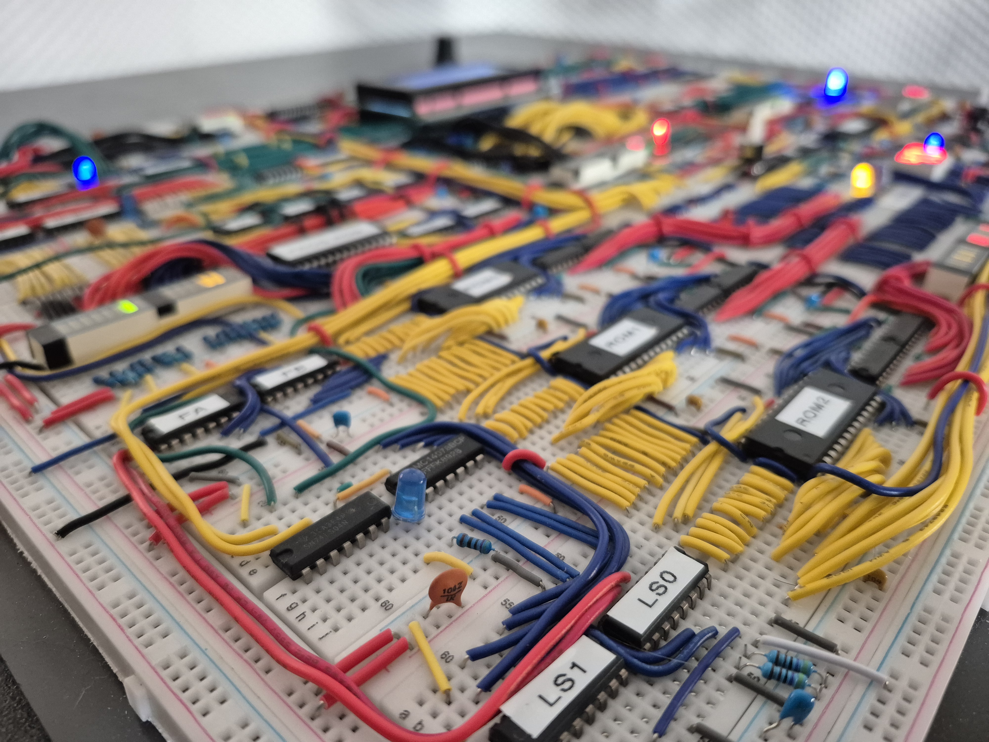
doc/img/pics/1000041111.jpg
