jorenheit/bfcpu/doc/img/pics/1000041112.jpg

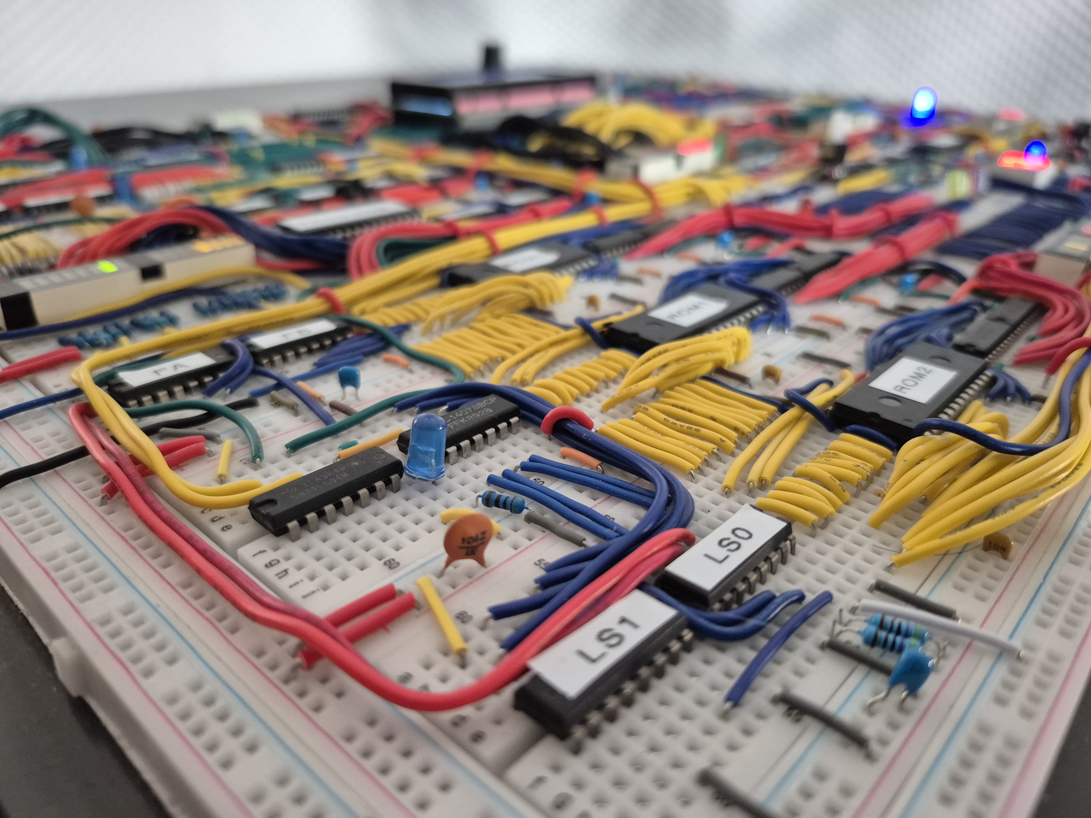
doc/img/pics/1000041112.jpg
