jorenheit/bfcpu/doc/img/pics/1000041114.jpg

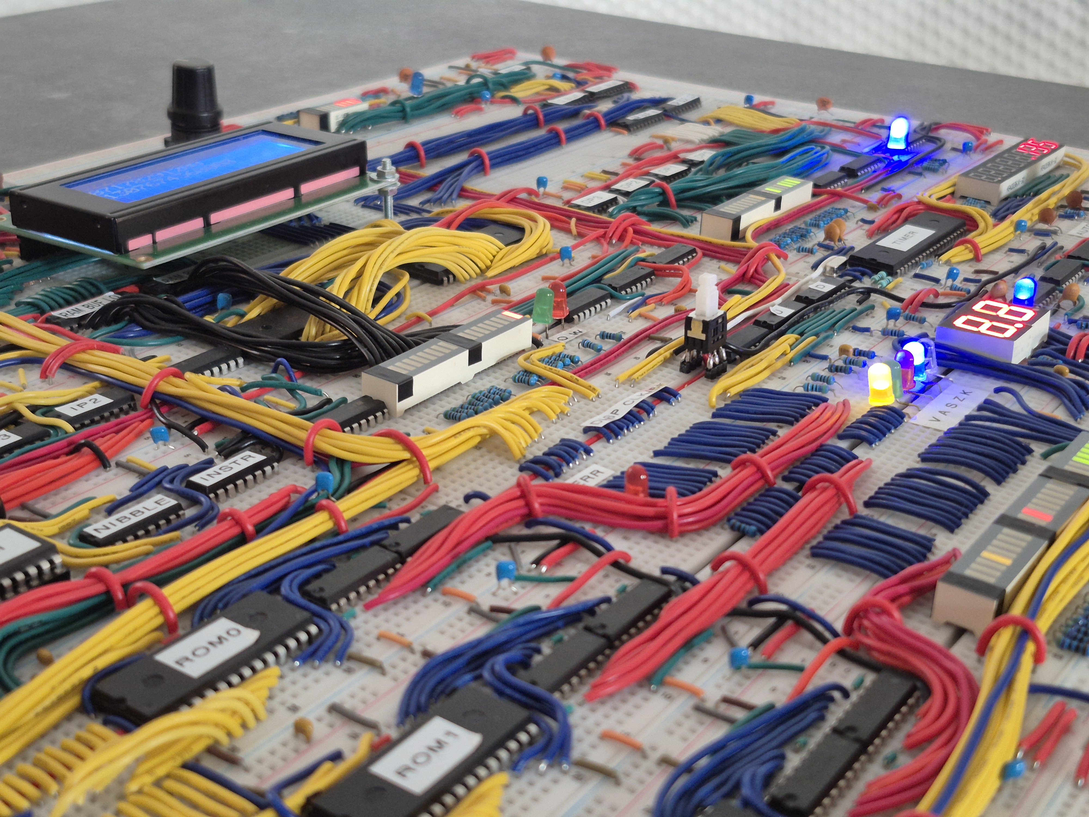
doc/img/pics/1000041114.jpg
