jorenheit/bfcpu/doc/img/pics/1000041115.jpg

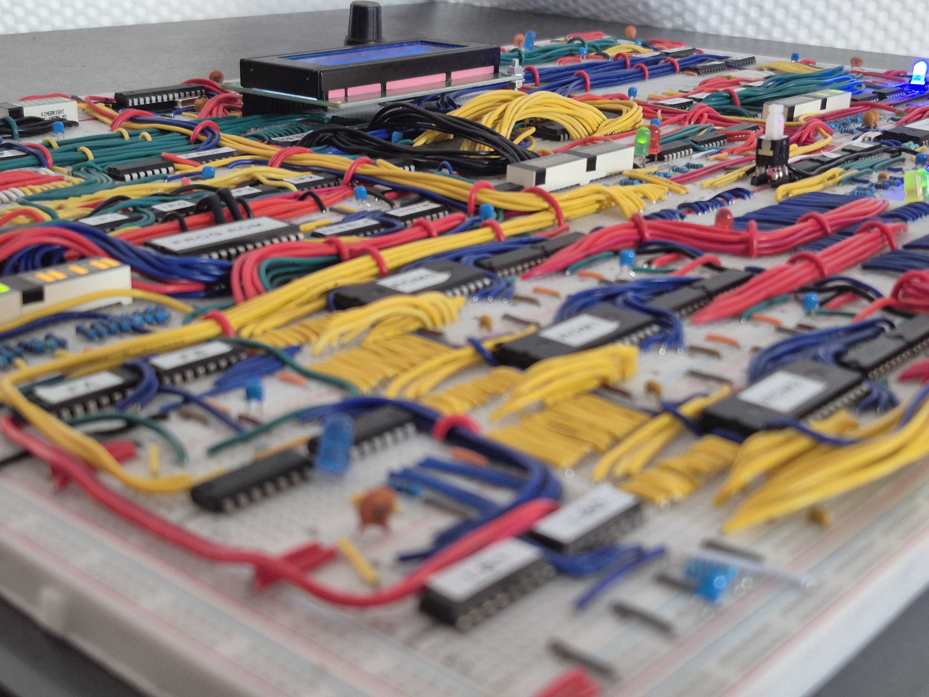
doc/img/pics/1000041115.jpg
