jorenheit/bfcpu/doc/img/pics/1000041116.jpg

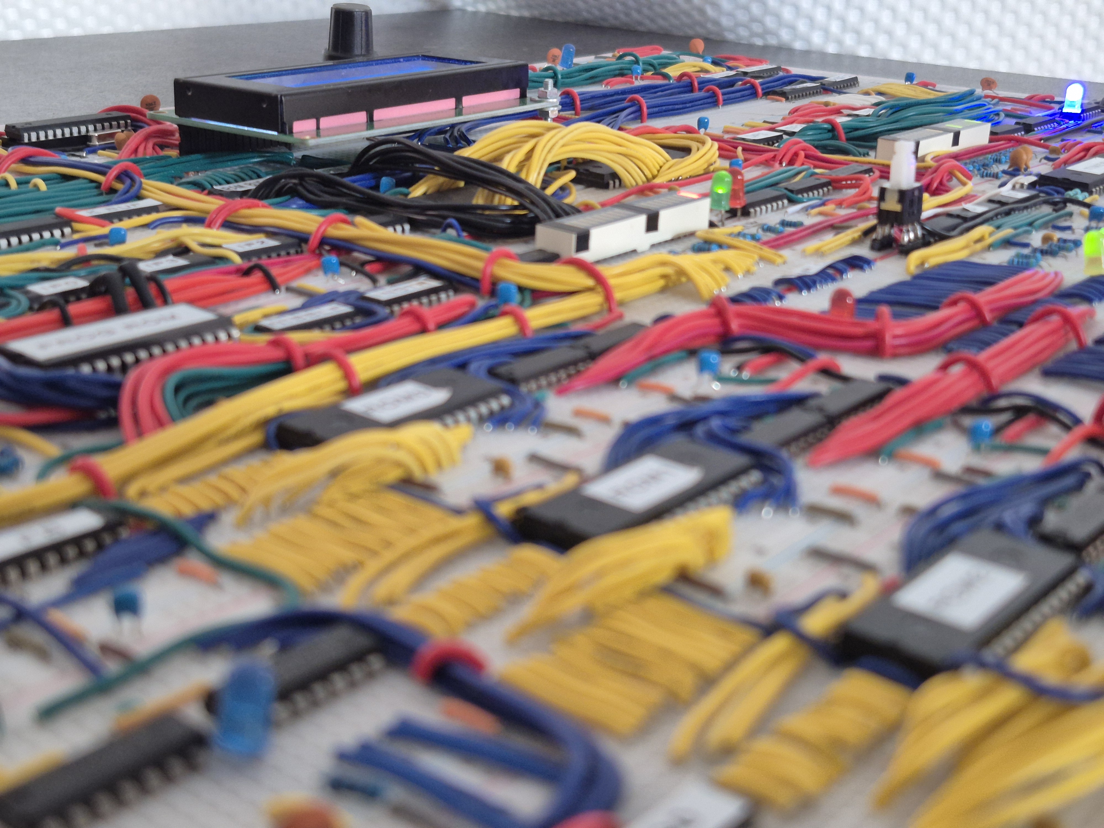
doc/img/pics/1000041116.jpg
