jorenheit/bfcpu/doc/img/pics/1000041126.jpg

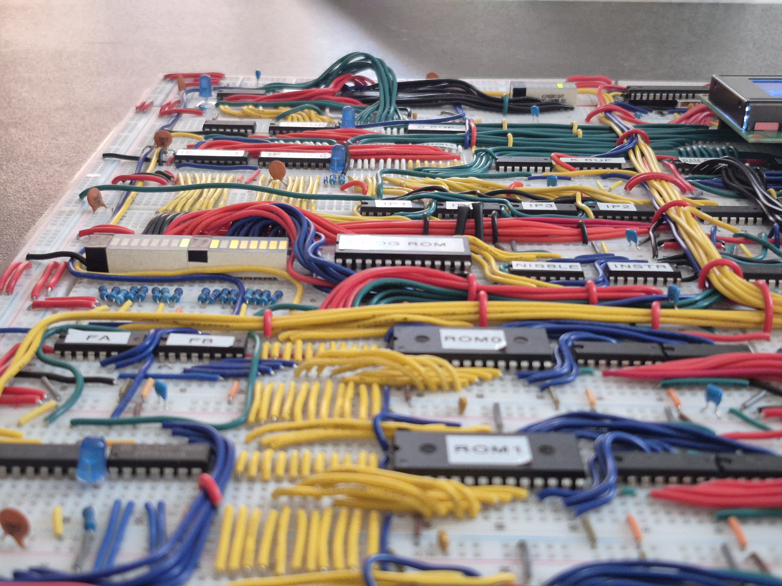
doc/img/pics/1000041126.jpg
