jorenheit/bfcpu/doc/img/pics/1000041127.jpg

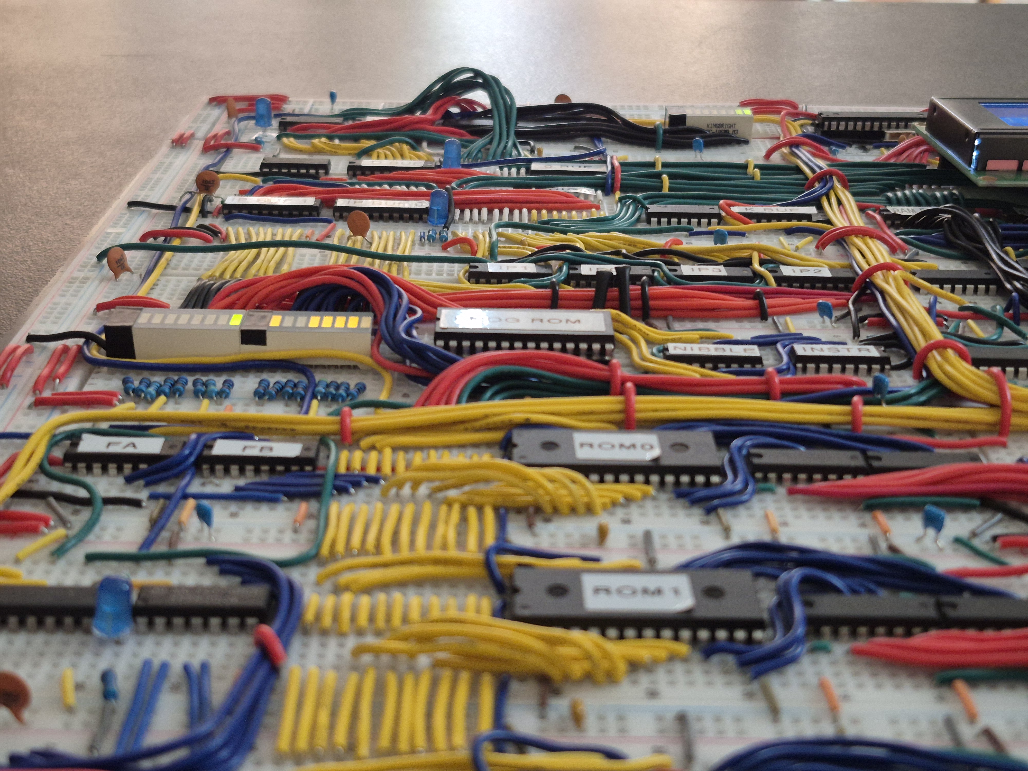
doc/img/pics/1000041127.jpg
