jorenheit/bfcpu/doc/img/pics/1000041128.jpg

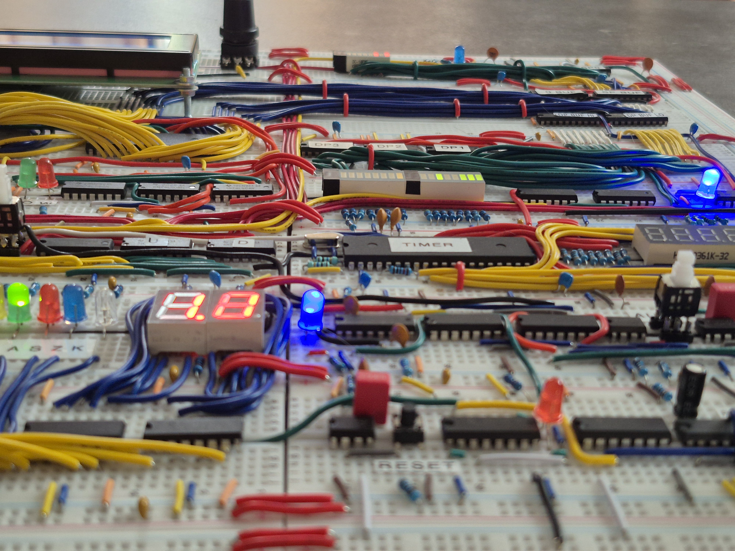
doc/img/pics/1000041128.jpg
