jorenheit/bfcpu/doc/img/pics/1000041129.jpg

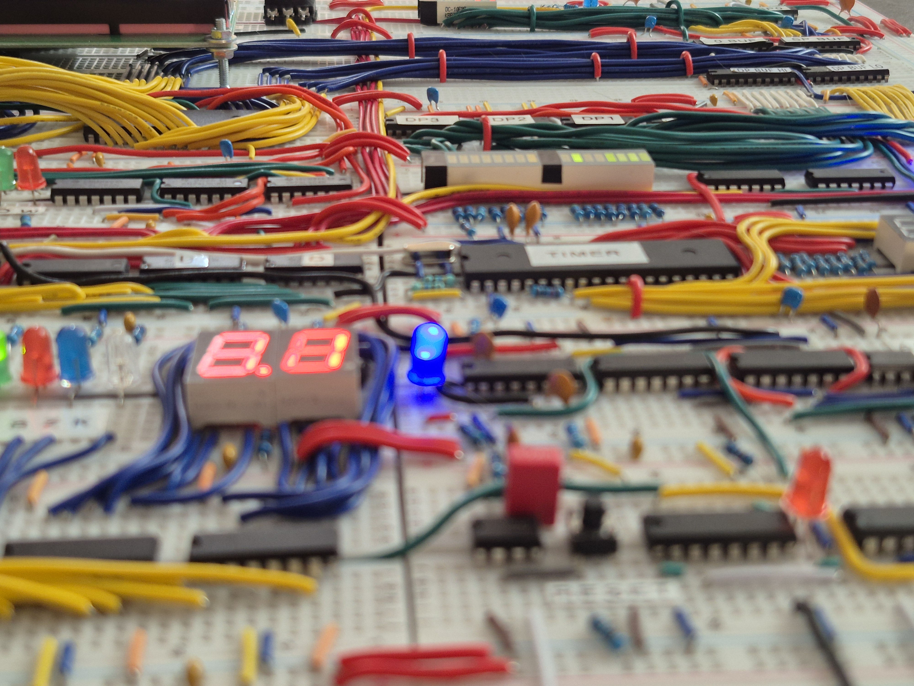
doc/img/pics/1000041129.jpg
