jorenheit/bfcpu/doc/img/pics/1000041130.jpg

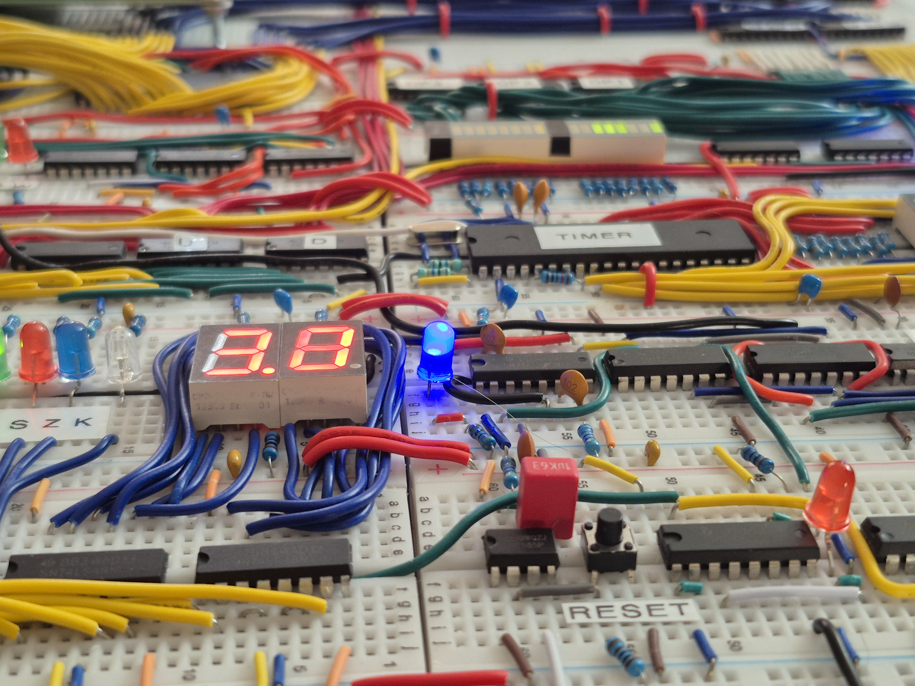
doc/img/pics/1000041130.jpg
