jorenheit/bfcpu/doc/img/pics/IMG-20231204-WA0006.jpeg

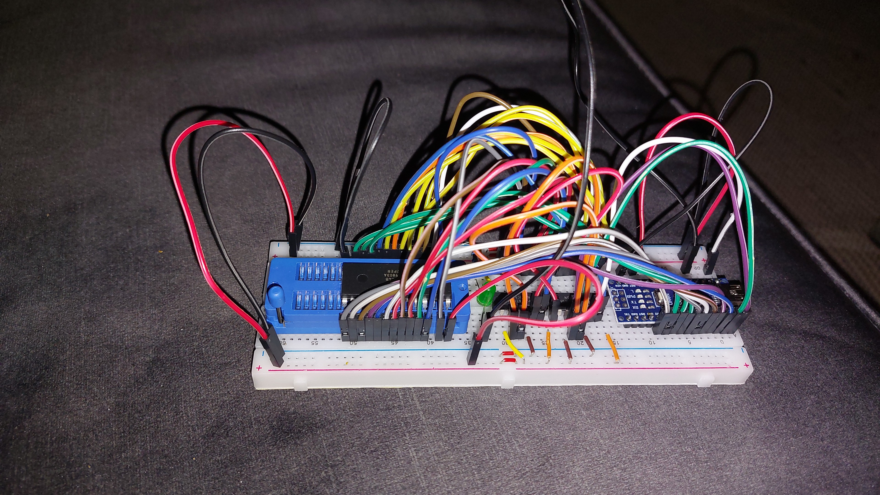
doc/img/pics/IMG-20231204-WA0006.jpeg
