jorenheit/bfcpu/doc/img/pics/IMG-20241211-WA0005.jpeg

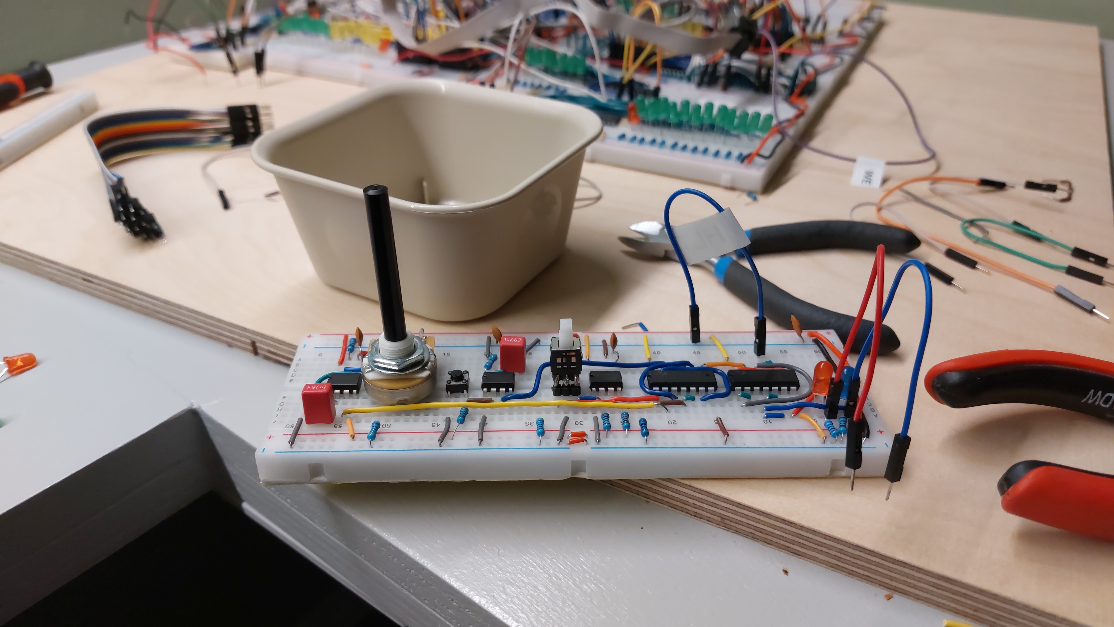
doc/img/pics/IMG-20241211-WA0005.jpeg
