jorenheit/bfcpu/doc/img/pics/IMG-20241214-WA0004.jpeg

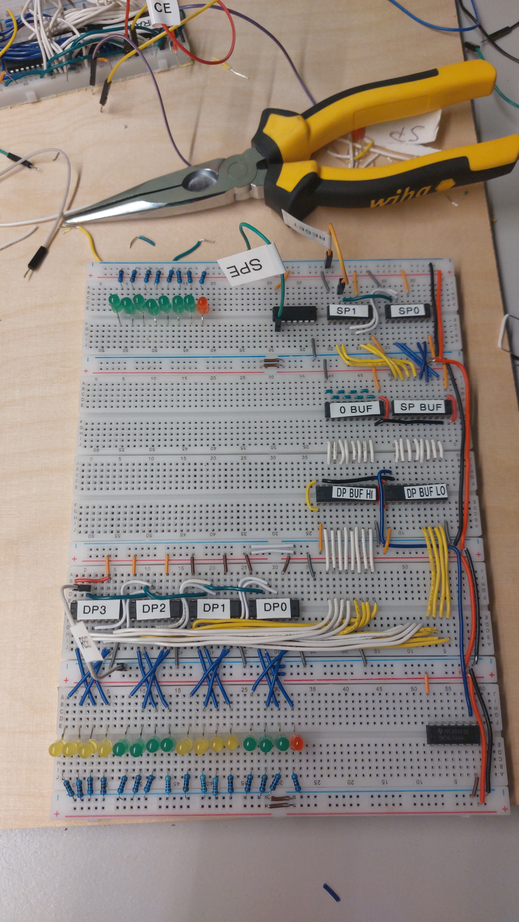
doc/img/pics/IMG-20241214-WA0004.jpeg
