jorenheit/bfcpu/doc/img/pics/IMG-20241214-WA0015.jpeg

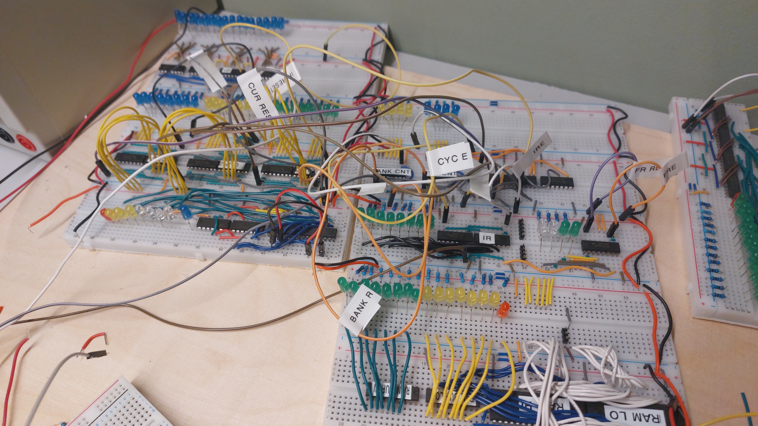
doc/img/pics/IMG-20241214-WA0015.jpeg
