jorenheit/bfcpu/doc/img/pics/IMG-20241214-WA0017.jpeg

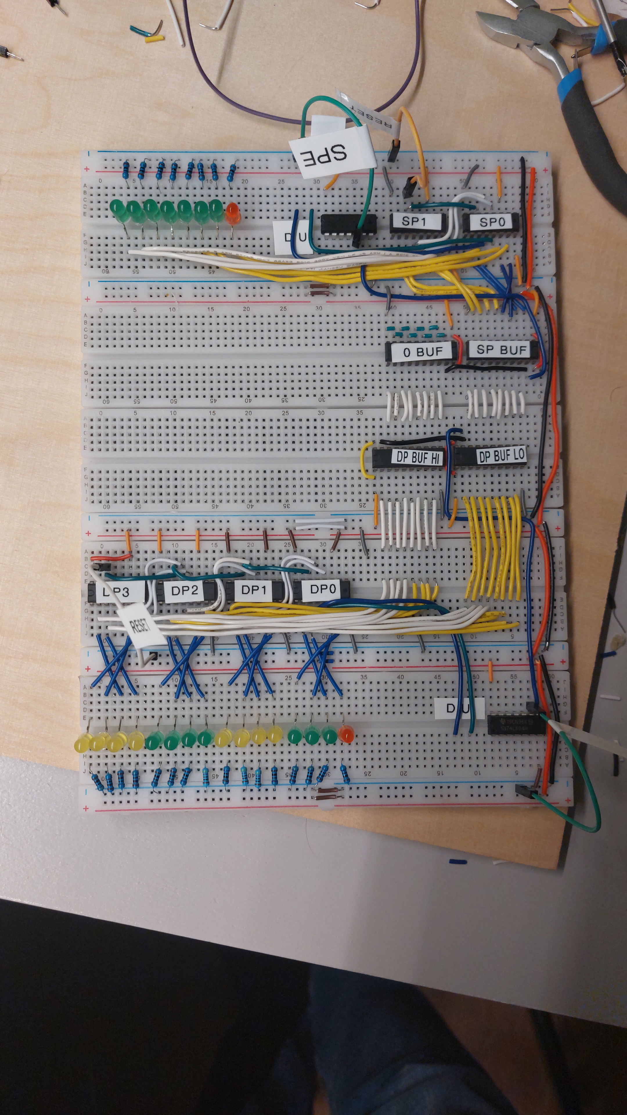
doc/img/pics/IMG-20241214-WA0017.jpeg
