jorenheit/bfcpu/doc/img/pics/IMG-20241218-WA0011.jpeg

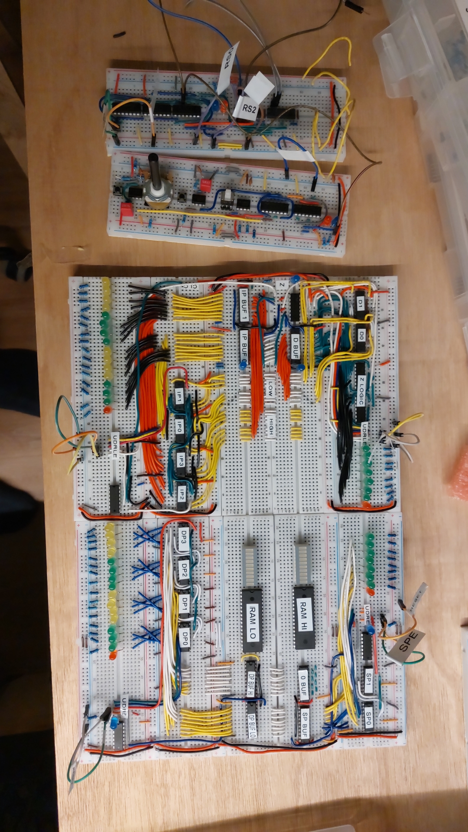
doc/img/pics/IMG-20241218-WA0011.jpeg
