jorenheit/bfcpu/doc/img/pics/IMG-20241219-WA0006.jpeg

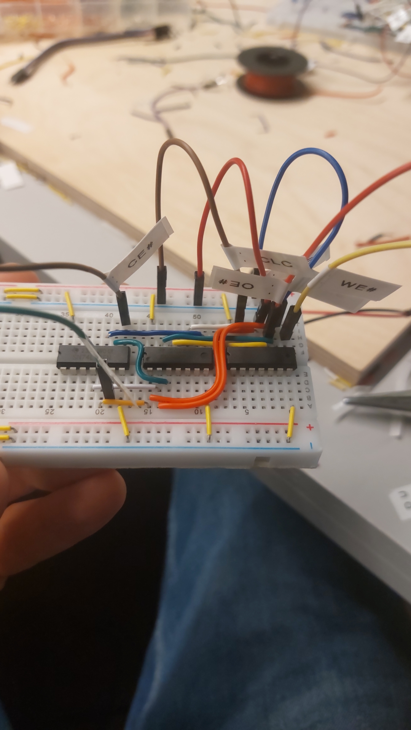
doc/img/pics/IMG-20241219-WA0006.jpeg
