jorenheit/bfcpu/doc/img/pics/IMG-20241221-WA0018.jpeg

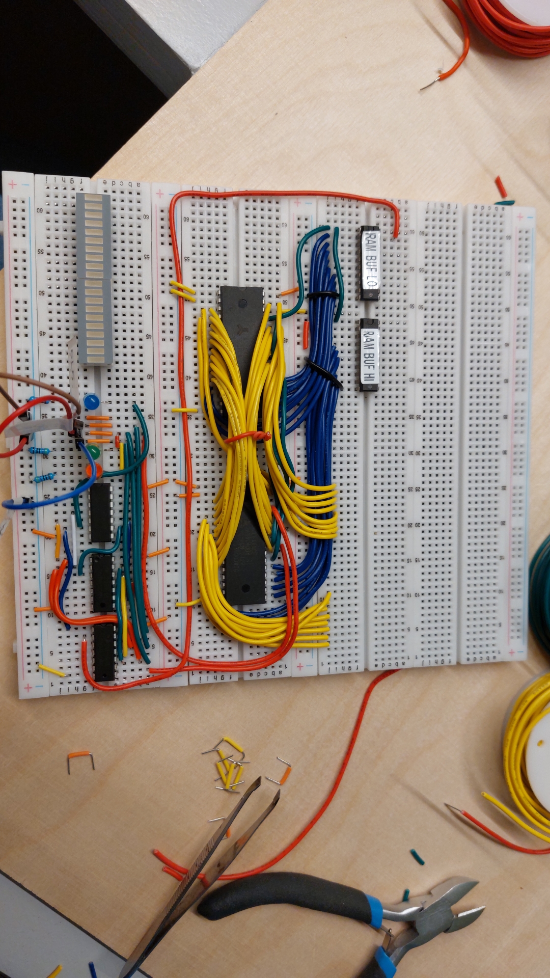
doc/img/pics/IMG-20241221-WA0018.jpeg
