jorenheit/bfcpu/doc/img/pics/IMG-20241222-WA0000.jpeg

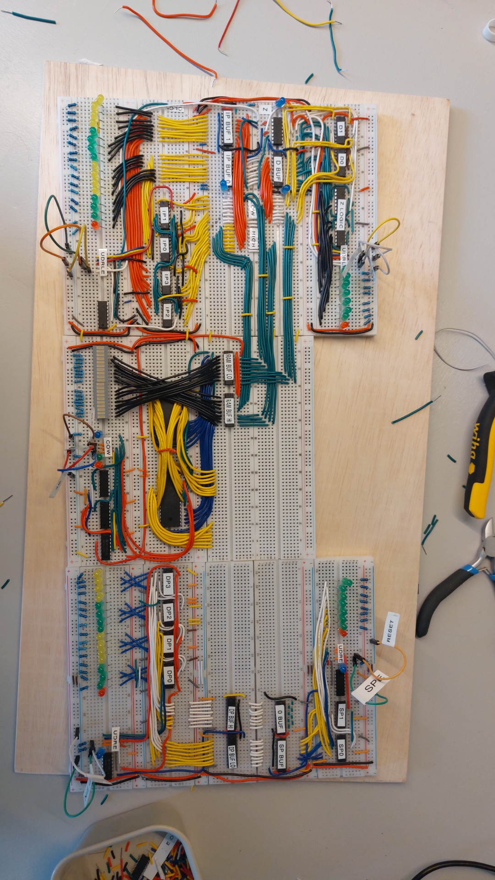
doc/img/pics/IMG-20241222-WA0000.jpeg
