jorenheit/bfcpu/doc/img/pics/IMG-20250124-WA0000.jpeg

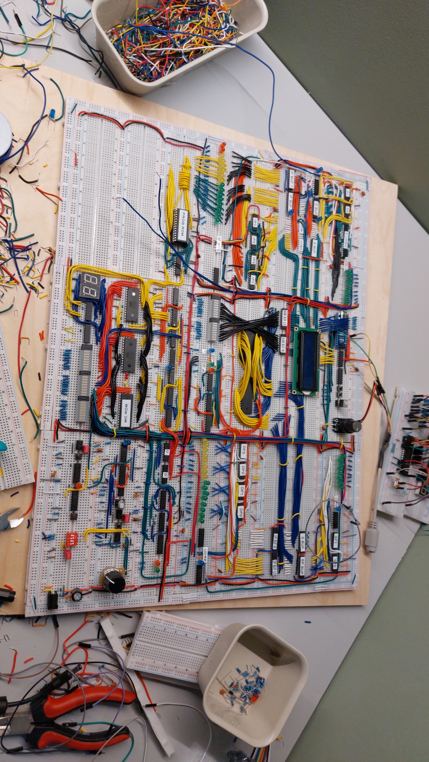
doc/img/pics/IMG-20250124-WA0000.jpeg
