jorenheit/bfcpu/doc/img/pics/IMG-20250208-WA0009.jpeg

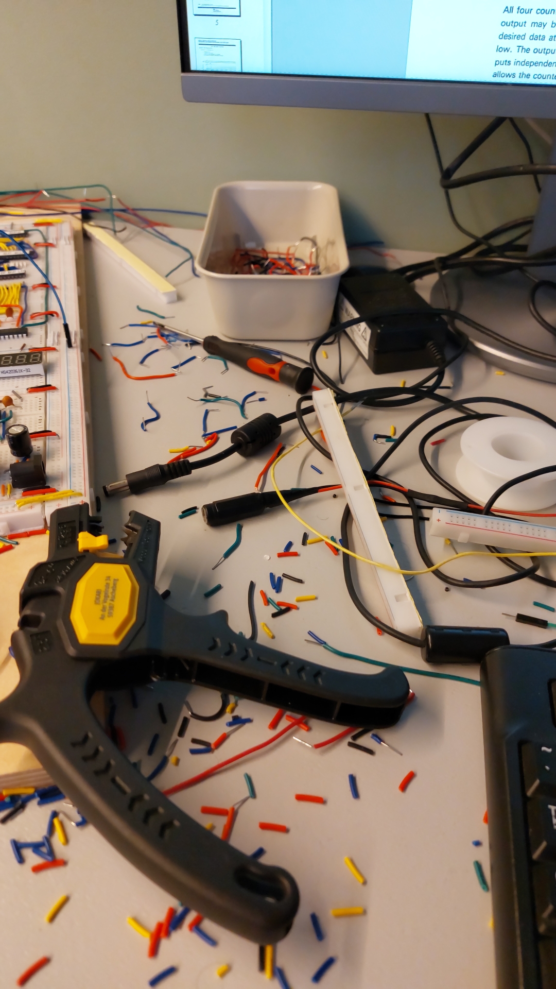
doc/img/pics/IMG-20250208-WA0009.jpeg
