jorenheit/bfcpu/doc/img/pics/IMG-20250208-WA0016.jpeg

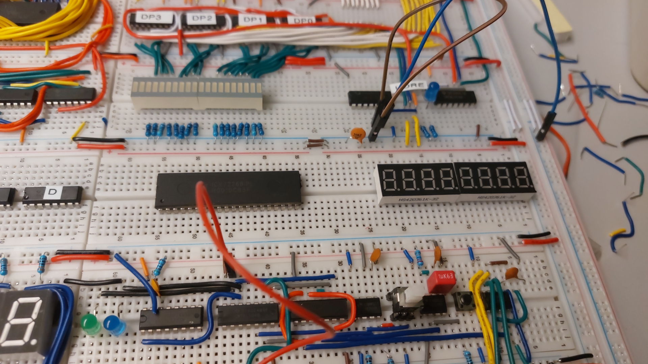
doc/img/pics/IMG-20250208-WA0016.jpeg
