jorenheit/bfcpu/doc/img/pics/tmp_f537dbe9-fe27-4f5a-86e8-230e47220219.jpeg

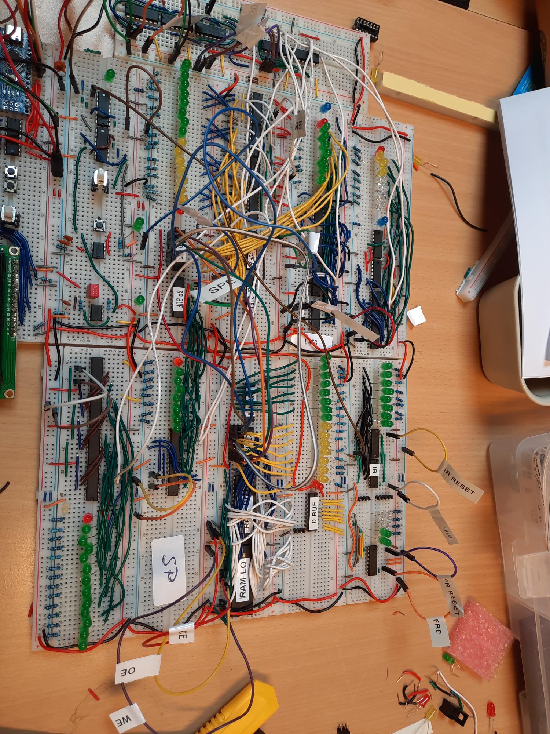
doc/img/pics/tmp_f537dbe9-fe27-4f5a-86e8-230e47220219.jpeg
