jorenheit/bfcpu/doc/img/placeholder.png

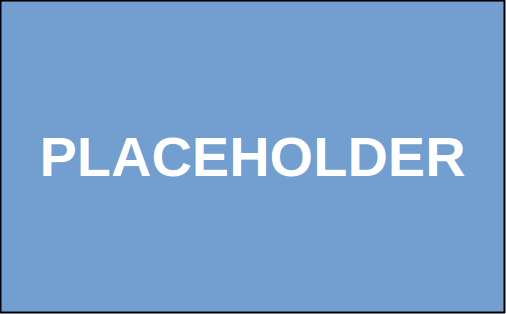
doc/img/placeholder.png
