jorenheit/bfcpu/doc/img/primes2.jpeg

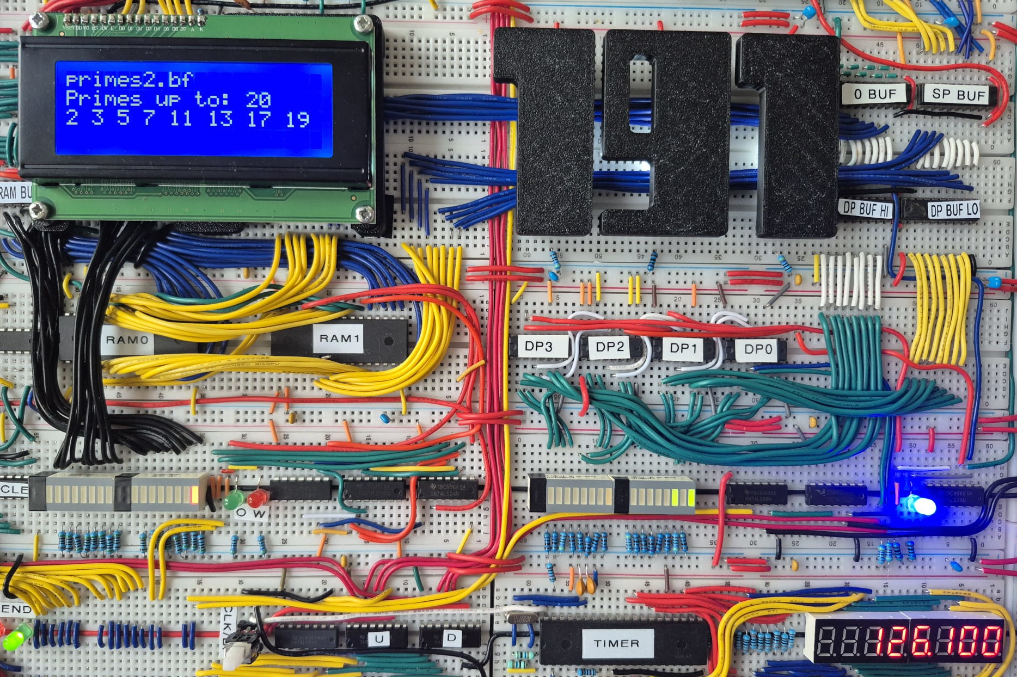
doc/img/primes2.jpeg
