jorenheit/bfcpu/doc/img/primes2stats.png

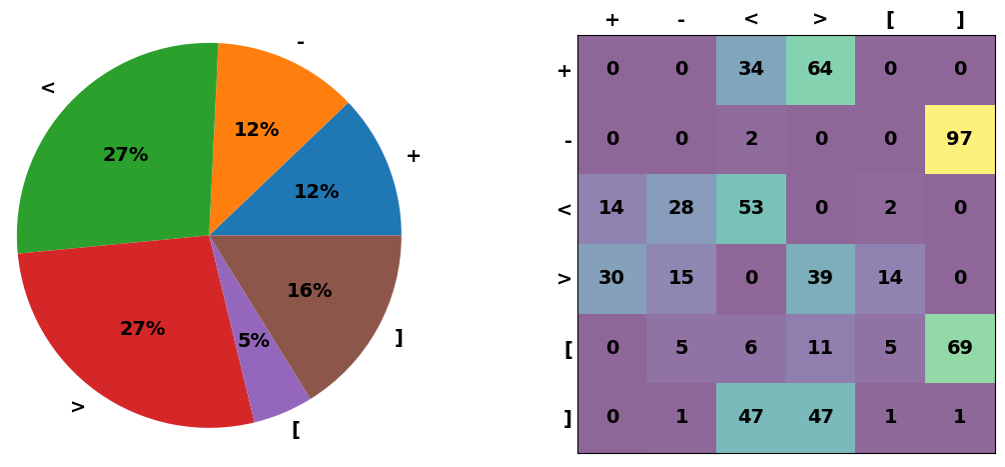
doc/img/primes2stats.png
