jorenheit/bfcpu/doc/img/primes.jpeg

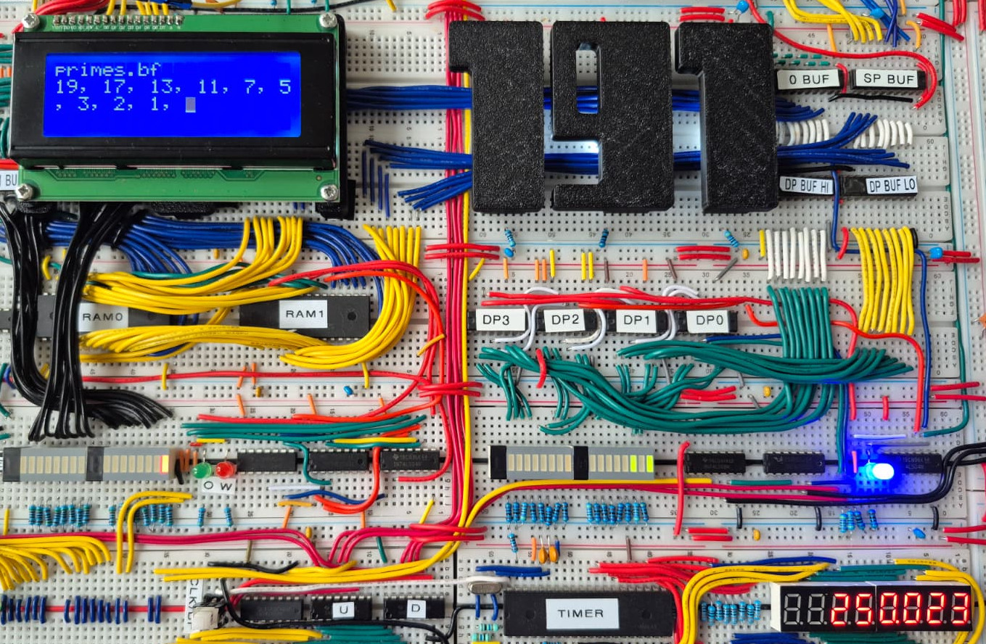
doc/img/primes.jpeg
