jorenheit/bfcpu/doc/img/primesstats.png

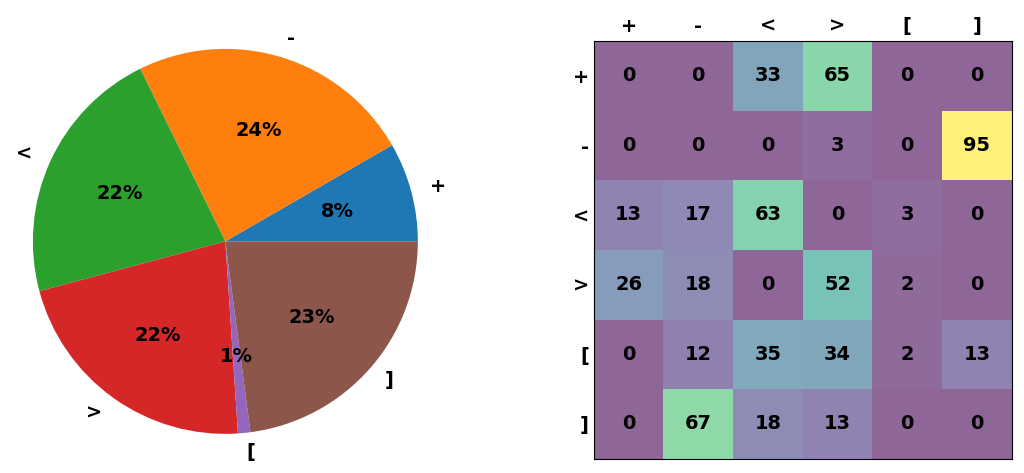
doc/img/primesstats.png
