jorenheit/bfcpu/doc/img/ram.png

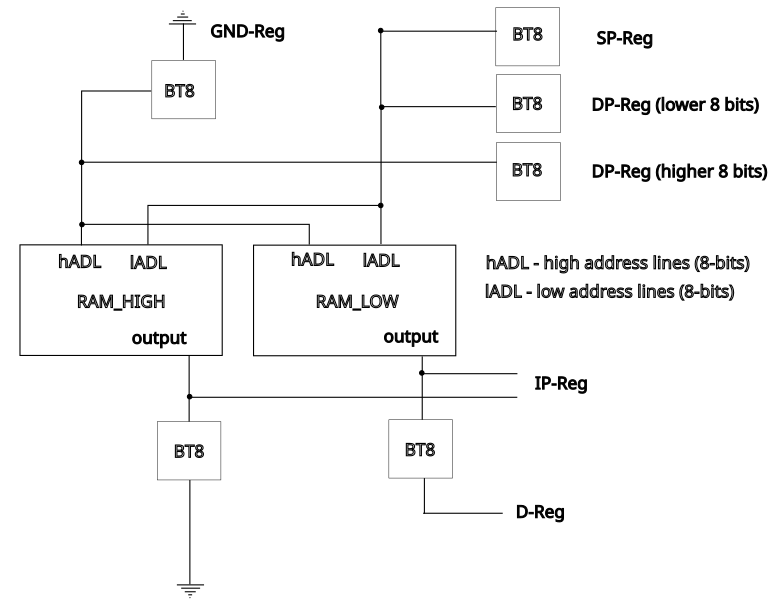
doc/img/ram.png
