jorenheit/bfcpu/doc/img/ram_buffer.jpg

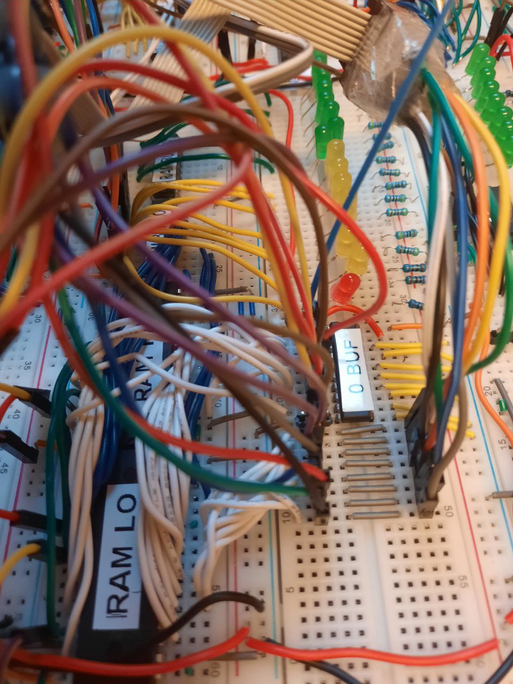
doc/img/ram_buffer.jpg
