jorenheit/bfcpu/doc/img/register_driver_circuit.png

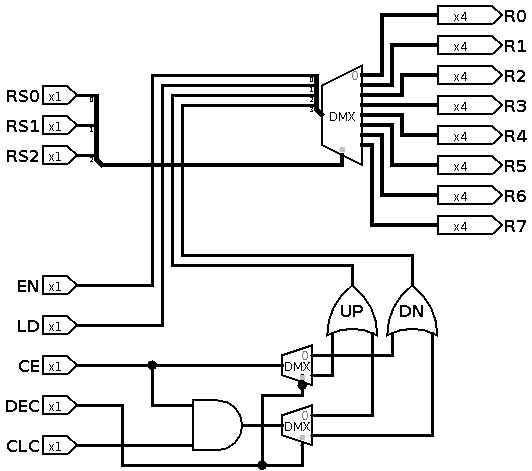
doc/img/register_driver_circuit.png
