jorenheit/bfcpu/doc/img/register_module_chaining.png

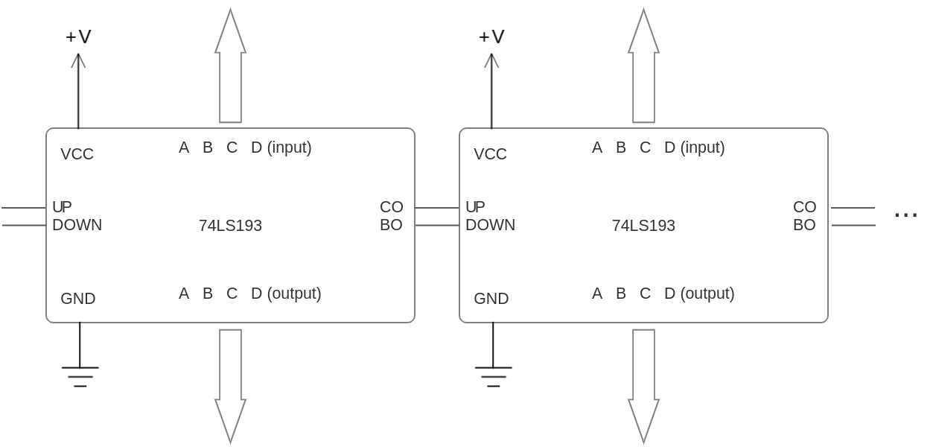
doc/img/register_module_chaining.png
