jorenheit/bfcpu/doc/img/screen.jpg

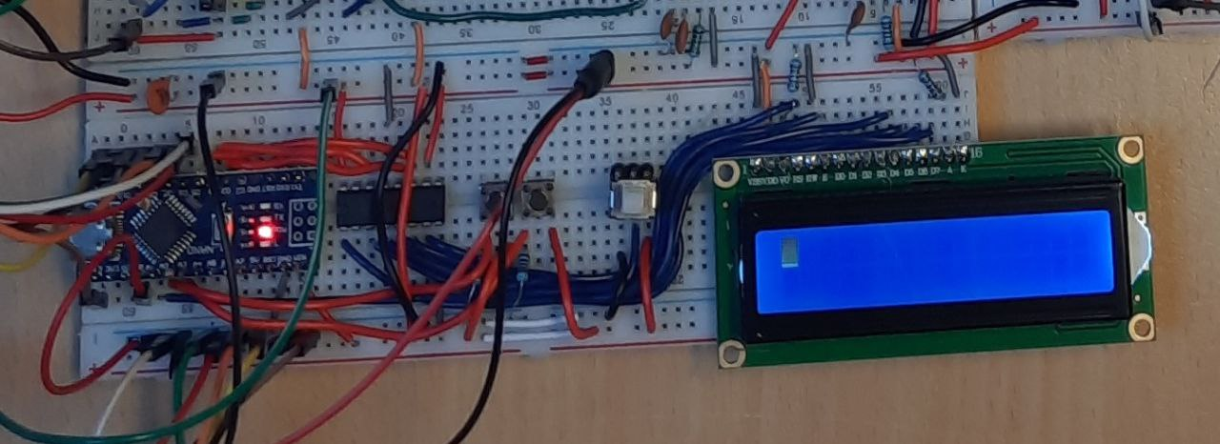
doc/img/screen.jpg
