jorenheit/bfcpu/doc/img/tictactoestats.png

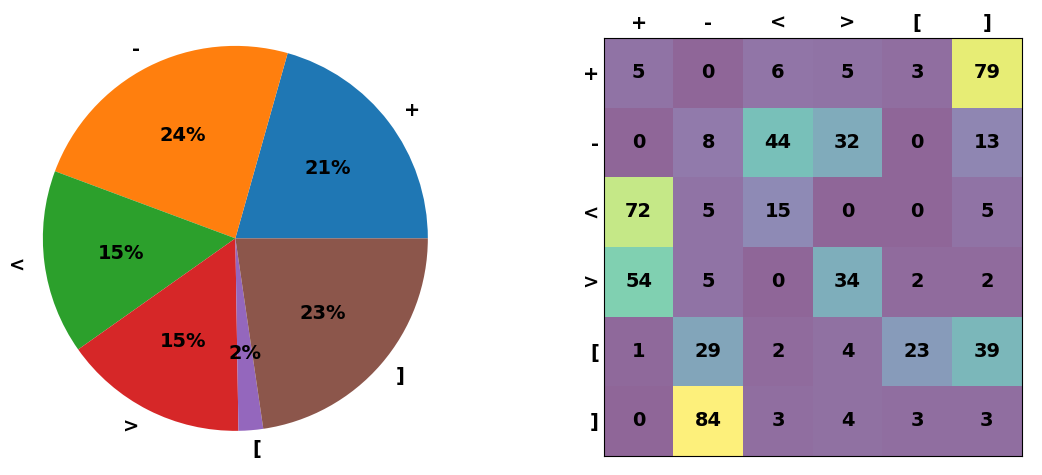
doc/img/tictactoestats.png
