jorenheit/bfcpu/doc/img/vonneumann.png

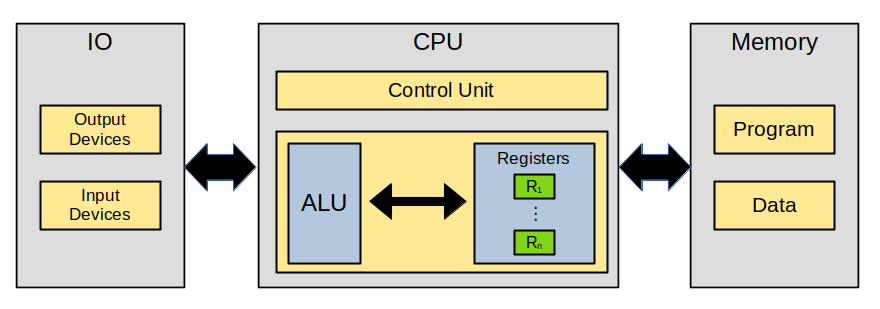
doc/img/vonneumann.png
