jorenheit/bfcpu/doc/img/waitextalg.png

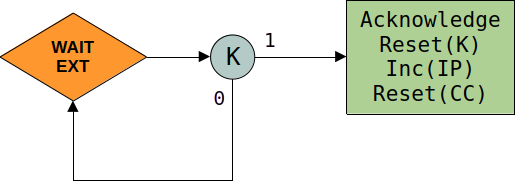
doc/img/waitextalg.png
