jorenheit/bfcpu/doc/img/computer_parts.png

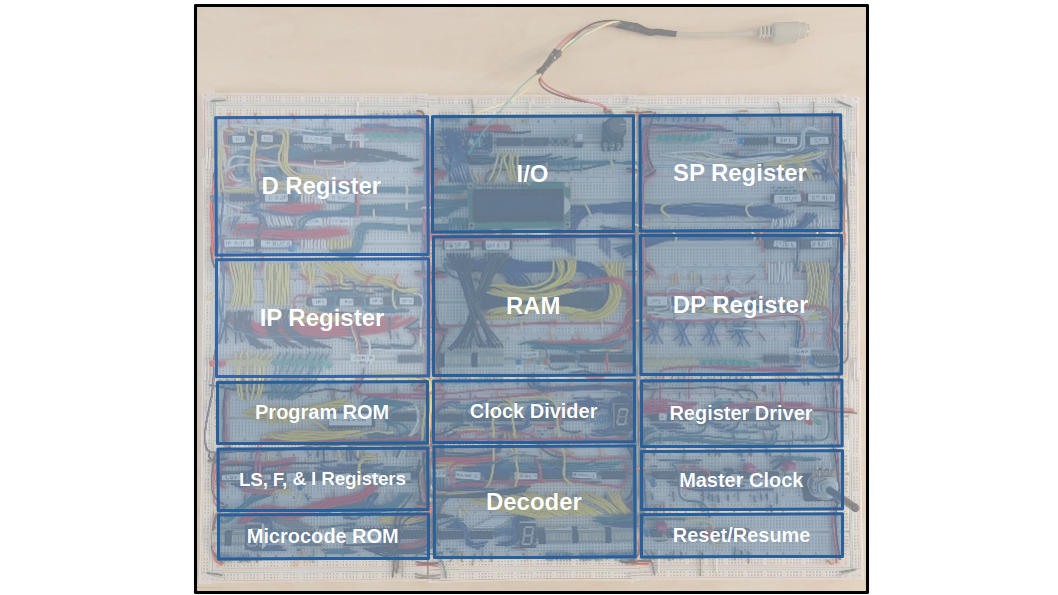
doc/img/computer_parts.png
