jorenheit/bfcpu/doc/schematics/controlunit2.pdf

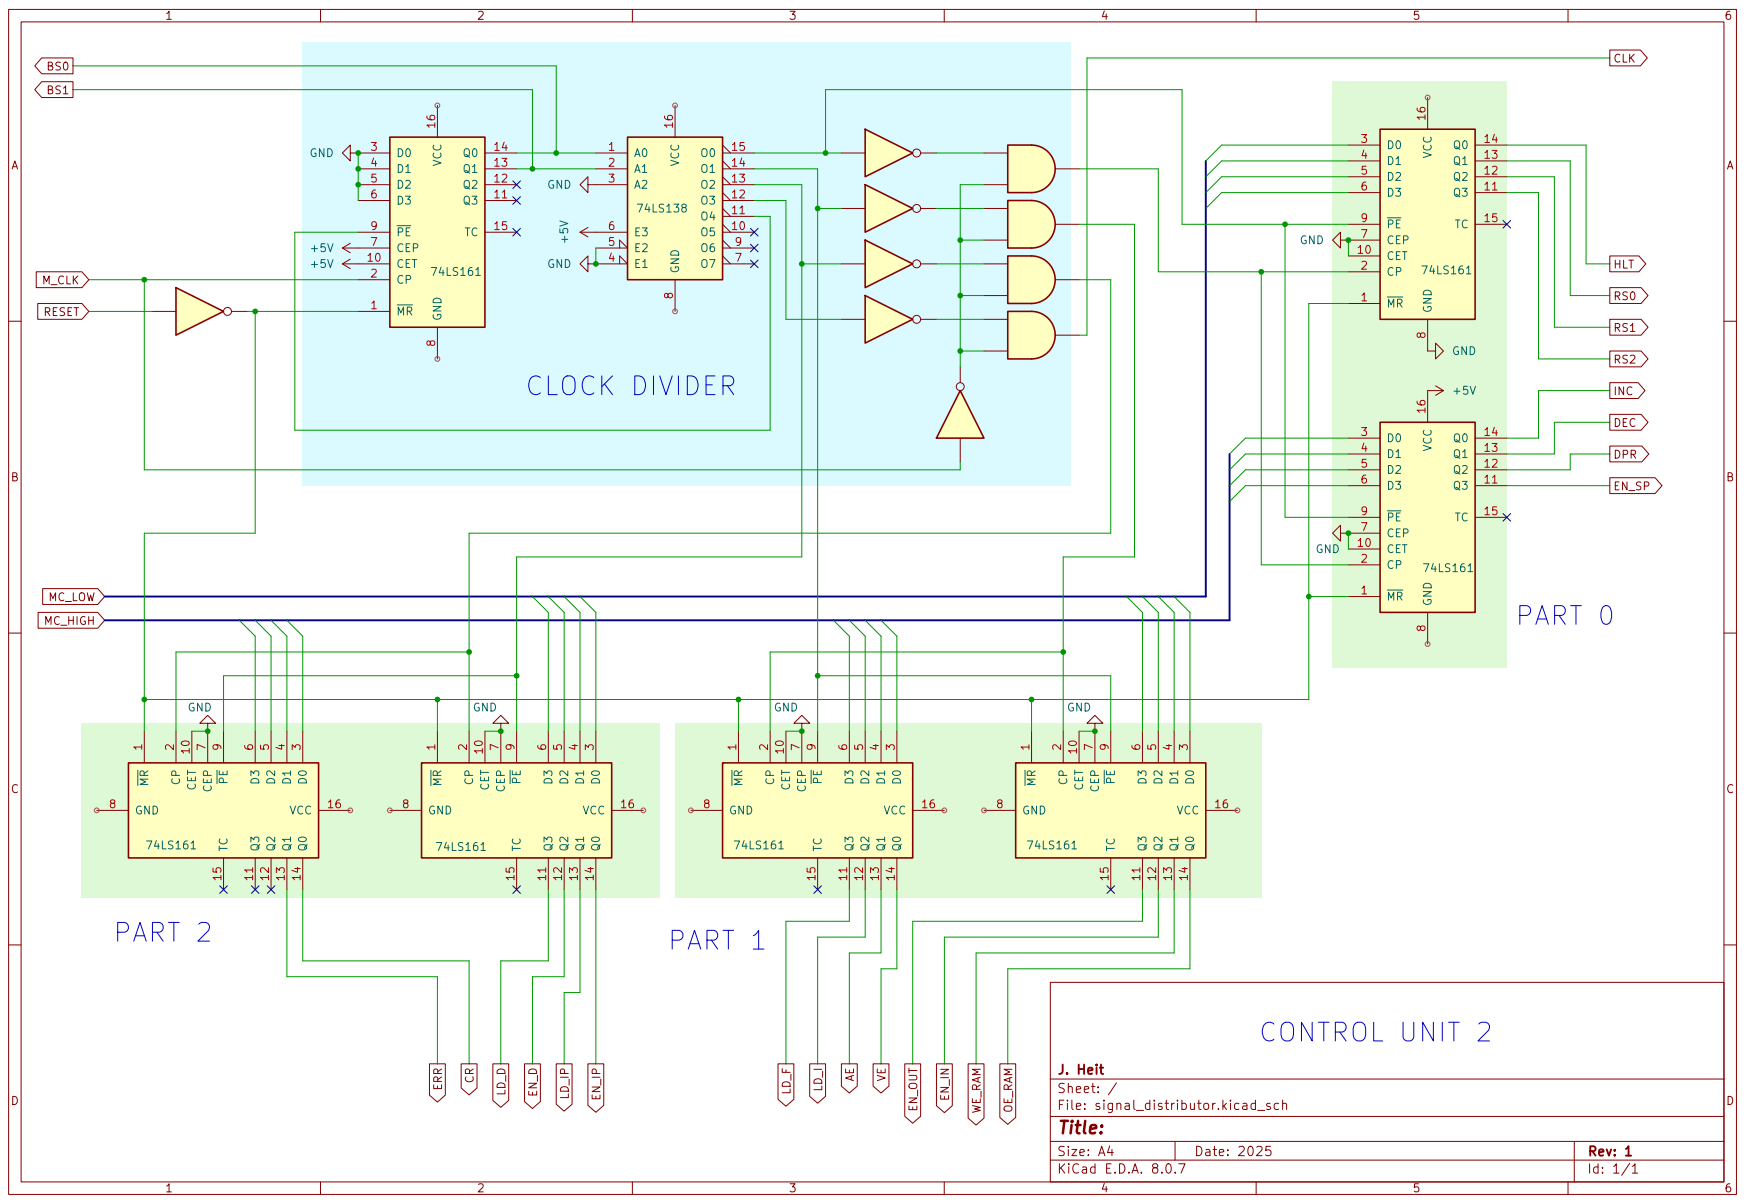
[picture p177: page 1]
