jorenheit/bfcpu/doc/schematics/eeprom_programmer.pdf

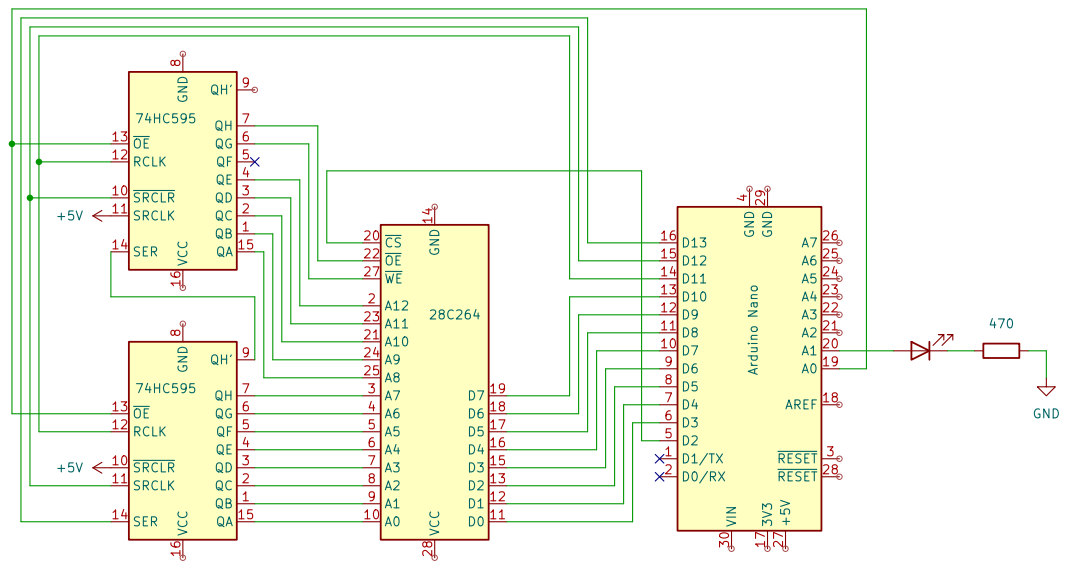
[picture p178: page 1]
