jorenheit/bfcpu/doc/schematics/instructionpointerregister.pdf

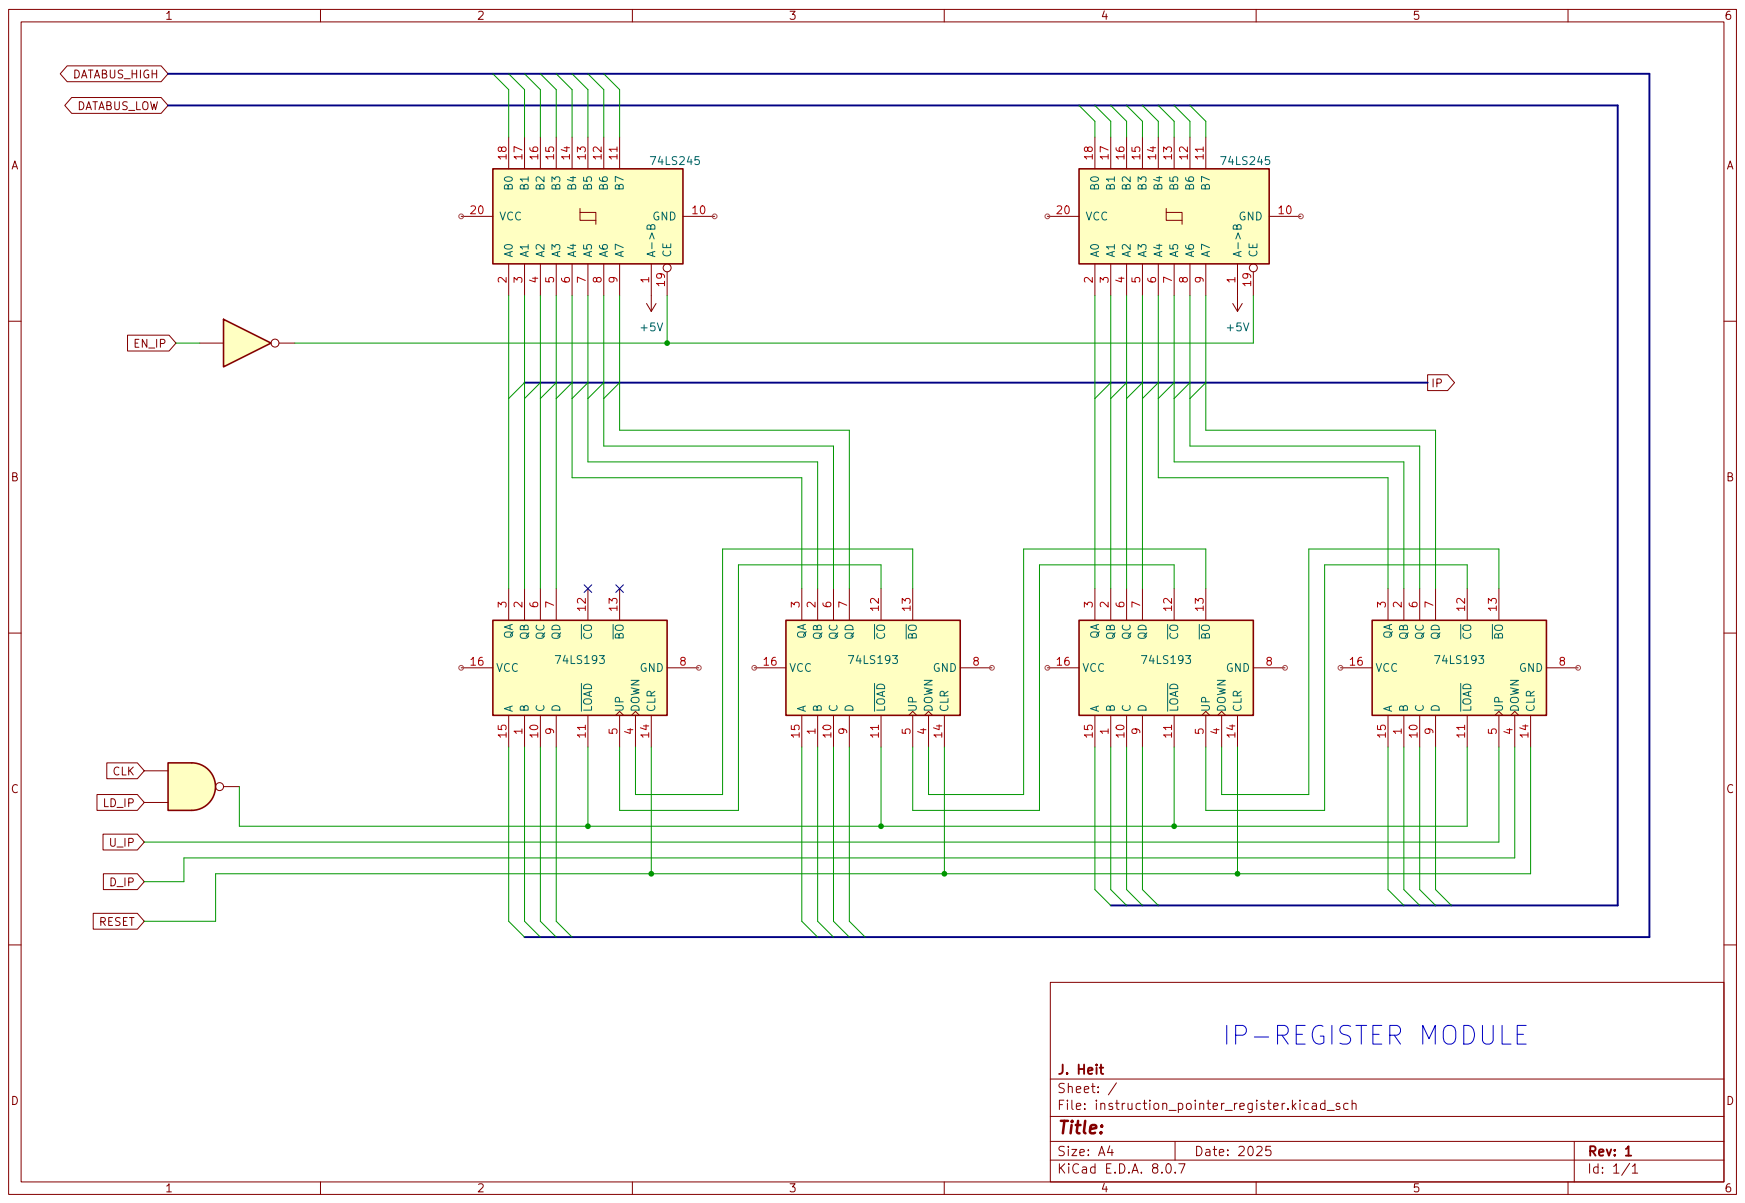
[picture p179: page 1]
