jorenheit/bfcpu/doc/schematics/stackpointerregister.pdf

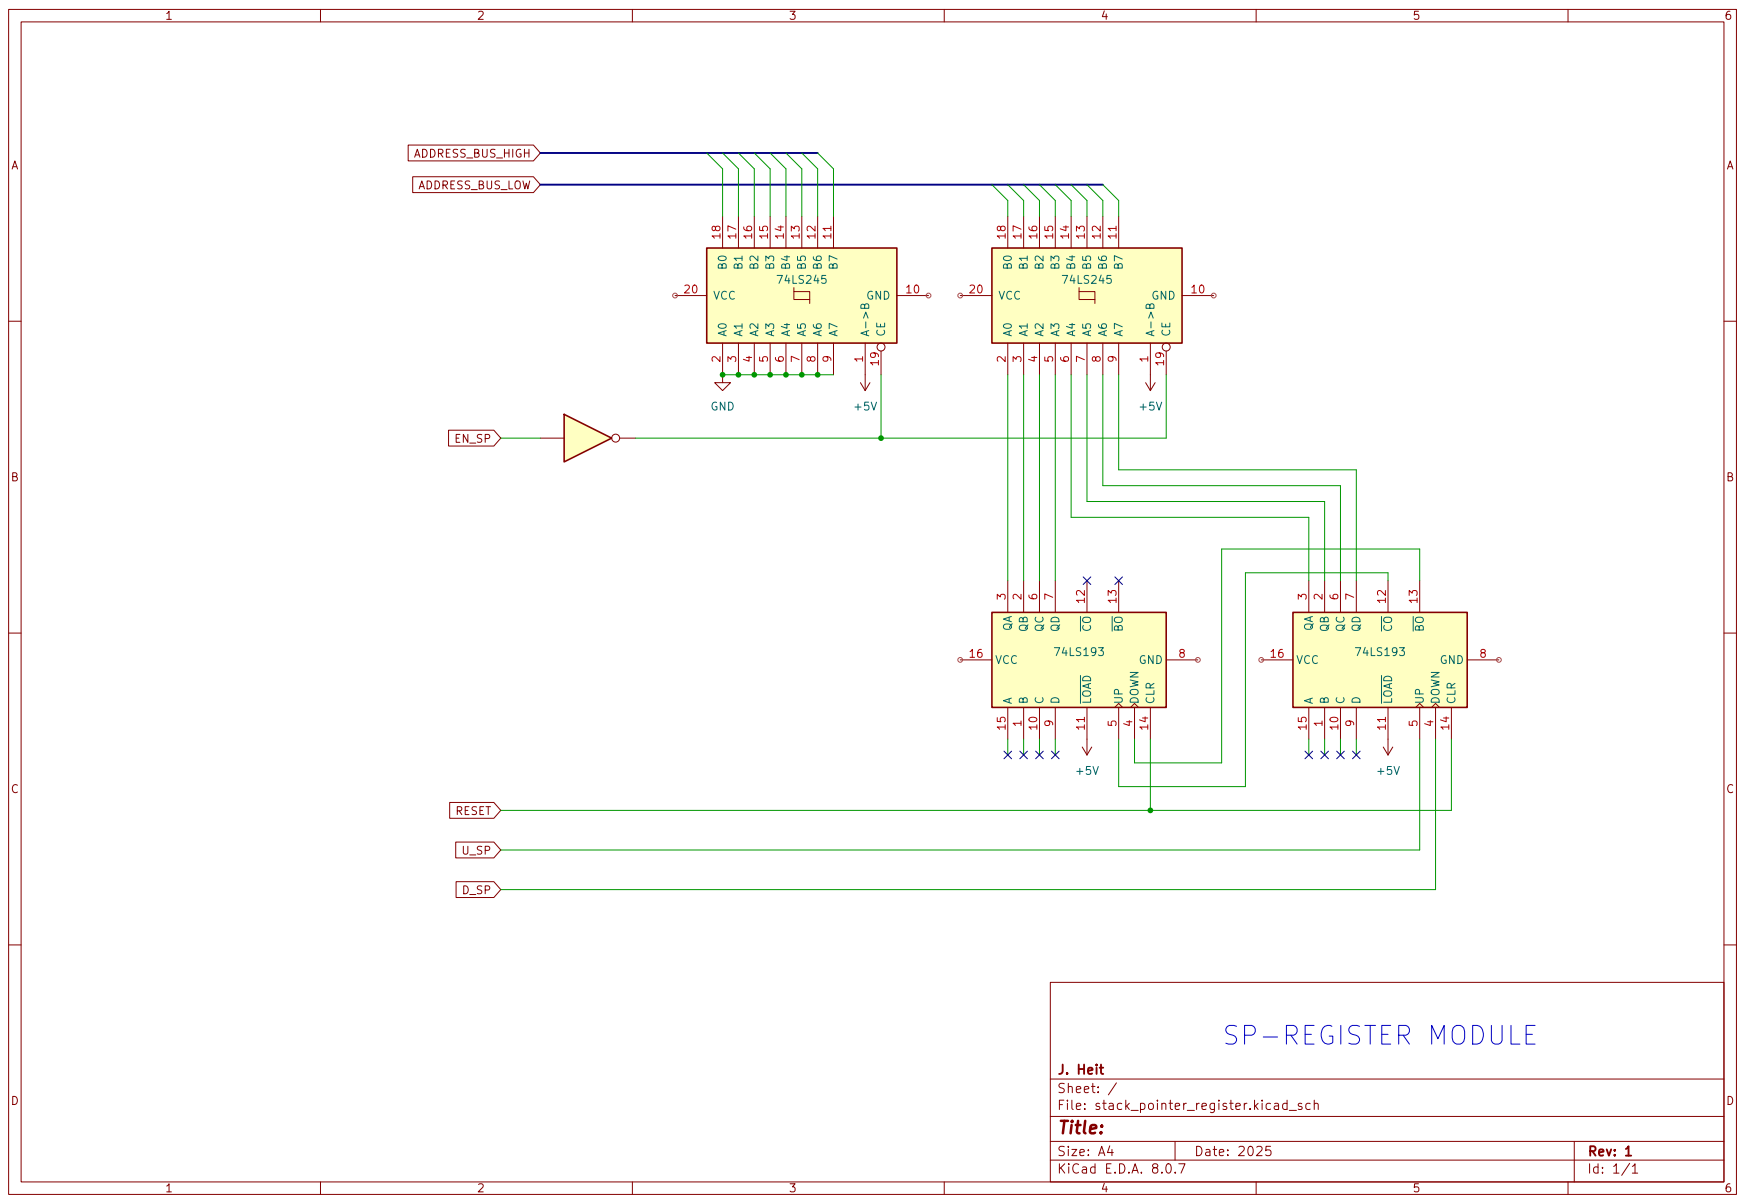
[picture p180: page 1]
