jorenheit/bfcpu/doc/circuits/control_unit.kicad_sch

## KiCad design doc/circuits/control_unit.kicad_sch (2025-11-01)

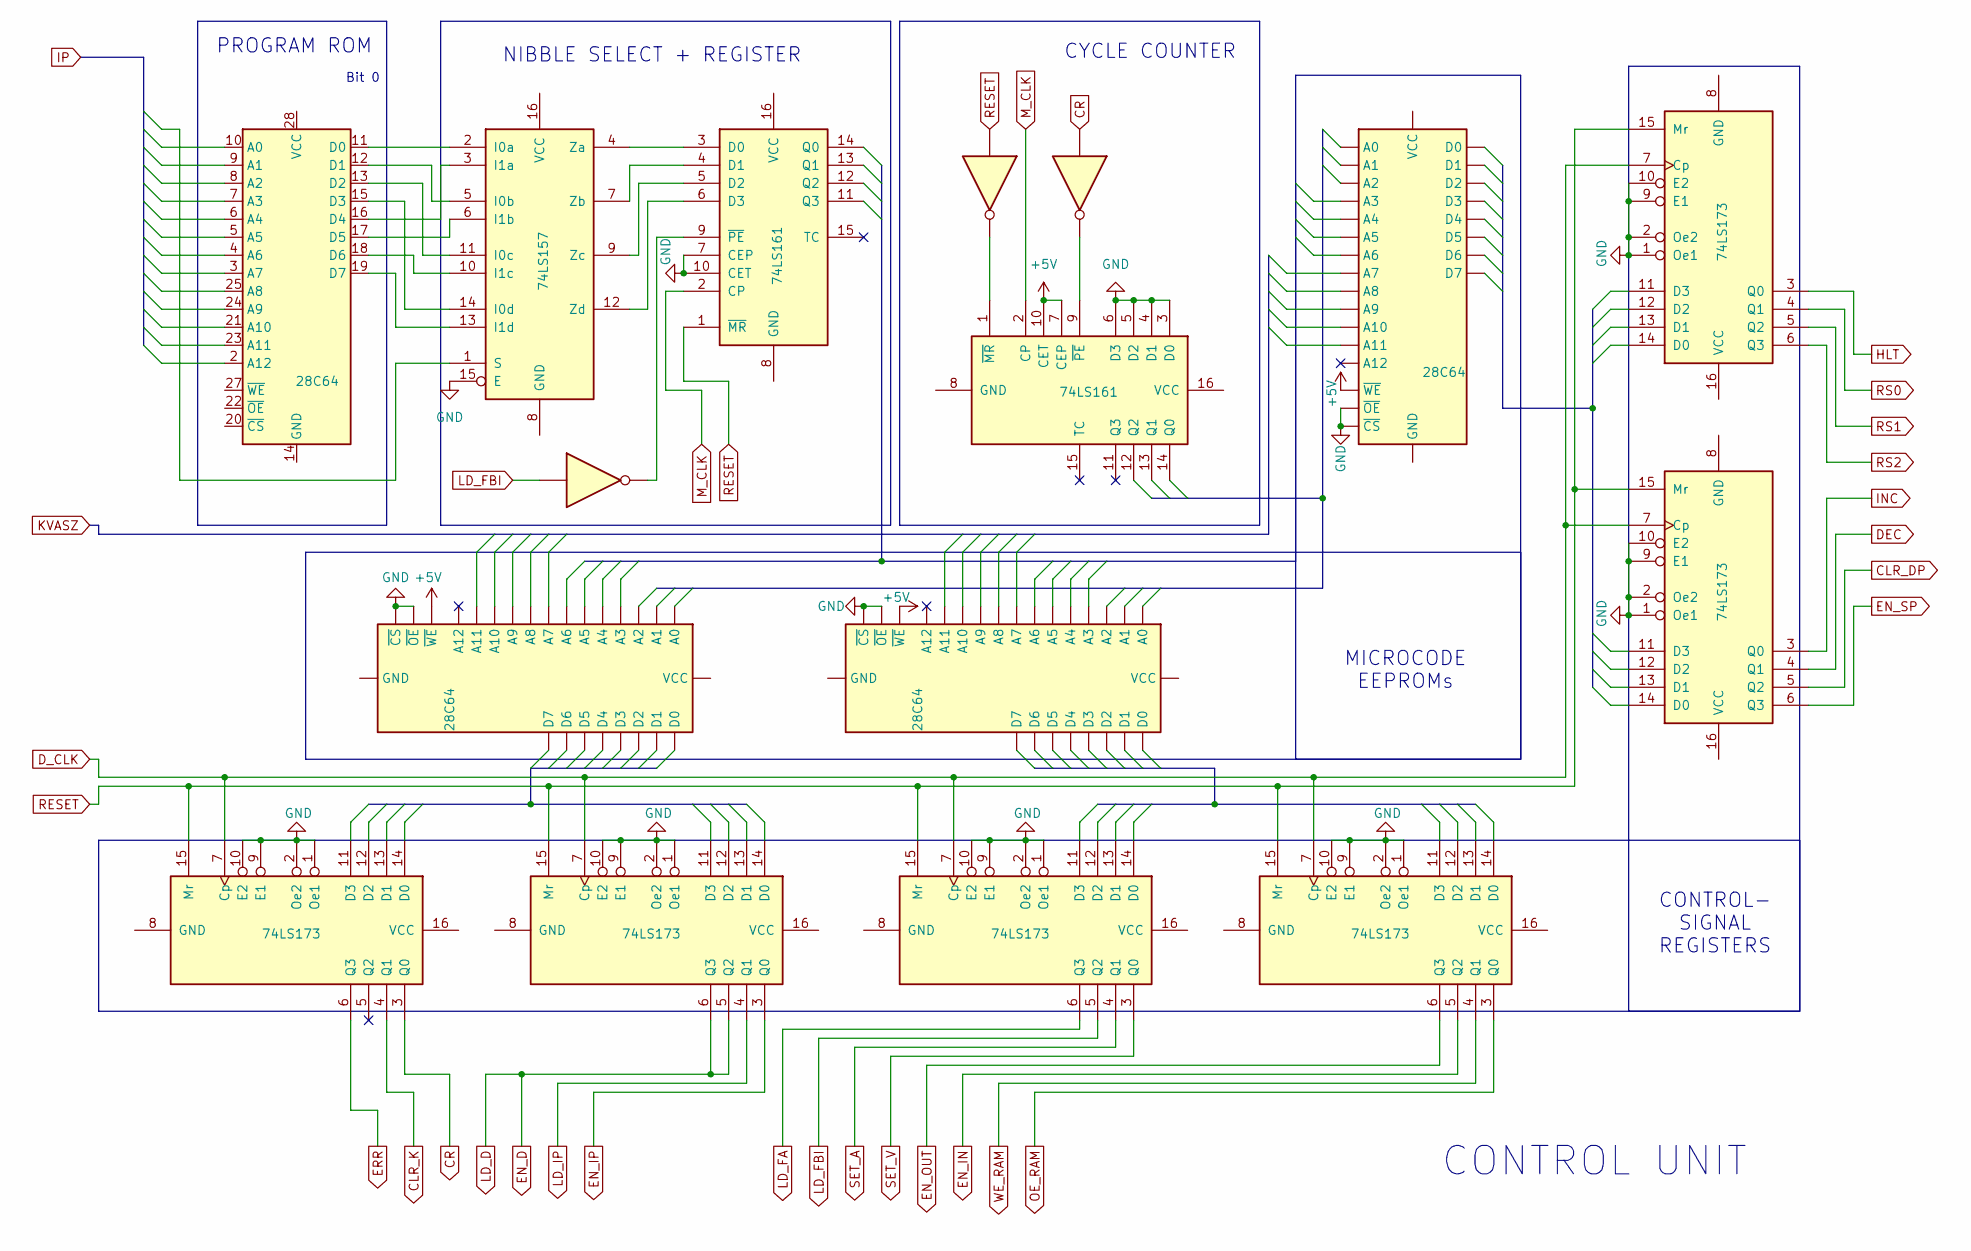
[picture p181: schematic control_unit.kicad_sch]

Parts:
U1, U3, U4, U5: 28C64
U2: 74LS157
U6, U16: 74LS161
U7, U8, U15: 74LS04
U9, U10, U11, U12, U13, U14: 74LS173

Connections:
+5V: U3.27 (~WE), U4.27 (~WE), U5.27 (~WE), U6.7 (CEP), U6.10 (CET)
CLR_DP: U13.5 (Q2)
CLR_K: U9.4 (Q1)
CR: U8.1, U9.3 (Q0)
DEC: U13.4 (Q1)
D_CLK: U9.7 (Cp), U10.7 (Cp), U11.7 (Cp), U12.7 (Cp), U13.7 (Cp), U14.7 (Cp)
EN_D: U10.5 (Q2), U10.6 (Q3)
EN_IN: U12.5 (Q2)
EN_IP: U10.3 (Q0)
EN_OUT: U12.6 (Q3)
EN_SP: U13.6 (Q3)
ERR: U9.6 (Q3)
GND: U2.15 (E), U3.20 (~CS), U3.22 (~OE), U4.20 (~CS), U4.22 (~OE), U5.20 (~CS), U5.22 (~OE), U6.3 (D0), U6.4 (D1), U6.5 (D2), U6.6 (D3), U9.1 (Oe1), U9.2 (Oe2), U9.9 (E1), U9.10 (E2), U10.1 (Oe1), U10.2 (Oe2), U10.9 (E1), U10.10 (E2), U11.1 (Oe1), U11.2 (Oe2), U11.9 (E1), U11.10 (E2), U12.1 (Oe1), U12.2 (Oe2), U12.9 (E1), U12.10 (E2), U13.1 (Oe1), U13.2 (Oe2), U13.9 (E1), U13.10 (E2), U14.1 (Oe1), U14.2 (Oe2), U14.9 (E1), U14.10 (E2), U16.7 (CEP), U16.10 (CET)
HLT: U14.3 (Q0)
INC: U13.3 (Q0)
LD_FA: U11.6 (Q3)
LD_FBI: U11.5 (Q2), U15.1
LD_IP: U10.4 (Q1)
M_CLK: U6.2 (CP), U16.2 (CP)
unnamed: U1.11 (D0), U2.2 (I0a)
unnamed: U1.12 (D1), U2.5 (I0b)
unnamed: U1.13 (D2), U2.11 (I0c)
unnamed: U1.15 (D3), U2.14 (I0d)
unnamed: U1.16 (D4), U2.3 (I1a)
unnamed: U1.17 (D5), U2.6 (I1b)
unnamed: U1.18 (D6), U2.10 (I1c)
unnamed: U1.19 (D7), U2.13 (I1d)
unnamed: U6.1 (~MR), U7.2
unnamed: U6.9 (~PE), U8.2
unnamed: U15.2, U16.9 (~PE)
unnamed: U2.4 (Za), U16.3 (D0)
unnamed: U2.7 (Zb), U16.4 (D1)
unnamed: U2.9 (Zc), U16.5 (D2)
unnamed: U2.12 (Zd), U16.6 (D3)
OE_RAM: U12.3 (Q0)
RESET: U7.1, U9.15 (Mr), U10.15 (Mr), U11.15 (Mr), U12.15 (Mr), U13.15 (Mr), U14.15 (Mr), U16.1 (~MR)
RS0: U14.4 (Q1)
RS1: U14.5 (Q2)
RS2: U14.6 (Q3)
SET_A: U11.4 (Q1)
SET_V: U11.3 (Q0)
WE_RAM: U12.4 (Q1)

Notes on the sheet:
MICROCODE EEPROMs
Bit 0
PROGRAM ROM
CONTROL- SIGNAL REGISTERS
NIBBLE SELECT + REGISTER
CYCLE COUNTER
CONTROL UNIT
