jorenheit/bfcpu/doc/circuits/data_pointer_register.kicad_sch

## KiCad design doc/circuits/data_pointer_register.kicad_sch (2025-03-10)

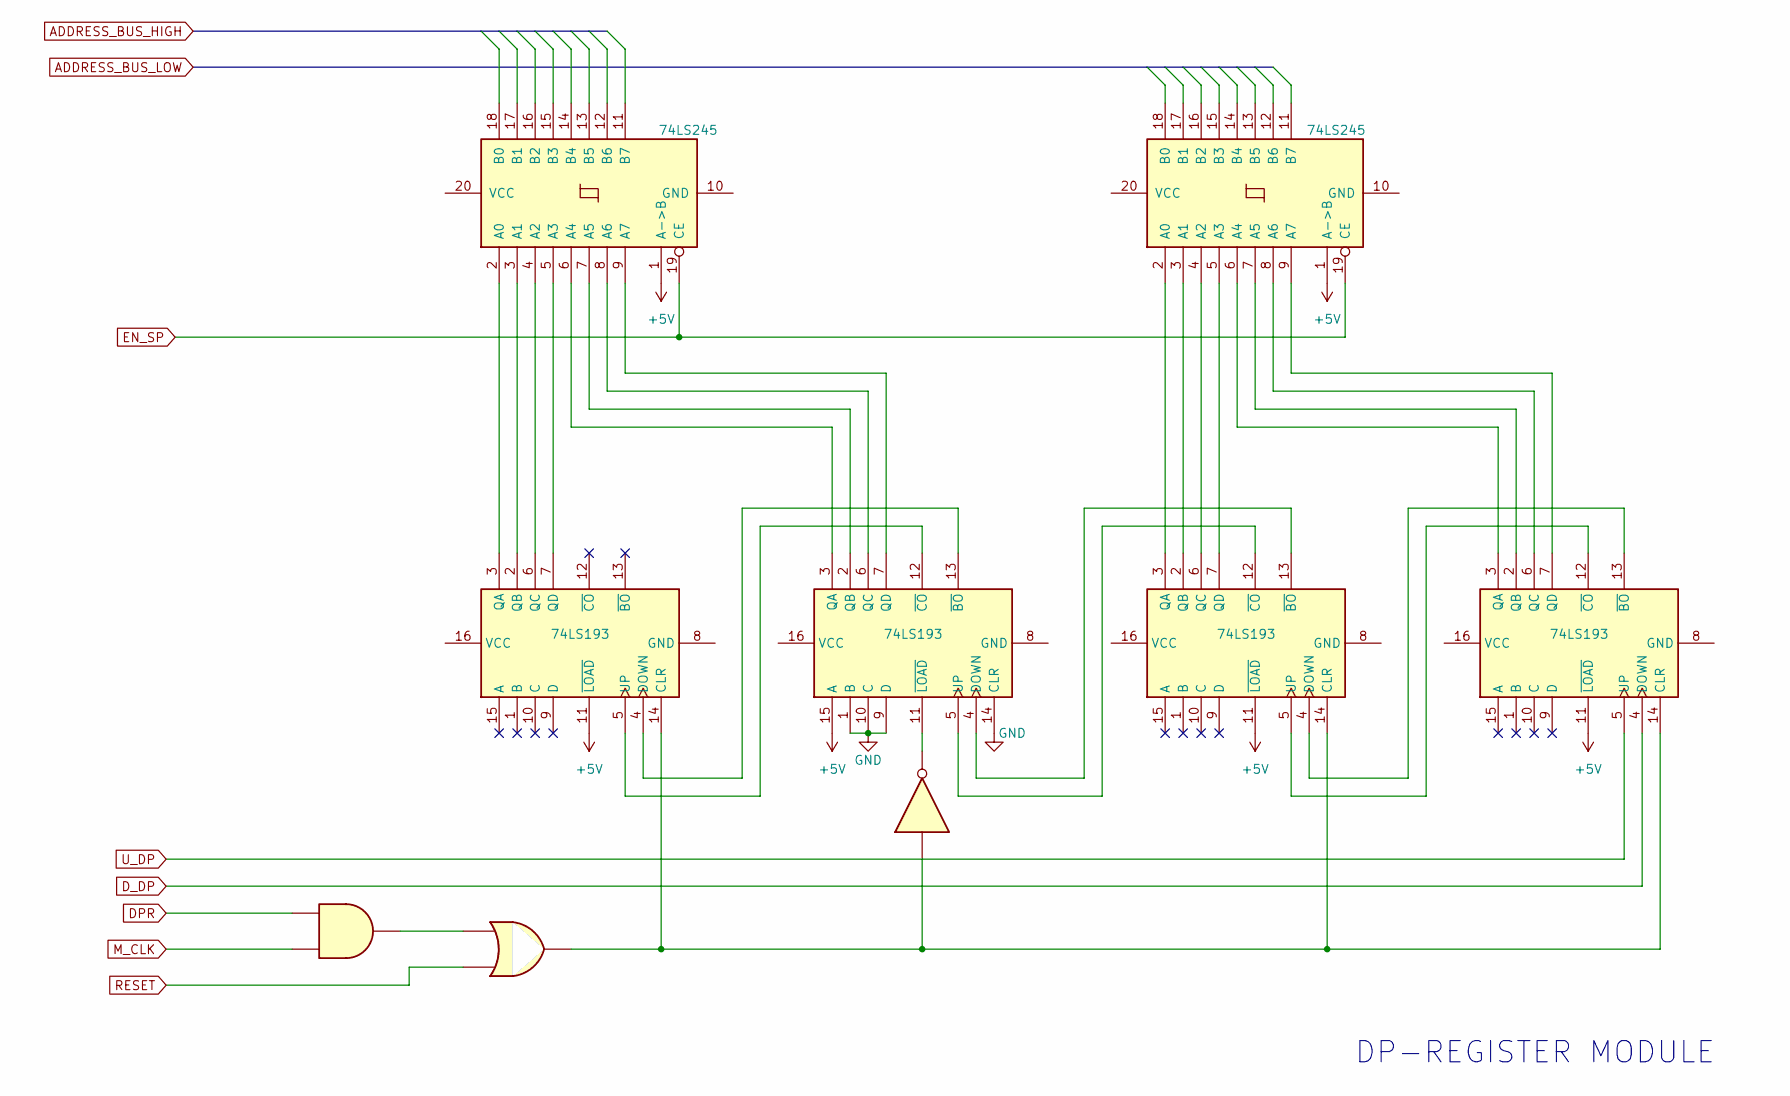
[picture p182: schematic data_pointer_register.kicad_sch]

Parts:
U1, U2, U5, U6: 74LS193
U3, U9: 74LS245
U4: 74LS04
U7: 74LS32
U8: 74LS08

Connections:
+5V: U1.11 (~LOAD), U2.11 (~LOAD), U3.1 (A->B), U5.15 (A), U6.11 (~LOAD), U9.1 (A->B)
DPR: U8.1
D_DP: U6.4 (DOWN)
EN_SP: U3.19 (CE), U9.19 (CE)
GND: U5.1 (B), U5.9 (D), U5.10 (C), U5.14 (CLR)
M_CLK: U8.2
unnamed: U1.2 (QB), U3.3 (A1)
unnamed: U1.3 (QA), U3.2 (A0)
unnamed: U1.4 (DOWN), U5.13 (~BO)
unnamed: U1.5 (UP), U5.12 (~CO)
unnamed: U1.6 (QC), U3.4 (A2)
unnamed: U1.7 (QD), U3.5 (A3)
unnamed: U1.14 (CLR), U2.14 (CLR), U4.1, U6.14 (CLR), U7.3
unnamed: U2.2 (QB), U9.3 (A1)
unnamed: U2.3 (QA), U9.2 (A0)
unnamed: U2.4 (DOWN), U6.13 (~BO)
unnamed: U2.5 (UP), U6.12 (~CO)
unnamed: U2.6 (QC), U9.4 (A2)
unnamed: U2.7 (QD), U9.5 (A3)
unnamed: U2.12 (~CO), U5.5 (UP)
unnamed: U2.13 (~BO), U5.4 (DOWN)
unnamed: U3.6 (A4), U5.3 (QA)
unnamed: U3.7 (A5), U5.2 (QB)
unnamed: U3.8 (A6), U5.6 (QC)
unnamed: U3.9 (A7), U5.7 (QD)
unnamed: U4.2, U5.11 (~LOAD)
unnamed: U6.2 (QB), U9.7 (A5)
unnamed: U6.3 (QA), U9.6 (A4)
unnamed: U6.6 (QC), U9.8 (A6)
unnamed: U6.7 (QD), U9.9 (A7)
unnamed: U7.1, U8.3
RESET: U7.2
U_DP: U6.5 (UP)

Notes on the sheet:
DP-REGISTER MODULE
