jorenheit/bfcpu/doc/circuits/data_register.kicad_sch

## KiCad design doc/circuits/data_register.kicad_sch (2025-10-24)

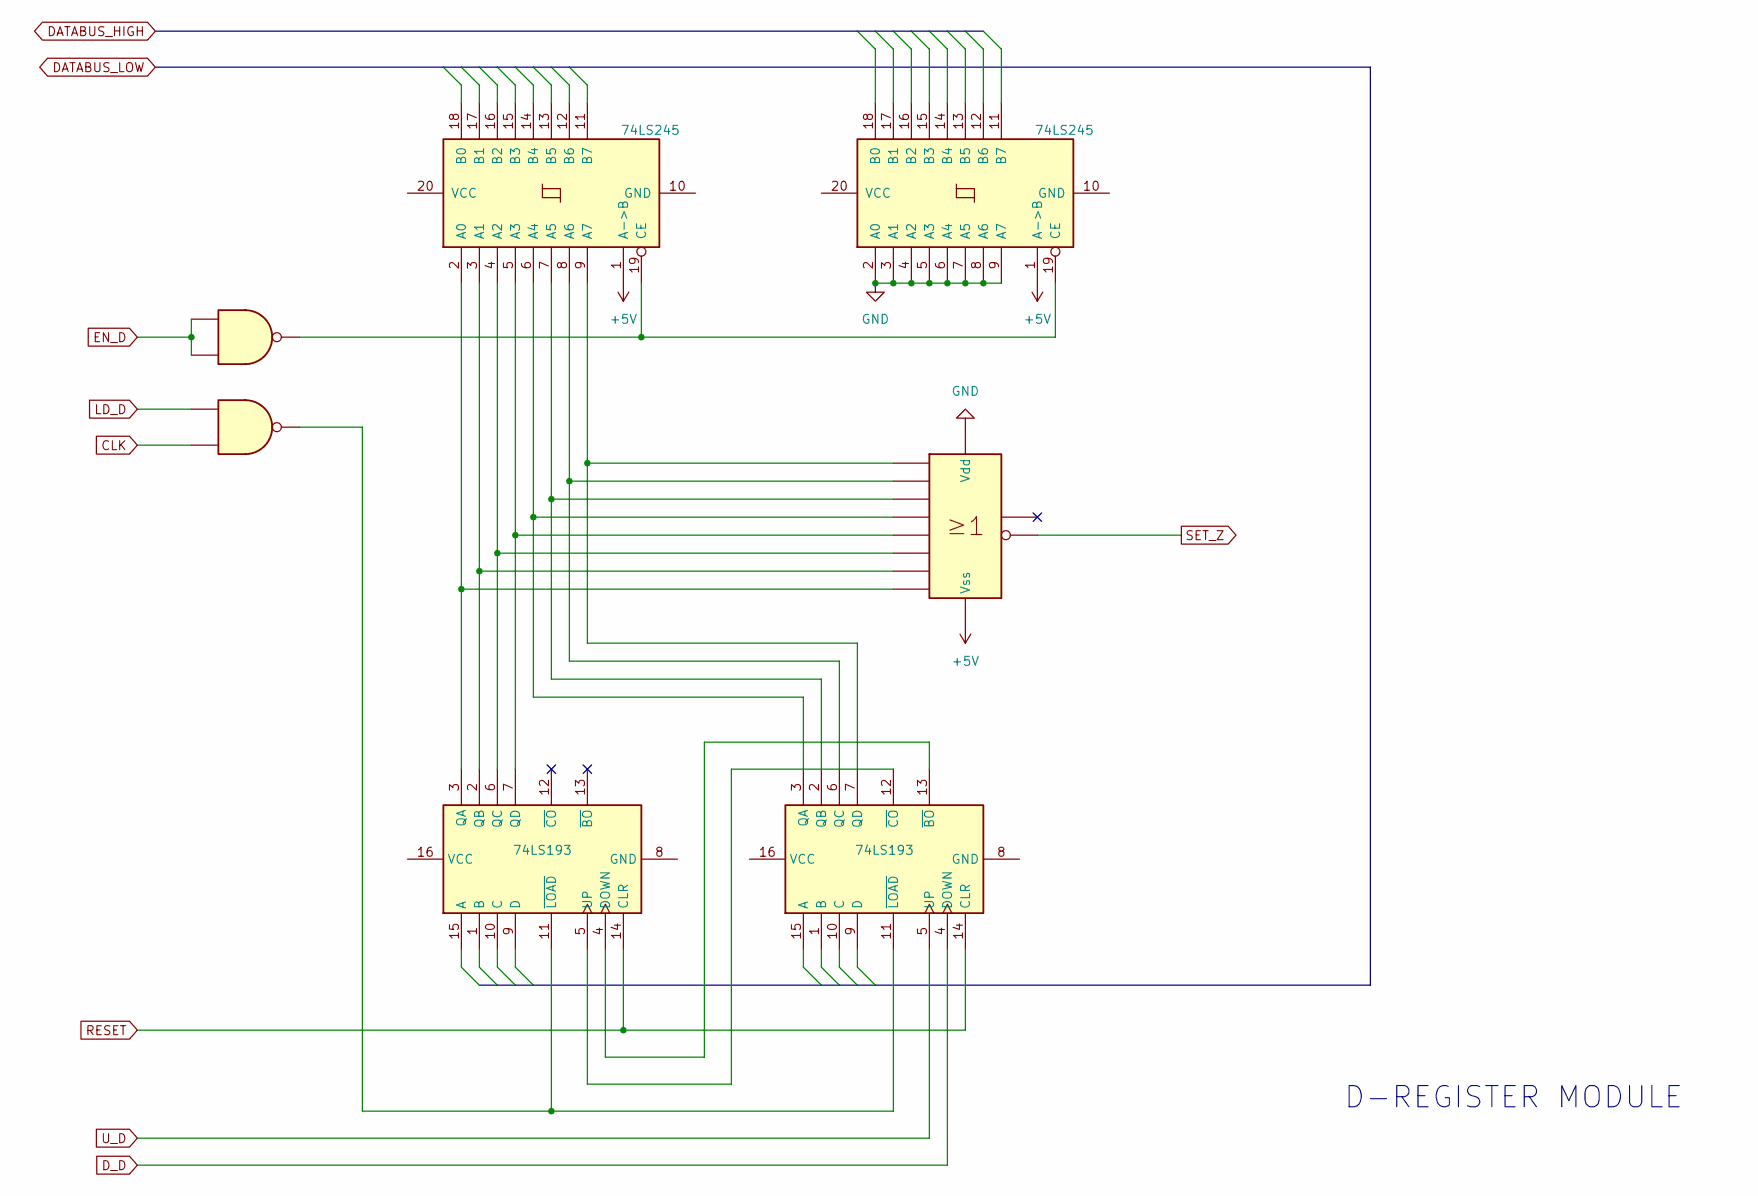
[picture p183: schematic data_register.kicad_sch]

Parts:
U1, U13: 74LS193
U2, U5: 74LS00
U3, U7: 74LS245
U12: 4078

Connections:
+5V: U3.1 (A->B), U7.1 (A->B), U12.7 (Vss)
CLK: U5.2
D_D: U13.4 (DOWN)
EN_D: U2.1, U2.2
GND: U7.2 (A0), U7.3 (A1), U7.4 (A2), U7.5 (A3), U7.6 (A4), U7.7 (A5), U7.8 (A6), U7.9 (A7), U12.14 (Vdd)
LD_D: U5.1
unnamed: U1.2 (QB), U3.3 (A1), U12.11
unnamed: U1.3 (QA), U3.2 (A0), U12.12
unnamed: U1.4 (DOWN), U13.13 (~BO)
unnamed: U1.5 (UP), U13.12 (~CO)
unnamed: U1.6 (QC), U3.4 (A2), U12.10
unnamed: U1.7 (QD), U3.5 (A3), U12.9
unnamed: U1.11 (~LOAD), U5.3, U13.11 (~LOAD)
unnamed: U2.3, U3.19 (CE), U7.19 (CE)
unnamed: U3.9 (A7), U12.2, U13.7 (QD)
unnamed: U3.8 (A6), U12.3, U13.6 (QC)
unnamed: U3.7 (A5), U12.4, U13.2 (QB)
unnamed: U3.6 (A4), U12.5, U13.3 (QA)
RESET: U1.14 (CLR), U13.14 (CLR)
SET_Z: U12.13
U_D: U13.5 (UP)

Notes on the sheet:
D-REGISTER MODULE
