jorenheit/bfcpu/doc/circuits/eeprom_programmer.kicad_sch

## KiCad design doc/circuits/eeprom_programmer.kicad_sch (2025-01-12)

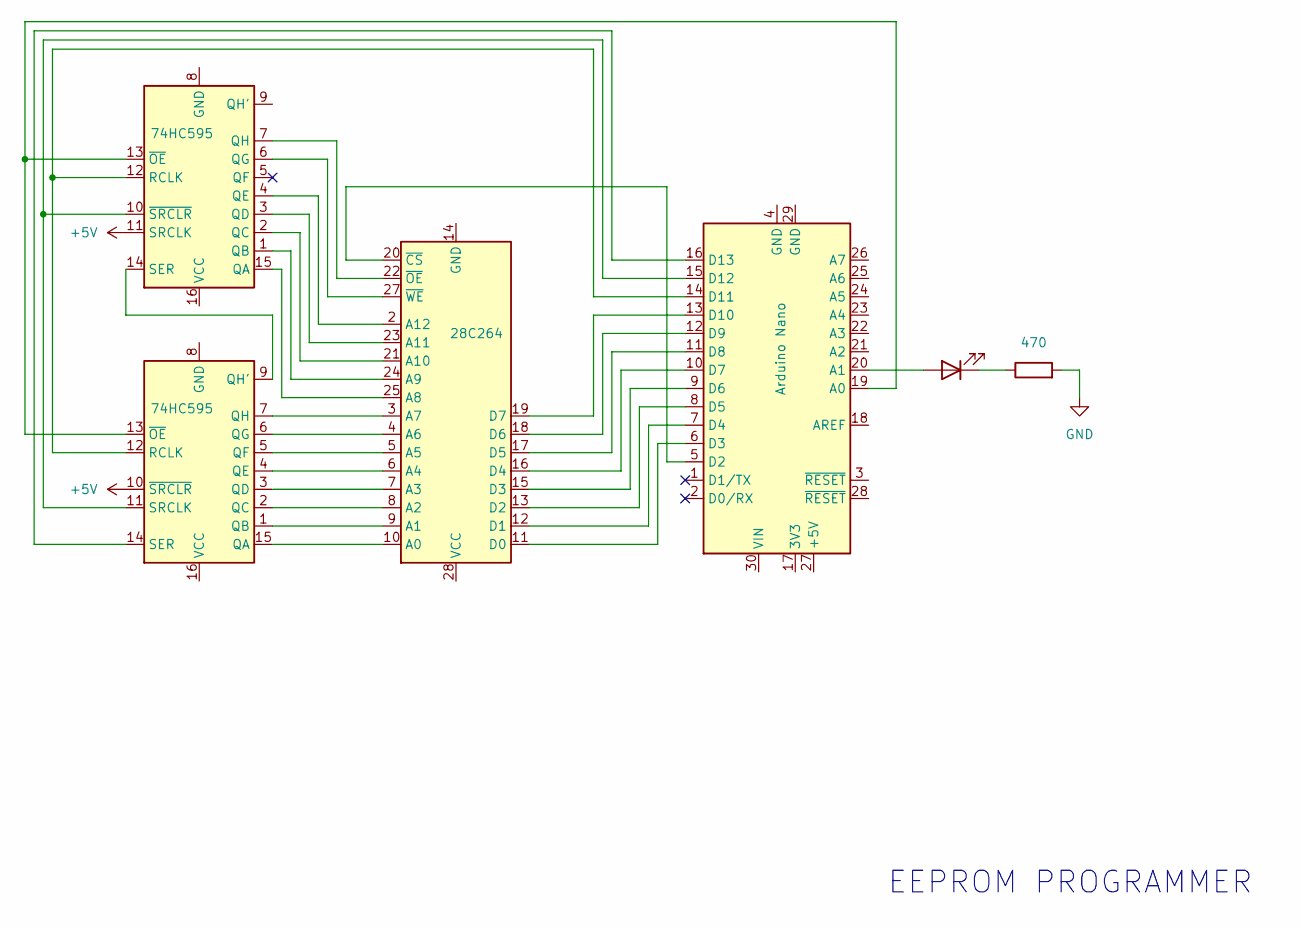
[picture p184: schematic eeprom_programmer.kicad_sch]

Parts:
A1: Arduino Nano; Arduino_Nano
D1: LED
R1: 470
U1, U2: 74HC595

Connections:
+5V: U1.11 (SRCLK), U2.10 (~SRCLR)
GND: R1.2
unnamed: A1.14 (D11), U1.12 (RCLK), U2.12 (RCLK)
unnamed: A1.15 (D12), U1.10 (~SRCLR), U2.11 (SRCLK)
unnamed: A1.16 (D13), U2.14 (SER)
unnamed: A1.19 (A0), U1.13 (~OE), U2.13 (~OE)
unnamed: A1.20 (A1), D1.2 (A)
unnamed: D1.1 (K), R1.1
unnamed: U1.14 (SER), U2.9 (QH')

Notes on the sheet:
EEPROM PROGRAMMER
