jorenheit/bfcpu/doc/circuits/instruction_pointer_register.kicad_sch

## KiCad design doc/circuits/instruction_pointer_register.kicad_sch (2025-01-12)

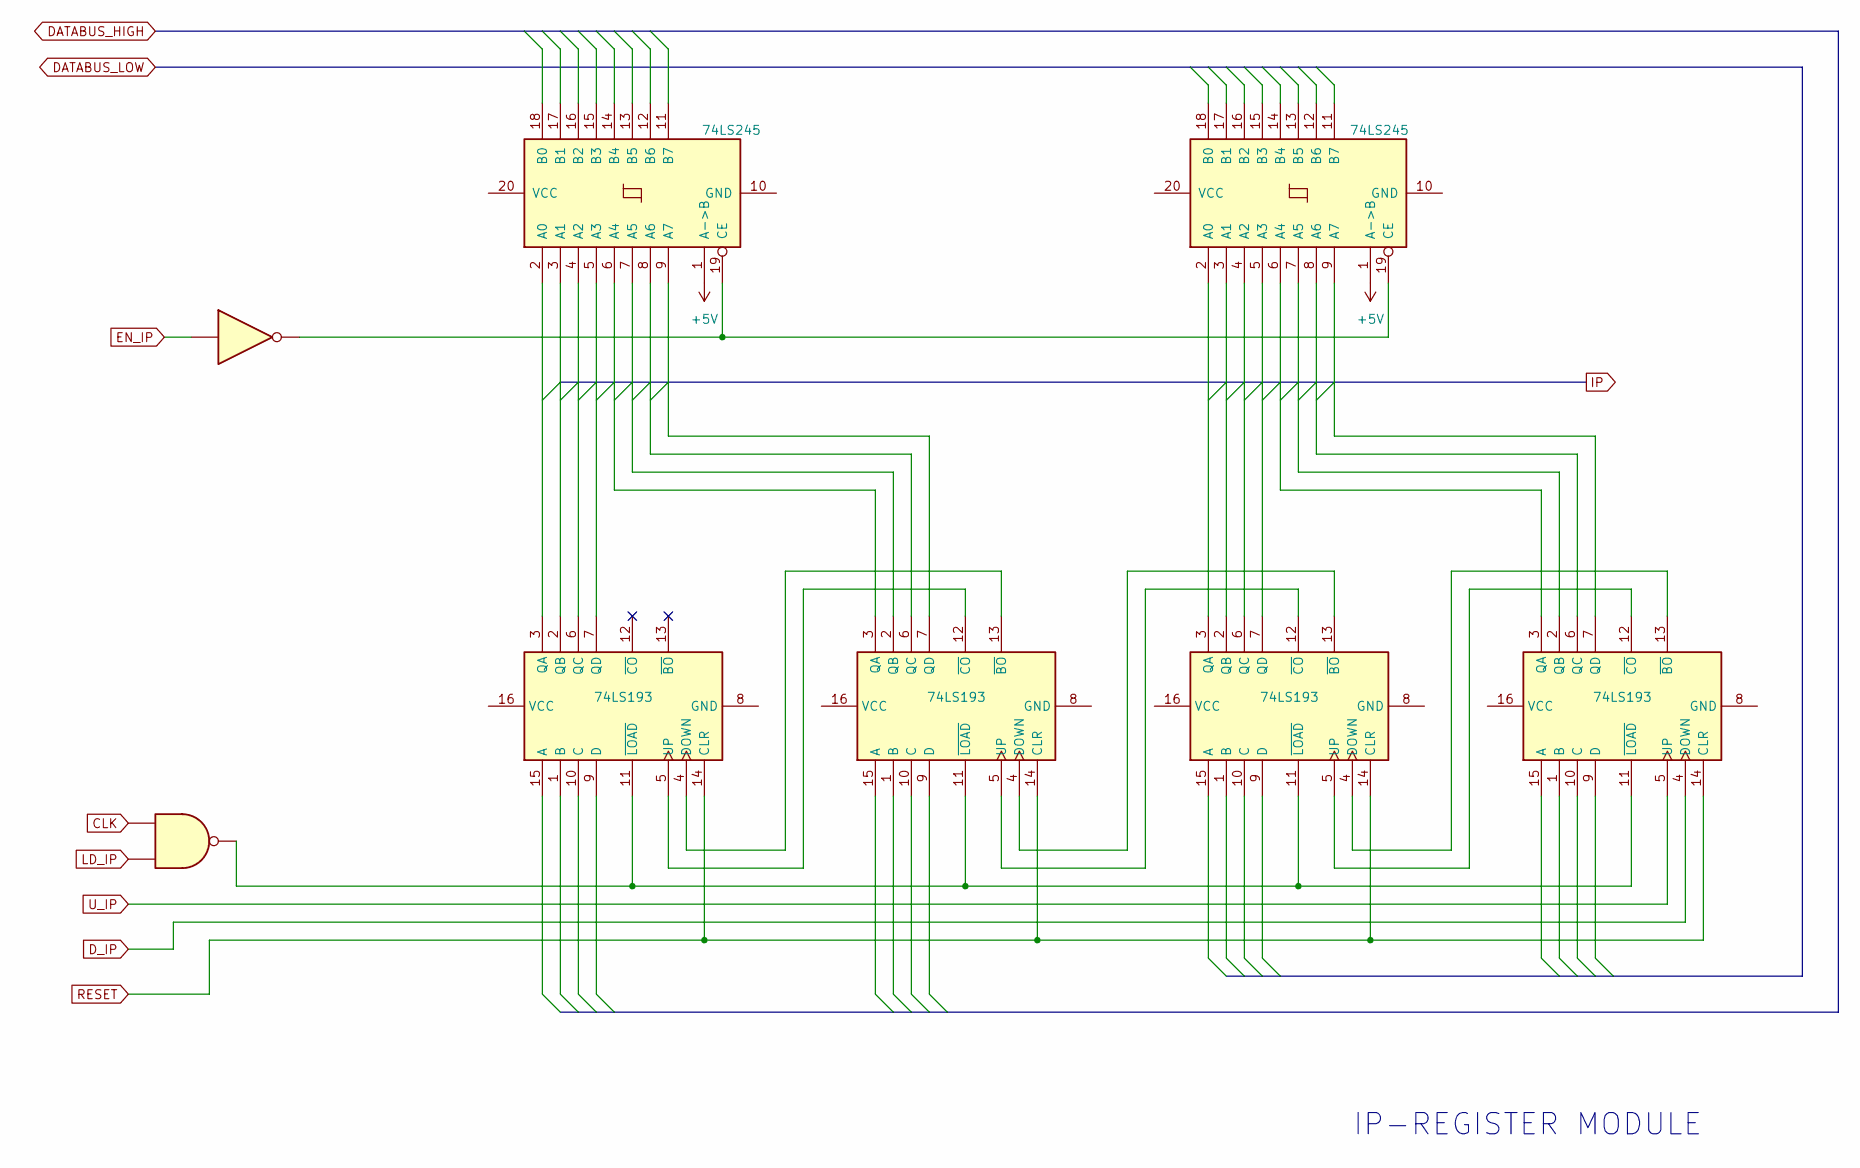
[picture p185: schematic instruction_pointer_register.kicad_sch]

Parts:
U1: 74LS00
U6: 74LS04
U7, U12, U13, U15: 74LS193
U11, U14: 74LS245

Connections:
+5V: U11.1 (A->B), U14.1 (A->B)
CLK: U1.1
D_IP: U15.4 (DOWN)
EN_IP: U6.1
LD_IP: U1.2
unnamed: U1.3, U7.11 (~LOAD), U12.11 (~LOAD), U13.11 (~LOAD), U15.11 (~LOAD)
unnamed: U7.3 (QA), U11.2 (A0)
unnamed: U7.2 (QB), U11.3 (A1)
unnamed: U7.6 (QC), U11.4 (A2)
unnamed: U7.7 (QD), U11.5 (A3)
unnamed: U11.6 (A4), U12.3 (QA)
unnamed: U11.7 (A5), U12.2 (QB)
unnamed: U11.8 (A6), U12.6 (QC)
unnamed: U11.9 (A7), U12.7 (QD)
unnamed: U6.2, U11.19 (CE), U14.19 (CE)
unnamed: U12.4 (DOWN), U13.13 (~BO)
unnamed: U12.5 (UP), U13.12 (~CO)
unnamed: U7.5 (UP), U12.12 (~CO)
unnamed: U7.4 (DOWN), U12.13 (~BO)
unnamed: U13.2 (QB), U14.3 (A1)
unnamed: U13.3 (QA), U14.2 (A0)
unnamed: U13.4 (DOWN), U15.13 (~BO)
unnamed: U13.5 (UP), U15.12 (~CO)
unnamed: U13.6 (QC), U14.4 (A2)
unnamed: U13.7 (QD), U14.5 (A3)
unnamed: U14.6 (A4), U15.3 (QA)
unnamed: U14.7 (A5), U15.2 (QB)
unnamed: U14.8 (A6), U15.6 (QC)
unnamed: U14.9 (A7), U15.7 (QD)
RESET: U7.14 (CLR), U12.14 (CLR), U13.14 (CLR), U15.14 (CLR)
U_IP: U15.5 (UP)

Notes on the sheet:
IP-REGISTER MODULE
