jorenheit/bfcpu/doc/circuits/io_module.kicad_sch

## KiCad design doc/circuits/io_module.kicad_sch (2025-12-01)

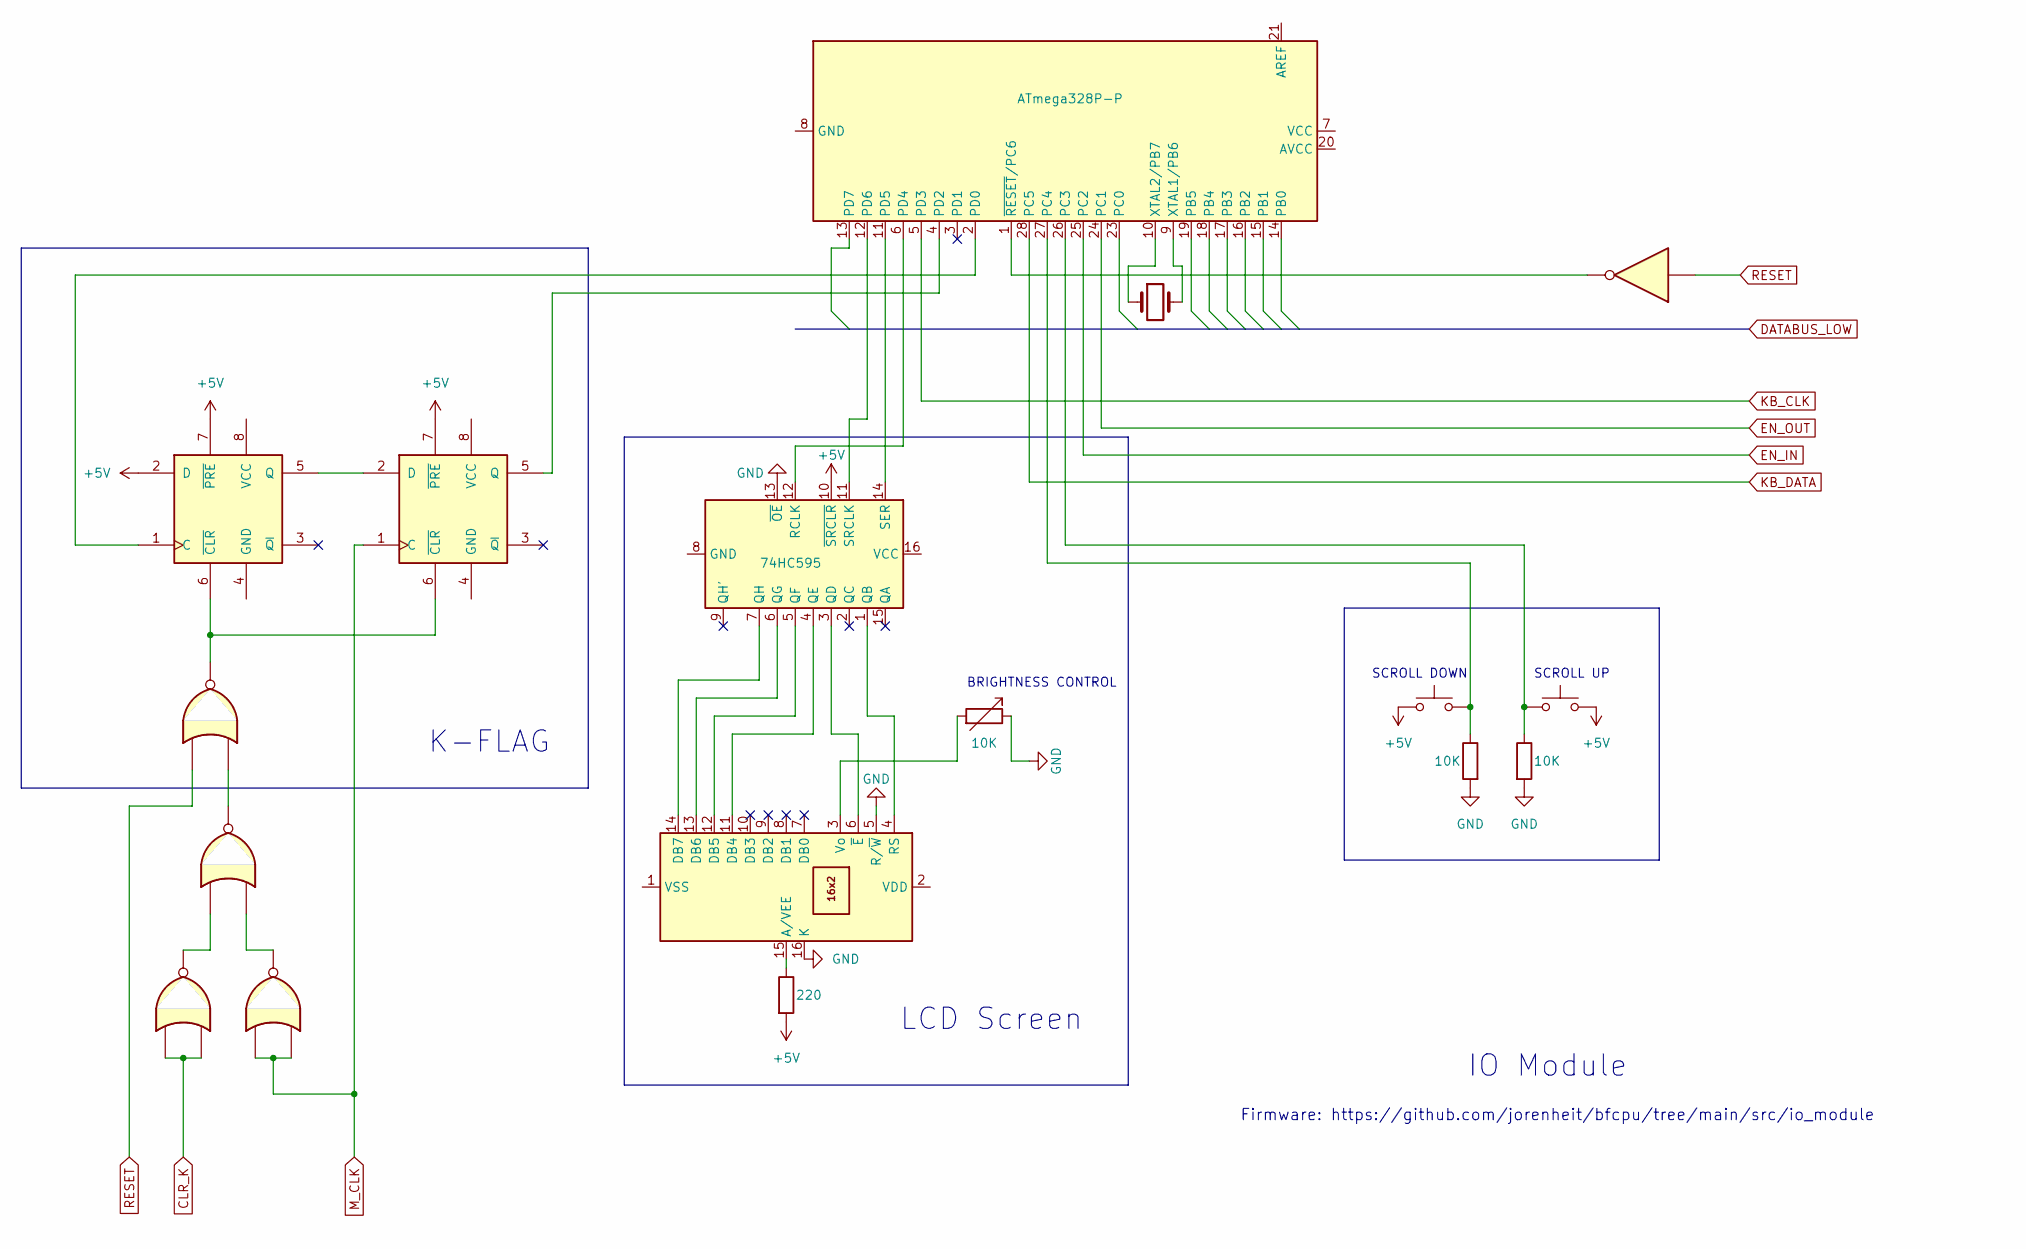
[picture p186: schematic io_module.kicad_sch]

Parts:
R1, R2, R3: 10K
R4: 220
SW1, SW3: SW_MEC_5G
U1: RC1602A-GHW-ESX; RC1602A
U2: 74LS04
U3: 74HC595
U4: ATmega328P-P; DIP-28_W7.62mm
U5, U6: 74AUC1G74
U8, U9, U10, U11: 74LS02
Y1: Crystal

Connections:
+5V: R4.2, SW1.3 (B), SW1.4 (B), SW3.3 (B), SW3.4 (B), U3.10 (~SRCLR), U5.2 (D), U5.7 (~PRE), U6.7 (~PRE)
CLR_K: U9.2, U9.3
EN_IN: U4.25 (PC2)
EN_OUT: U4.24 (PC1)
GND: R1.2, R2.2, R3.1, U1.5 (R/~W), U1.16 (K), U3.13 (~OE)
KB_CLK: U4.5 (PD3)
KB_DATA: U4.28 (PC5)
M_CLK: U6.1 (C), U8.2, U8.3
unnamed: R1.1, SW1.1 (A), SW1.2 (A), U4.27 (PC4)
unnamed: R2.1, SW3.1 (A), SW3.2 (A), U4.26 (PC3)
unnamed: R3.2, U1.3 (Vo)
unnamed: R4.1, U1.15 (A/VEE)
unnamed: U1.4 (RS), U3.1 (QB)
unnamed: U1.6 (~E), U3.3 (QD)
unnamed: U1.11 (DB4), U3.4 (QE)
unnamed: U1.12 (DB5), U3.5 (QF)
unnamed: U1.13 (DB6), U3.6 (QG)
unnamed: U1.14 (DB7), U3.7 (QH)
unnamed: U2.2, U4.1 (~RESET/PC6)
unnamed: U3.11 (SRCLK), U4.12 (PD6)
unnamed: U3.12 (RCLK), U4.6 (PD4)
unnamed: U3.14 (SER), U4.11 (PD5)
unnamed: U4.2 (PD0), U5.1 (C)
unnamed: U4.4 (PD2), U6.5 (Q)
unnamed: U4.9 (XTAL1/PB6), Y1.2
unnamed: U4.10 (XTAL2/PB7), Y1.1
unnamed: U4.8 (GND), U4.22 (GND)
unnamed: U5.5 (Q), U6.2 (D)
unnamed: U10.1, U11.3
unnamed: U9.1, U10.2
unnamed: U8.1, U10.3
unnamed: U5.6 (~CLR), U6.6 (~CLR), U11.1
RESET: U2.1, U11.2

Notes on the sheet:
IO Module
BRIGHTNESS CONTROL
SCROLL DOWN
LCD Screen
SCROLL UP
Firmware: https://github.com/jorenheit/bfcpu/tree/main/src/io_module
K-FLAG
