jorenheit/bfcpu/doc/circuits/loop_skip_register.kicad_sch

## KiCad design doc/circuits/loop_skip_register.kicad_sch (2025-10-24)

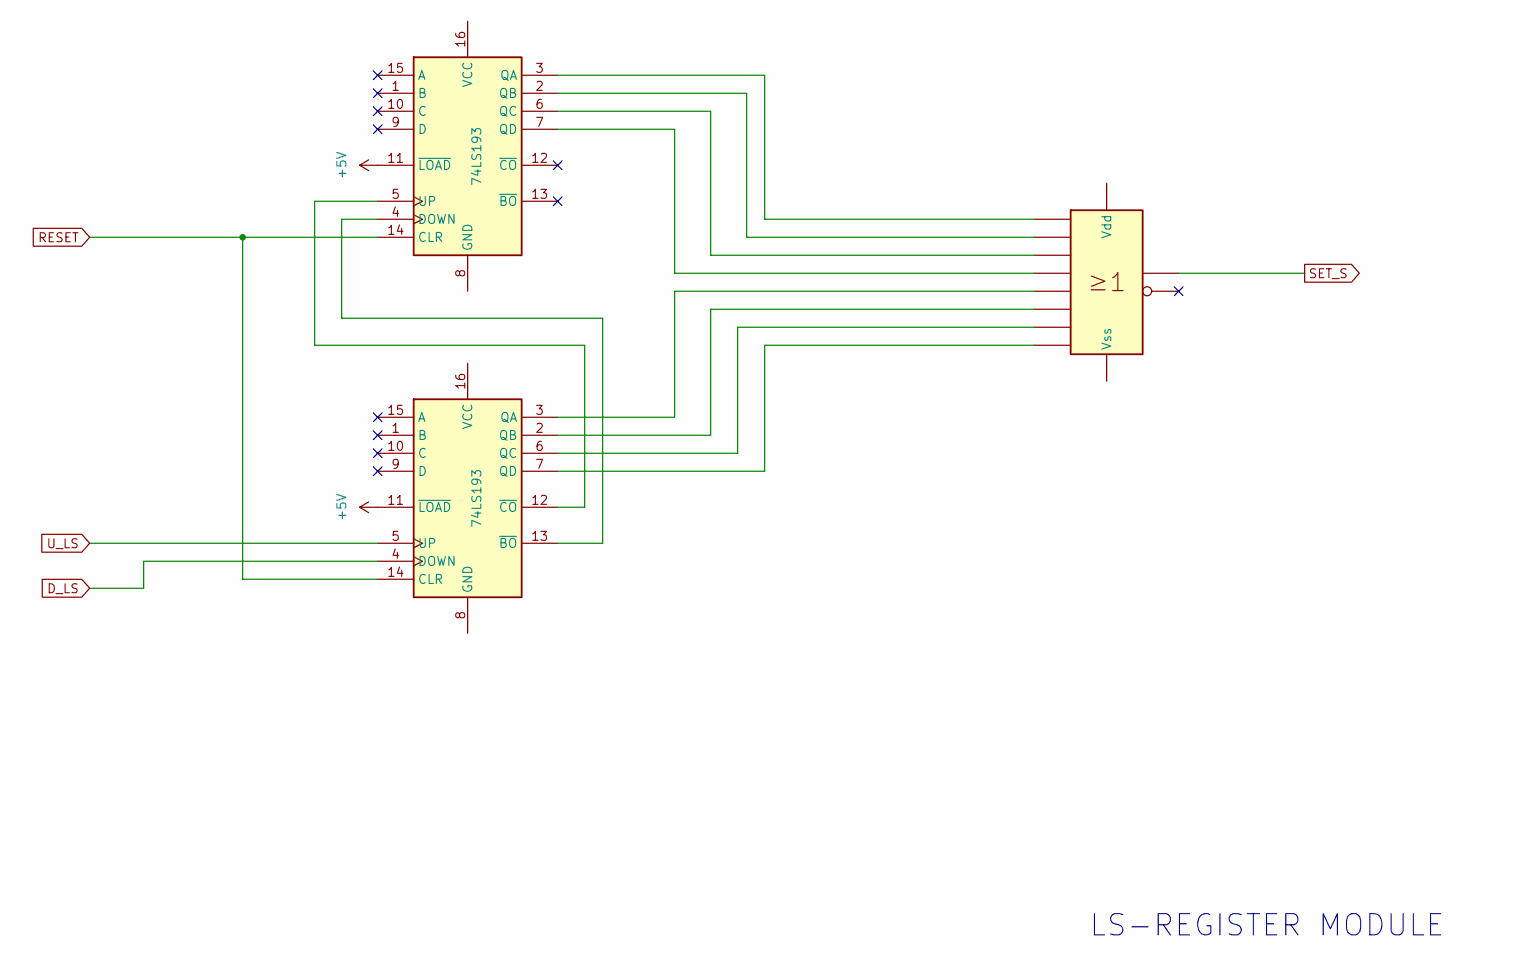
[picture p187: schematic loop_skip_register.kicad_sch]

Parts:
U1, U13: 74LS193
U2: 4078

Connections:
+5V: U1.11 (~LOAD), U13.11 (~LOAD)
D_LS: U13.4 (DOWN)
unnamed: U1.2 (QB), U2.3
unnamed: U1.3 (QA), U2.2
unnamed: U1.4 (DOWN), U13.13 (~BO)
unnamed: U1.5 (UP), U13.12 (~CO)
unnamed: U1.6 (QC), U2.4
unnamed: U1.7 (QD), U2.5
unnamed: U2.10, U13.2 (QB)
unnamed: U2.9, U13.3 (QA)
unnamed: U2.11, U13.6 (QC)
unnamed: U2.12, U13.7 (QD)
RESET: U1.14 (CLR), U13.14 (CLR)
SET_S: U2.1
U_LS: U13.5 (UP)

Notes on the sheet:
LS-REGISTER MODULE
