jorenheit/bfcpu/doc/circuits/master_clock.kicad_sch

## KiCad design doc/circuits/master_clock.kicad_sch (2025-11-19)

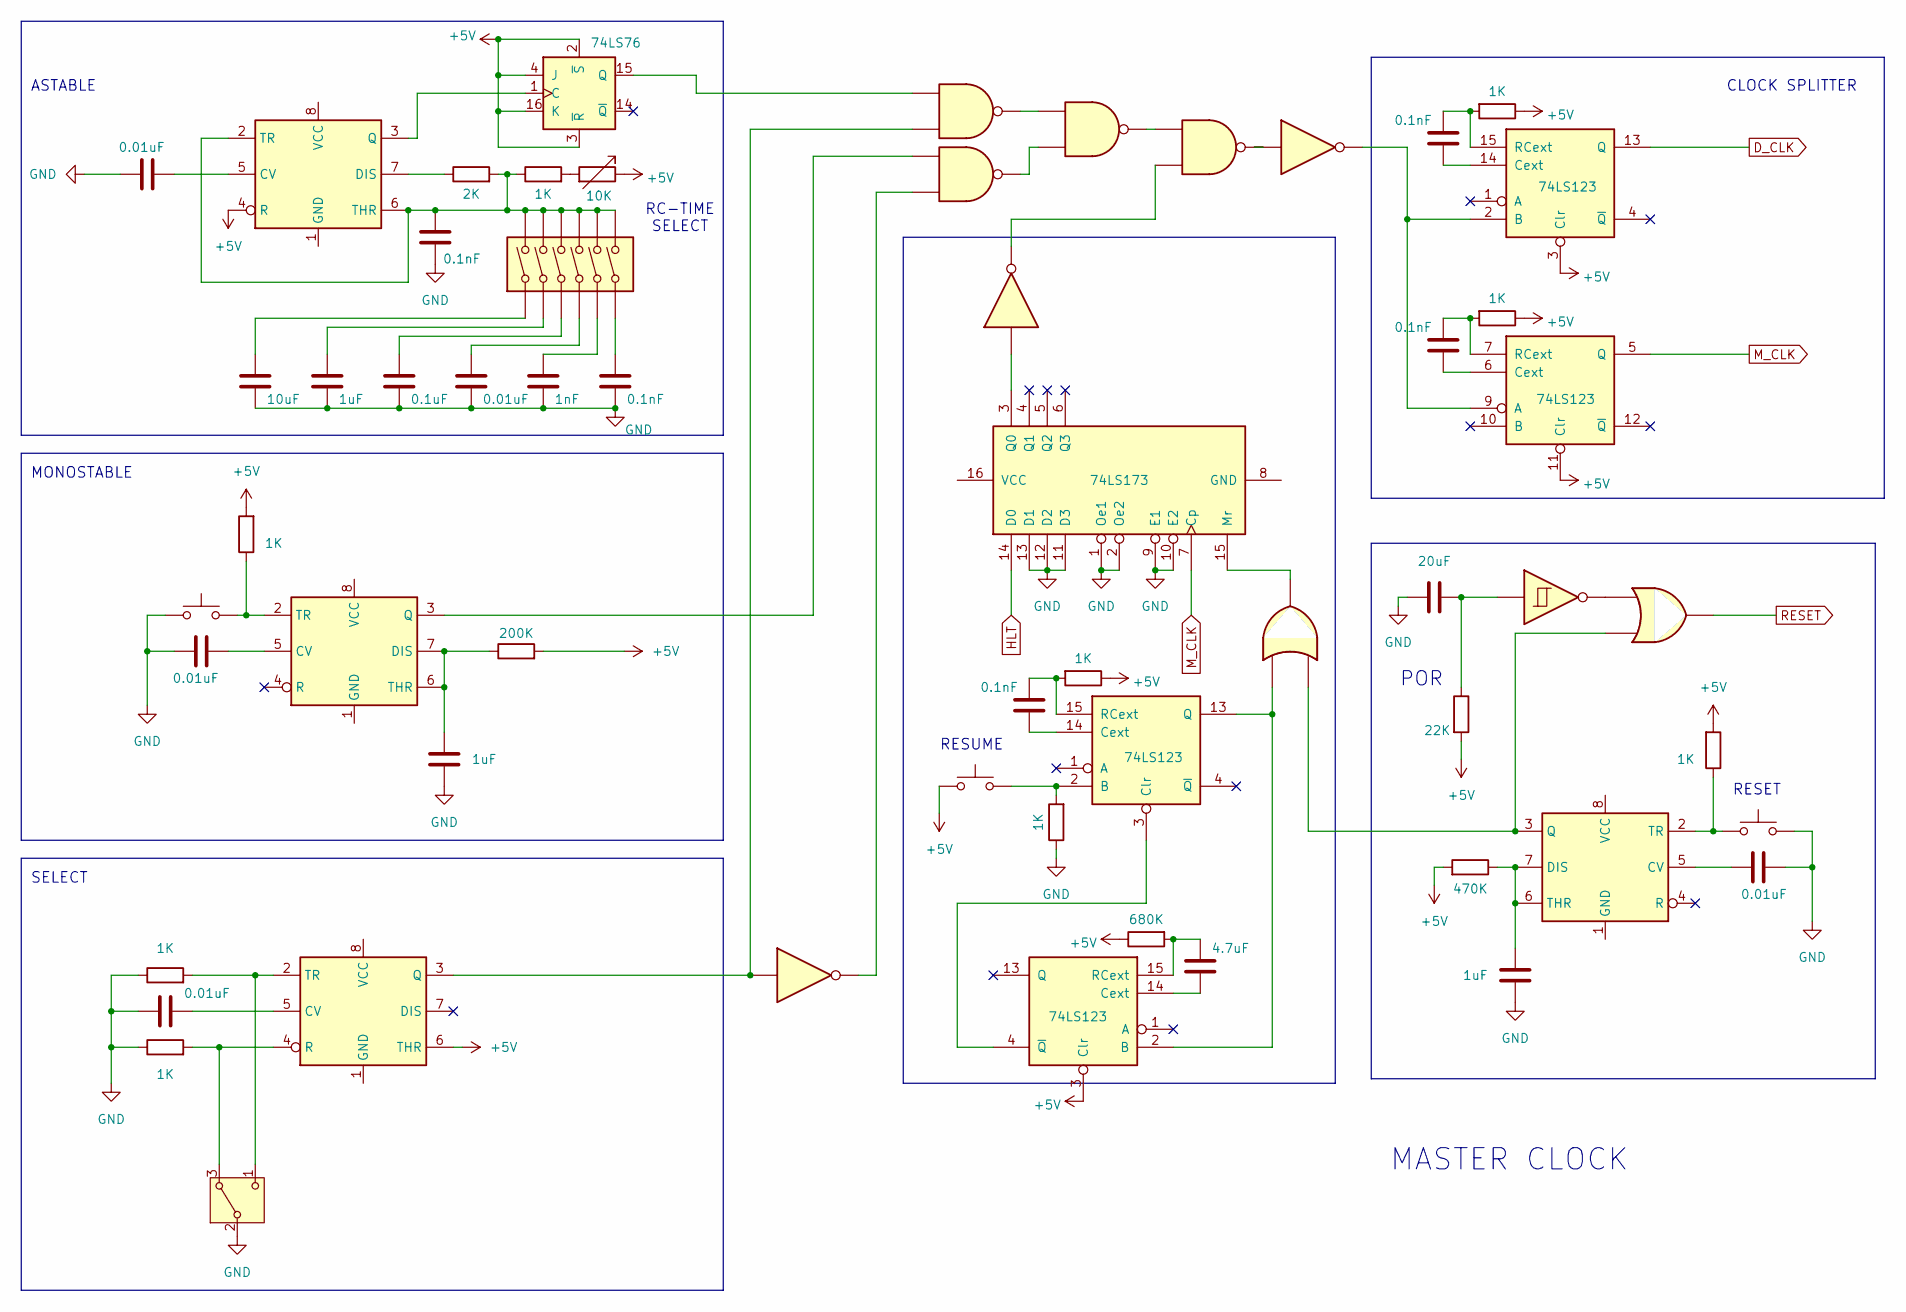
[picture p188: schematic master_clock.kicad_sch]

Parts:
C1, C12, C14, C15, C16: 0.1nF
C2, C4, C5, C6, C10: 0.01uF
C3, C7, C8: 1uF
C9: 0.1uF
C11: 1nF
C13: 10uF
C17: 4.7uF
C18: 20uF
R1, R2, R3, R6, R7, R8: 1K
R4: 2K
R5: 10K
R9: 680K
R10: 22K
RA1, RA3, RA5: 1K
RA2: 200K
RA4: 470K
SW1, SW4, SW5: SW_MEC_5G
SW2: SW_Nidec_CAS-120A1; Nidec_Copal_CAS-120A
SW3: SW_DIP_x06
U1, U2, U3, U13: LM555xM; SOIC-8_3.9x4.9mm_P1.27mm
U4, U9, U14: 74LS04
U5, U6, U7, U8: 74LS00
U10, U15, U16: 74LS123
U11: 74LS173
U12, U18: 74LS32
U17: 74LS76
U19: 74LS14

Connections:
+5V: R5.1, R6.1, R7.1, R8.1, R9.1, R10.2, RA1.2, RA2.2, RA3.2, RA4.2, SW5.3 (B), SW5.4 (B), U1.4 (R), U3.6 (THR), U10.3 (Clr), U10.11 (Clr), U16.3 (Clr), U17.2 (~S), U17.3 (~R), U17.4 (J), U17.16 (K)
D_CLK: U10.13 (Q)
GND: C1.2, C2.1, C3.2, C4.1, C5.2, C6.1, C7.2, C8.2, C9.2, C10.2, C11.2, C12.2, C13.2, C18.1, R1.1, R2.1, RA5.1, SW1.1 (A), SW1.2 (A), SW2.2 (B), SW4.1 (A), SW4.2 (A), U11.1 (Oe1), U11.2 (Oe2), U11.9 (E1), U11.10 (E2), U11.11 (D3), U11.12 (D2), U11.13 (D1)
HLT: U11.14 (D0)
M_CLK: U10.5 (Q), U11.7 (Cp)
unnamed: C1.1, R3.1, R4.2, SW3.7, SW3.8, SW3.9, SW3.10, SW3.11, SW3.12, U1.2 (TR), U1.6 (THR)
unnamed: C2.2, U1.5 (CV)
unnamed: C3.1, RA2.1, U2.6 (THR), U2.7 (DIS)
unnamed: C4.2, U2.5 (CV)
unnamed: C5.1, U3.5 (CV)
unnamed: C6.2, U13.5 (CV)
unnamed: C7.1, RA4.1, U13.6 (THR), U13.7 (DIS)
unnamed: C8.1, SW3.2
unnamed: C9.1, SW3.3
unnamed: C10.1, SW3.4
unnamed: C11.1, SW3.5
unnamed: C12.1, SW3.6
unnamed: C13.1, SW3.1
unnamed: C14.1, U10.14 (Cext)
unnamed: C14.2, R6.2, U10.15 (RCext)
unnamed: C15.1, U10.6 (Cext)
unnamed: C15.2, R7.2, U10.7 (RCext)
unnamed: C16.1, U15.14 (Cext)
unnamed: C16.2, R8.2, U15.15 (RCext)
unnamed: C17.1, U16.14 (Cext)
unnamed: C17.2, R9.2, U16.15 (RCext)
unnamed: C18.2, R10.1, U19.1
unnamed: R1.2, SW2.1 (C), U3.2 (TR)
unnamed: R2.2, SW2.3 (A), U3.4 (R)
unnamed: R3.2, R5.2
unnamed: R4.1, U1.7 (DIS)
unnamed: RA1.1, SW1.3 (B), SW1.4 (B), U2.2 (TR)
unnamed: RA3.1, SW4.3 (B), SW4.4 (B), U13.2 (TR)
unnamed: RA5.2, SW5.1 (A), SW5.2 (A), U15.2 (B)
unnamed: U1.3 (Q), U17.1 (C)
unnamed: U2.3 (Q), U5.1
unnamed: U4.1, U8.3
unnamed: U5.3, U7.2
unnamed: U6.3, U7.1
unnamed: U7.3, U8.1
unnamed: U8.2, U9.2
unnamed: U4.2, U10.2 (B), U10.9 (A)
unnamed: U9.1, U11.3 (Q0)
unnamed: U11.15 (Mr), U12.3
unnamed: U12.1, U15.13 (Q), U16.2 (B)
unnamed: U12.2, U13.3 (Q), U18.2
unnamed: U3.3 (Q), U6.2, U14.1
unnamed: U5.2, U14.2
unnamed: U15.3 (Clr), U16.4 (~Q)
unnamed: U6.1, U17.15 (Q)
unnamed: U18.1, U19.2
RESET: U18.3

Notes on the sheet:
RC-TIME SELECT
ASTABLE
MASTER CLOCK
MONOSTABLE
POR
CLOCK SPLITTER
RESUME
RESET
SELECT
