jorenheit/bfcpu/doc/circuits/ram.kicad_sch

## KiCad design doc/circuits/ram.kicad_sch (2025-03-10)

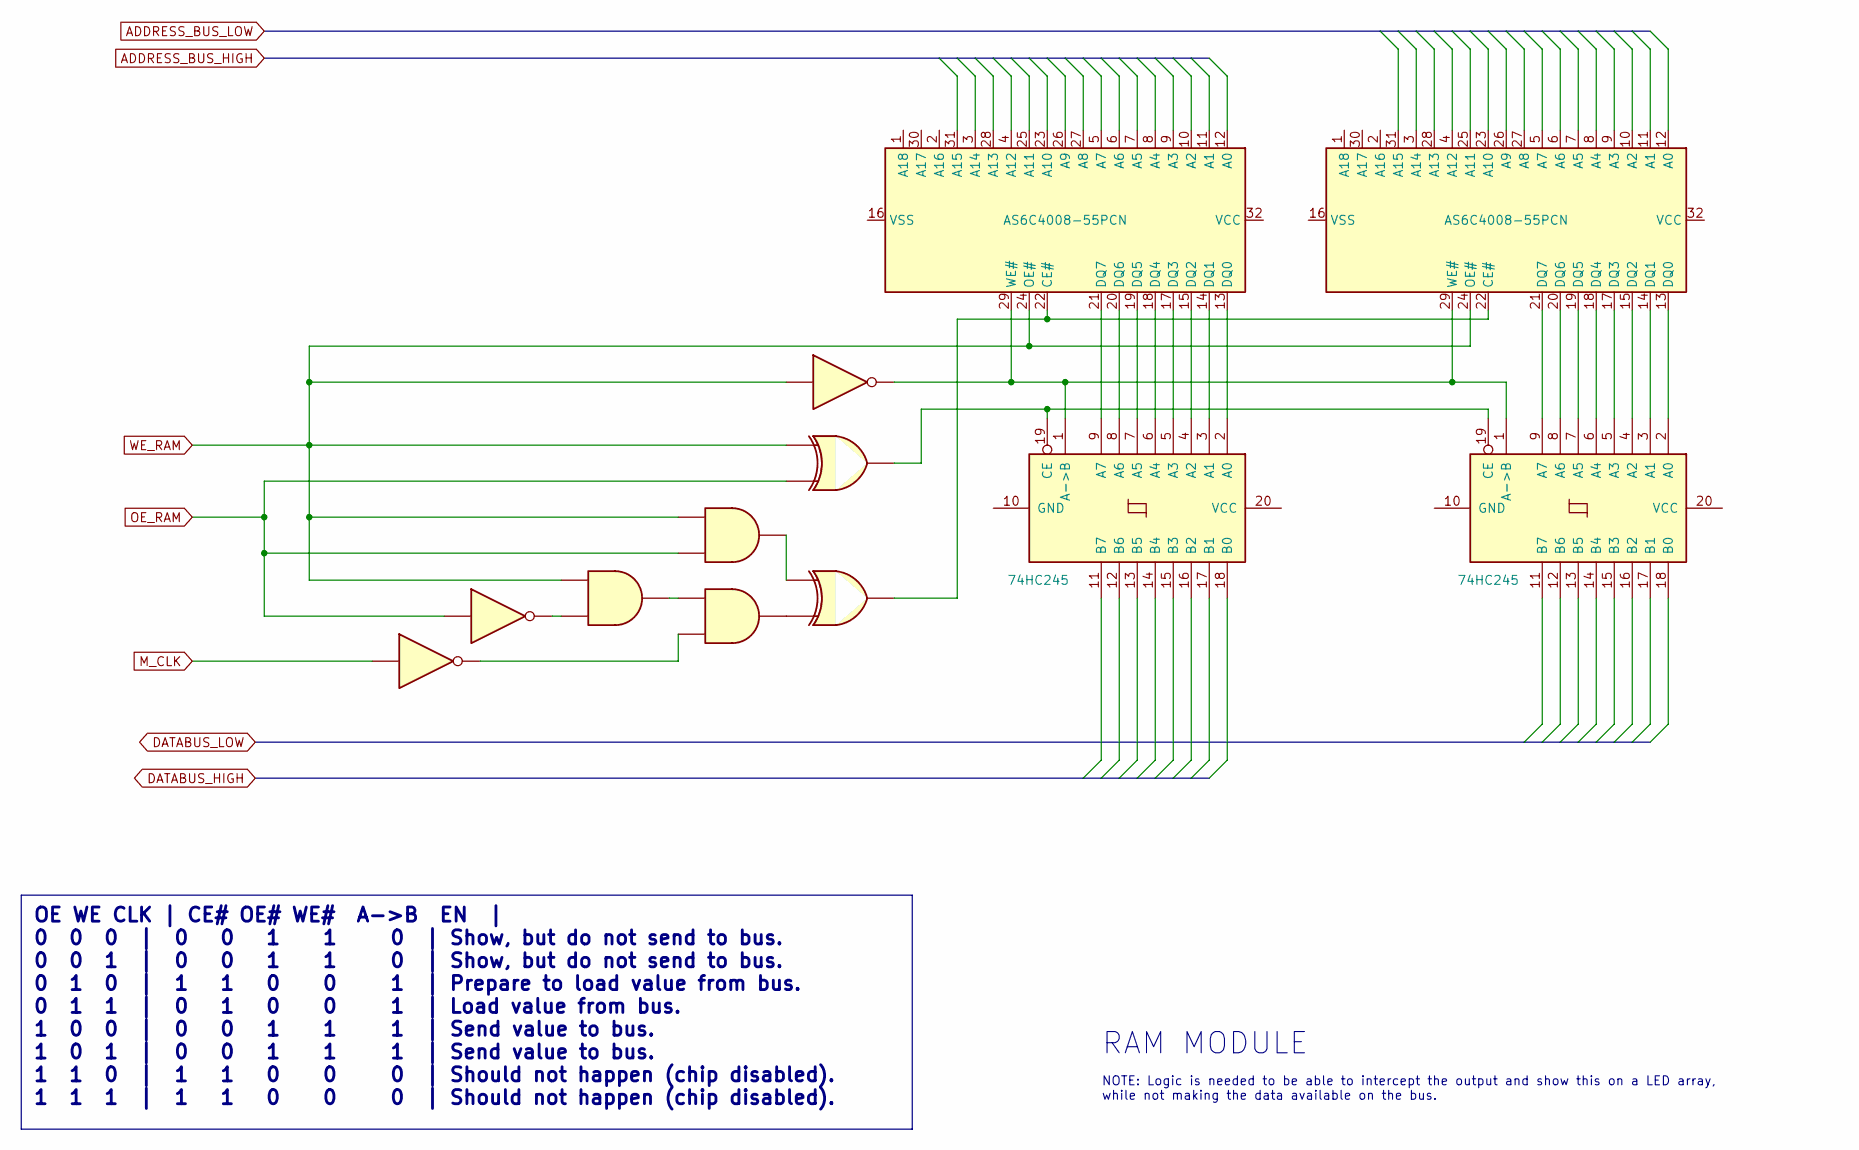
[picture p189: schematic ram.kicad_sch]

Parts:
U1, U2: AS6C4008-55PCN; DIP-32_W15.24mm
U3, U4: 74HC245
U5, U10, U12: 74LS04
U6, U7: 74HC86
U8, U9, U11: 74LS08

Connections:
M_CLK: U10.1
unnamed: U1.13 (DQ0), U4.2 (A0)
unnamed: U1.14 (DQ1), U4.3 (A1)
unnamed: U1.15 (DQ2), U4.4 (A2)
unnamed: U1.17 (DQ3), U4.5 (A3)
unnamed: U1.18 (DQ4), U4.6 (A4)
unnamed: U1.19 (DQ5), U4.7 (A5)
unnamed: U1.20 (DQ6), U4.8 (A6)
unnamed: U1.21 (DQ7), U4.9 (A7)
unnamed: U1.22 (CE#), U2.22 (CE#), U7.3
unnamed: U1.29 (WE#), U2.29 (WE#), U3.1 (A->B), U4.1 (A->B), U5.2
unnamed: U2.13 (DQ0), U3.2 (A0)
unnamed: U2.14 (DQ1), U3.3 (A1)
unnamed: U2.15 (DQ2), U3.4 (A2)
unnamed: U2.17 (DQ3), U3.5 (A3)
unnamed: U2.18 (DQ4), U3.6 (A4)
unnamed: U2.19 (DQ5), U3.7 (A5)
unnamed: U2.20 (DQ6), U3.8 (A6)
unnamed: U2.21 (DQ7), U3.9 (A7)
unnamed: U3.19 (CE), U4.19 (CE), U6.3
unnamed: U7.1, U8.3
unnamed: U7.2, U9.3
unnamed: U9.2, U10.2
unnamed: U11.2, U12.2
unnamed: U9.1, U11.3
OE_RAM: U6.2, U8.2, U12.1
WE_RAM: U1.24 (OE#), U2.24 (OE#), U5.1, U6.1, U8.1, U11.1

Notes on the sheet:
OE WE CLK | CE# OE# WE# A->B EN | 0 0 0 | 0 0 1 1 0 | Show, but do not send to bus. 0 0 1 | 0 0 1 1 0 | Show, but do not send to bus. 0 1 0 | 1 1 0 0 1 | Prepare to load value from bus. 0 1 1 | 0 1 0 0 1 | Load value from bus. 1 0 0 | 0 0 1 1 1 | Send value to bus. 1 0 1 | 0 0 1 1 1 | Send value to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
RAM MODULE
NOTE: Logic is needed to be able to intercept the output and show this on a LED array, while not making the data available on the bus.
