jorenheit/bfcpu/doc/circuits/register_driver.kicad_sch

## KiCad design doc/circuits/register_driver.kicad_sch (2025-11-19)

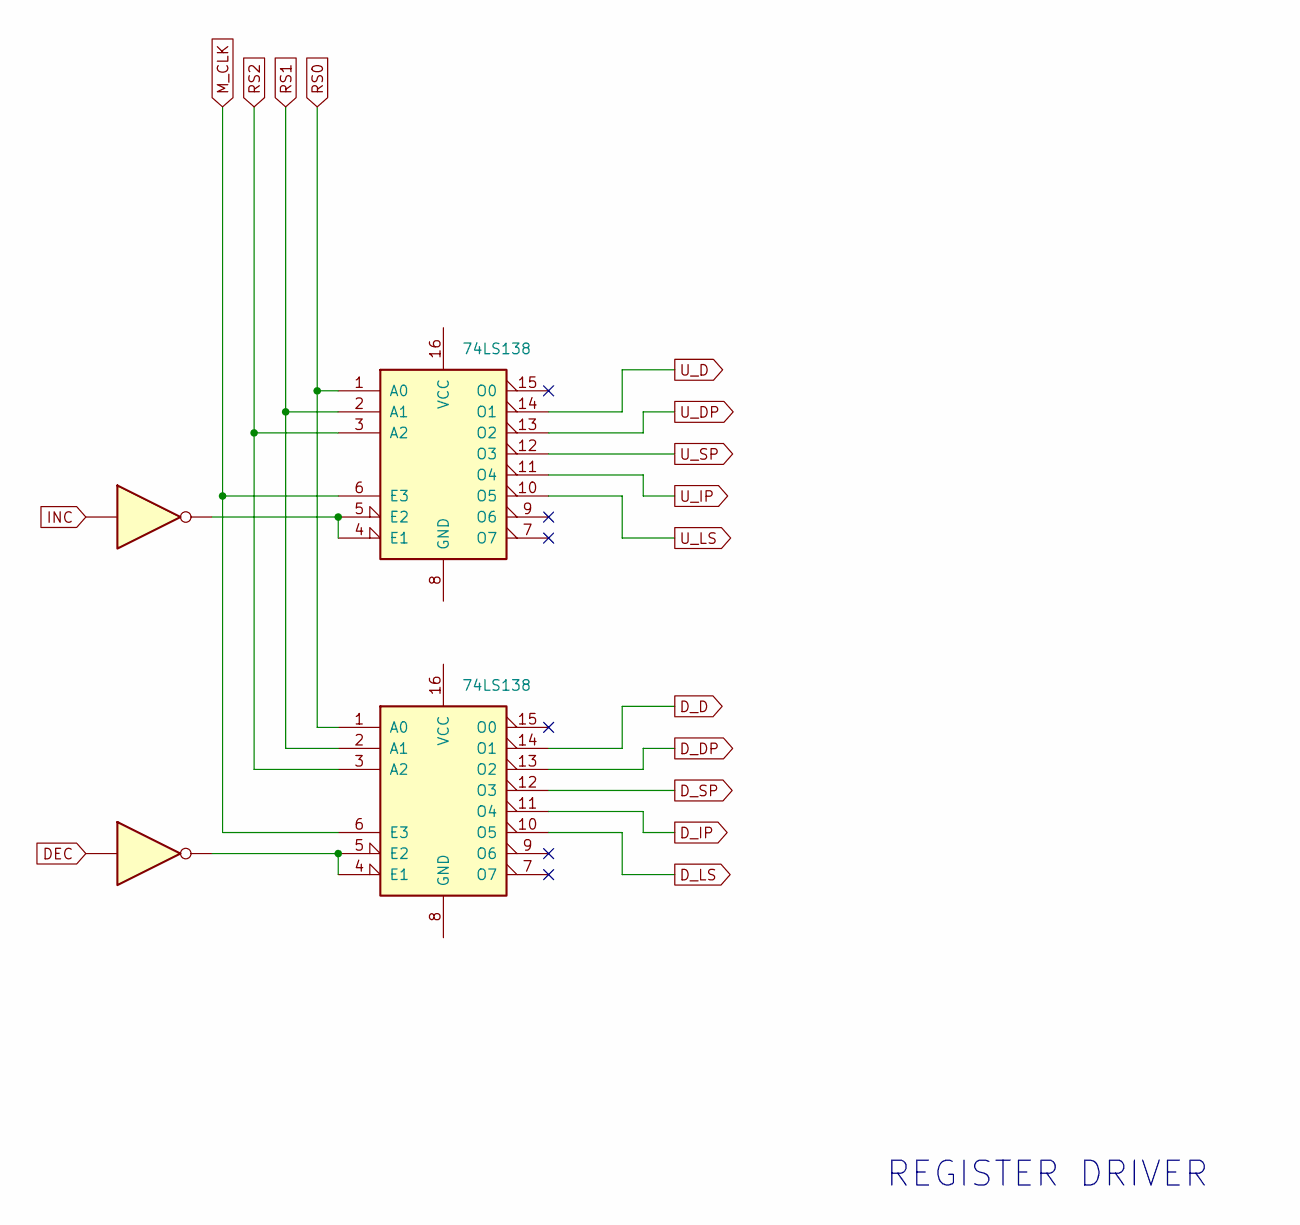
[picture p190: schematic register_driver.kicad_sch]

Parts:
U1, U2: 74LS138
U3: 74LS04

Connections:
DEC: U3.3
D_D: U2.14 (O1)
D_DP: U2.13 (O2)
D_IP: U2.11 (O4)
D_LS: U2.10 (O5)
D_SP: U2.12 (O3)
INC: U3.1
M_CLK: U1.6 (E3), U2.6 (E3)
unnamed: U1.4 (E1), U1.5 (E2), U3.2
unnamed: U2.4 (E1), U2.5 (E2), U3.4
RS0: U1.1 (A0), U2.1 (A0)
RS1: U1.2 (A1), U2.2 (A1)
RS2: U1.3 (A2), U2.3 (A2)
U_D: U1.14 (O1)
U_DP: U1.13 (O2)
U_IP: U1.11 (O4)
U_LS: U1.10 (O5)
U_SP: U1.12 (O3)

Notes on the sheet:
REGISTER DRIVER
