jorenheit/bfcpu/doc/circuits/signal_distributor.kicad_sch

## KiCad design doc/circuits/signal_distributor.kicad_sch (2025-02-24)

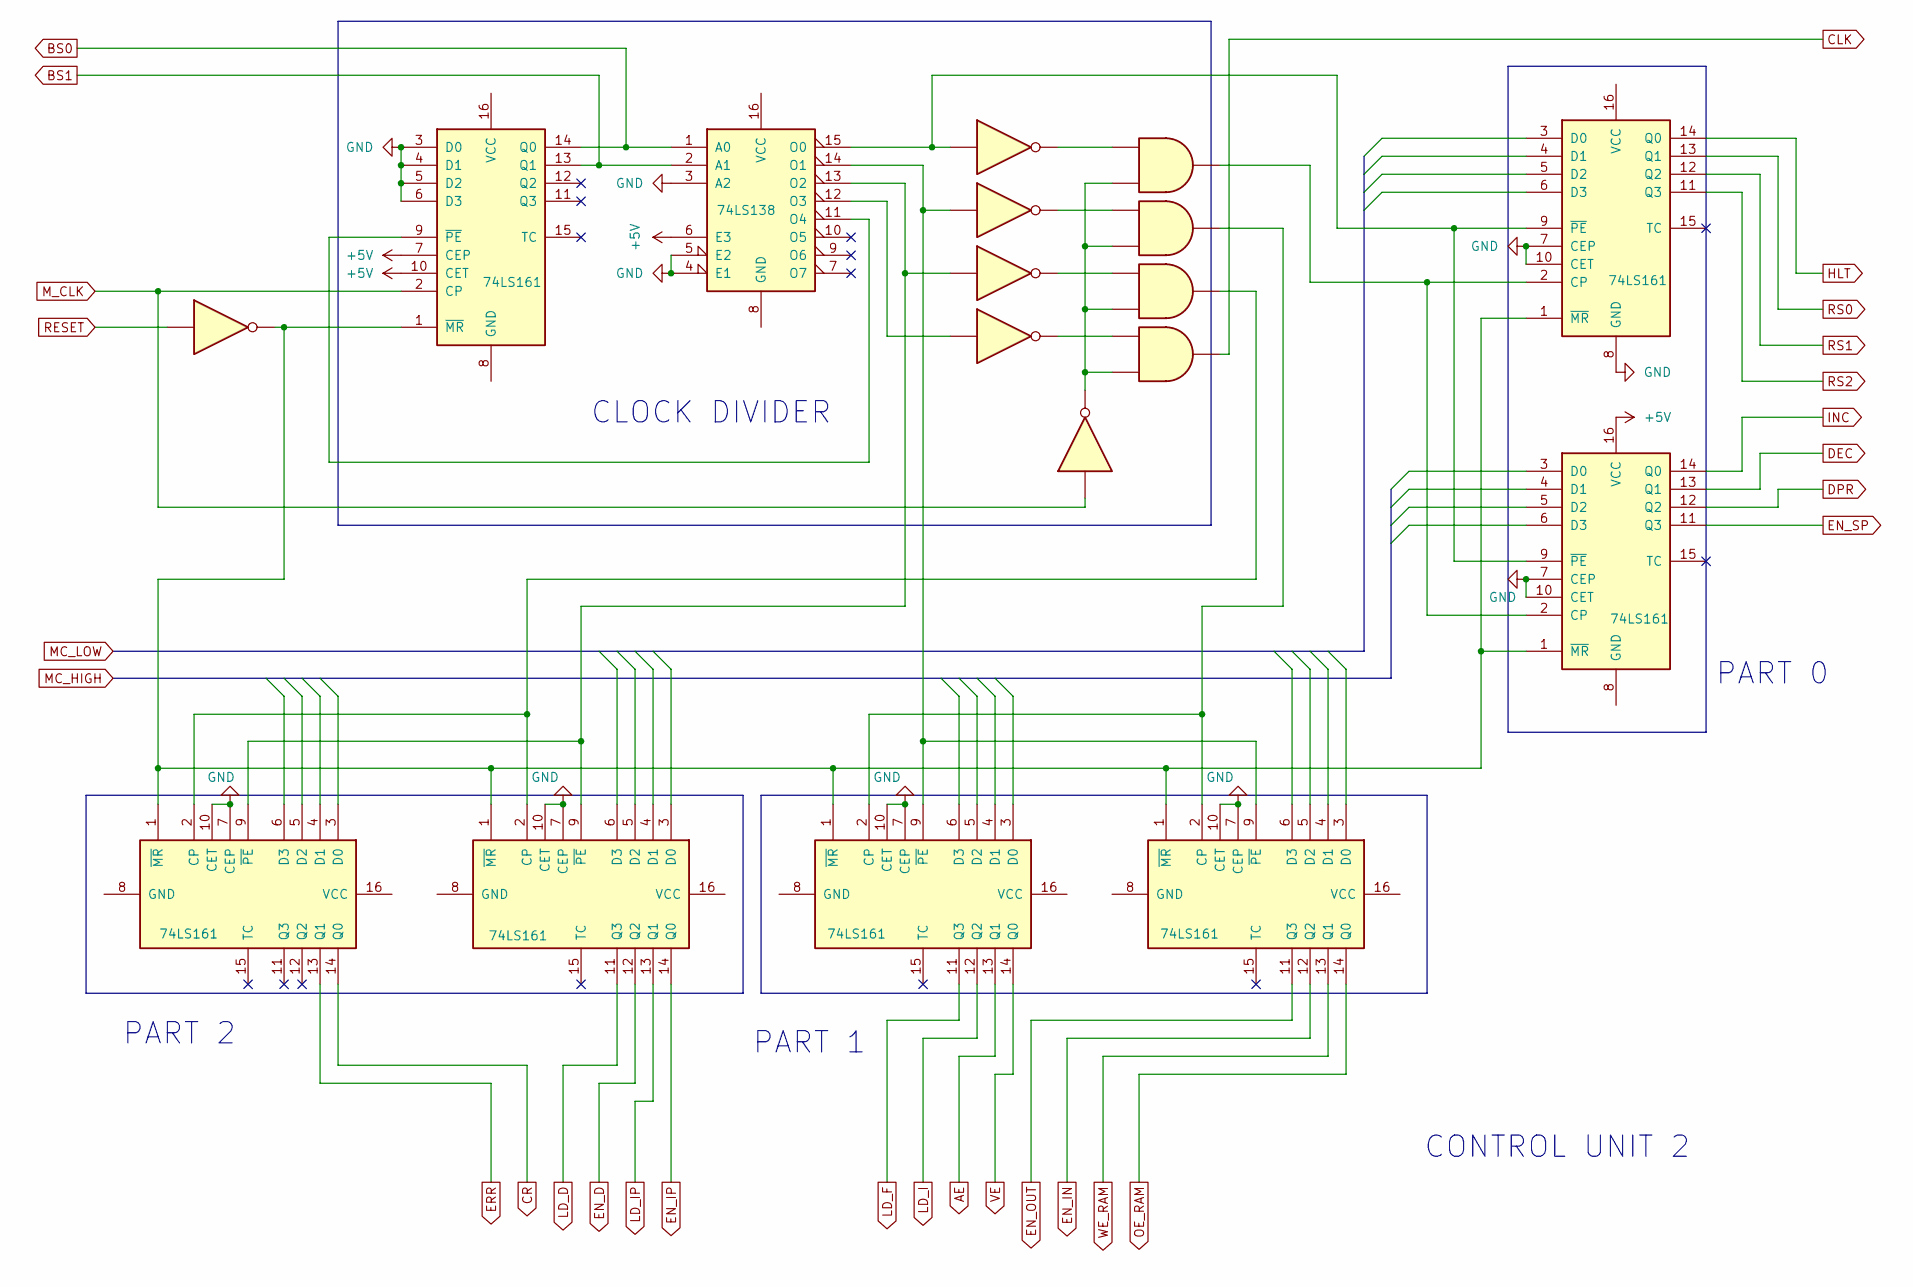
[picture p191: schematic signal_distributor.kicad_sch]

Parts:
U1: 74LS138
U2, U6, U7, U8, U9, U10, U11: 74LS161
U3, U5, U12: 74LS04
U4: 74LS08

Connections:
+5V: U1.6 (E3), U6.7 (CEP), U6.10 (CET), U10.16 (VCC)
AE: U8.13 (Q1)
BS0: U1.1 (A0), U6.14 (Q0)
BS1: U1.2 (A1), U6.13 (Q1)
CLK: U4.11
CR: U2.14 (Q0)
DEC: U10.13 (Q1)
DPR: U10.12 (Q2)
EN_D: U7.12 (Q2)
EN_IN: U9.12 (Q2)
EN_IP: U7.14 (Q0)
EN_OUT: U9.11 (Q3)
EN_SP: U10.11 (Q3)
ERR: U2.13 (Q1)
GND: U1.3 (A2), U1.4 (E1), U1.5 (E2), U2.7 (CEP), U2.10 (CET), U6.3 (D0), U6.4 (D1), U6.5 (D2), U6.6 (D3), U7.7 (CEP), U7.10 (CET), U8.7 (CEP), U8.10 (CET), U9.7 (CEP), U9.10 (CET), U10.7 (CEP), U10.10 (CET), U11.7 (CEP), U11.8 (GND), U11.10 (CET)
HLT: U11.14 (Q0)
INC: U10.14 (Q0)
LD_D: U7.11 (Q3)
LD_F: U8.11 (Q3)
LD_I: U8.12 (Q2)
LD_IP: U7.13 (Q1)
M_CLK: U5.9, U6.2 (CP)
unnamed: U1.11 (O4), U6.9 (~PE)
unnamed: U1.12 (O3), U3.9
unnamed: U1.13 (O2), U2.9 (~PE), U3.5, U7.9 (~PE)
unnamed: U1.14 (O1), U3.3, U8.9 (~PE), U9.9 (~PE)
unnamed: U1.15 (O0), U3.1, U10.9 (~PE), U11.9 (~PE)
unnamed: U2.2 (CP), U4.8, U7.2 (CP)
unnamed: U3.2, U4.1
unnamed: U3.4, U4.4
unnamed: U3.6, U4.9
unnamed: U3.8, U4.12
unnamed: U4.6, U8.2 (CP), U9.2 (CP)
unnamed: U4.2, U4.5, U4.10, U4.13, U5.8
unnamed: U2.1 (~MR), U6.1 (~MR), U7.1 (~MR), U8.1 (~MR), U9.1 (~MR), U10.1 (~MR), U11.1 (~MR), U12.8
unnamed: U4.3, U10.2 (CP), U11.2 (CP)
OE_RAM: U9.14 (Q0)
RESET: U12.9
RS0: U11.13 (Q1)
RS1: U11.12 (Q2)
RS2: U11.11 (Q3)
VE: U8.14 (Q0)
WE_RAM: U9.13 (Q1)

Notes on the sheet:
PART 0
PART 1
PART 2
CLOCK DIVIDER
CONTROL UNIT 2
