jorenheit/bfcpu/doc/circuits/signal_fetcher.kicad_sch

## KiCad design doc/circuits/signal_fetcher.kicad_sch (2025-02-24)

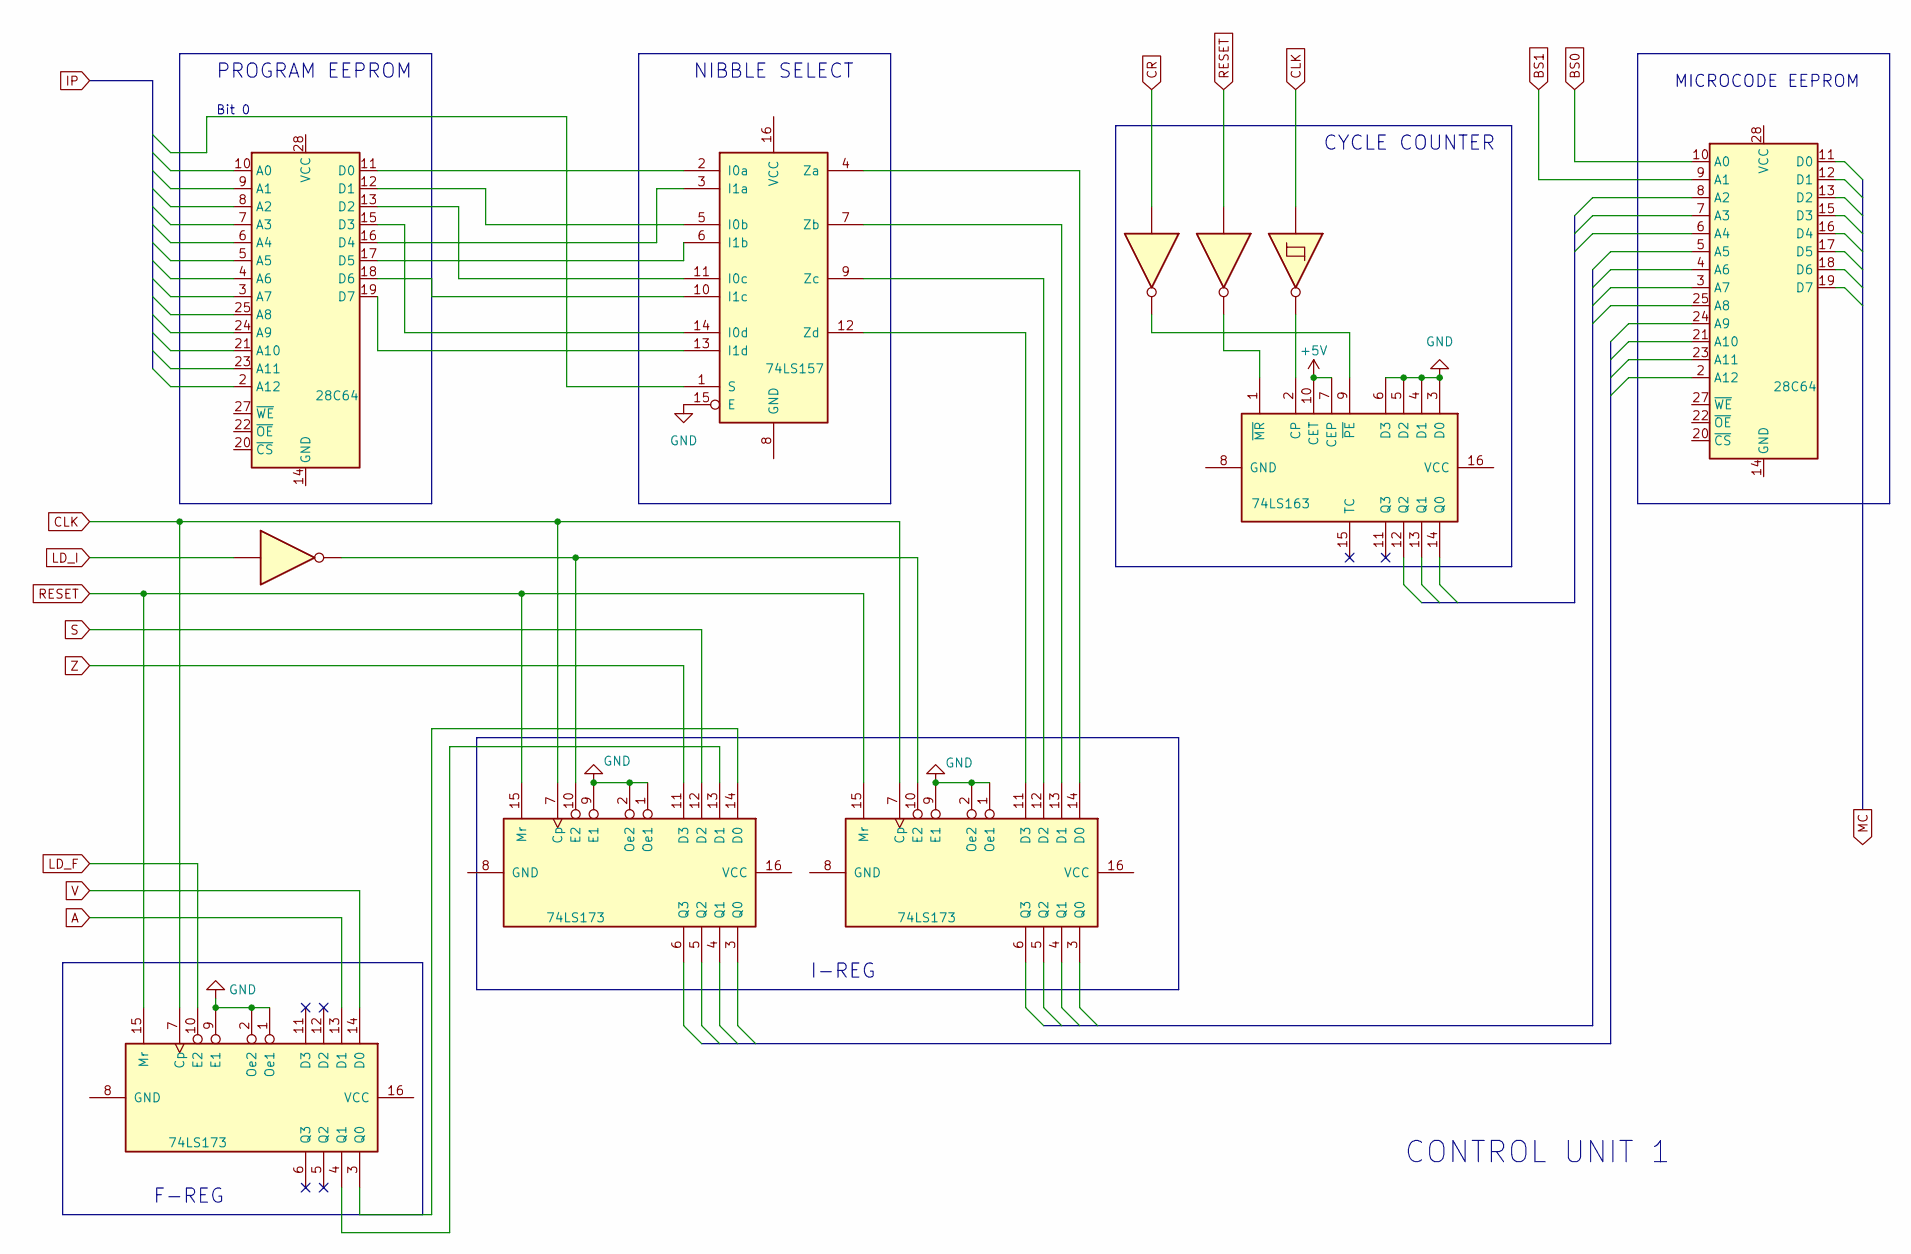
[picture p192: schematic signal_fetcher.kicad_sch]

Parts:
U1, U6: 28C64
U2: 74LS157
U3, U4, U11: 74LS173
U5, U9, U10: 74LS04
U7: 74LS163
U8: 74LS14

Connections:
+5V: U7.7 (CEP), U7.10 (CET)
A: U11.13 (D1)
BS0: U6.10 (A0)
BS1: U6.9 (A1)
CLK: U3.7 (Cp), U4.7 (Cp), U8.1, U11.7 (Cp)
CR: U10.1
GND: U2.15 (E), U3.1 (Oe1), U3.2 (Oe2), U3.9 (E1), U4.1 (Oe1), U4.2 (Oe2), U4.9 (E1), U7.3 (D0), U7.4 (D1), U7.5 (D2), U7.6 (D3), U11.1 (Oe1), U11.2 (Oe2), U11.9 (E1)
LD_F: U11.10 (E2)
LD_I: U5.1
unnamed: U1.11 (D0), U2.2 (I0a)
unnamed: U1.12 (D1), U2.5 (I0b)
unnamed: U1.13 (D2), U2.11 (I0c)
unnamed: U1.15 (D3), U2.14 (I0d)
unnamed: U1.16 (D4), U2.3 (I1a)
unnamed: U1.17 (D5), U2.6 (I1b)
unnamed: U1.18 (D6), U2.10 (I1c)
unnamed: U1.19 (D7), U2.13 (I1d)
unnamed: U2.4 (Za), U3.14 (D0)
unnamed: U2.7 (Zb), U3.13 (D1)
unnamed: U2.9 (Zc), U3.12 (D2)
unnamed: U2.12 (Zd), U3.11 (D3)
unnamed: U3.10 (E2), U4.10 (E2), U5.2
unnamed: U7.1 (~MR), U9.2
unnamed: U7.2 (CP), U8.2
unnamed: U7.9 (~PE), U10.2
unnamed: U4.14 (D0), U11.3 (Q0)
unnamed: U4.13 (D1), U11.4 (Q1)
RESET: U3.15 (Mr), U4.15 (Mr), U9.1, U11.15 (Mr)
S: U4.12 (D2)
V: U11.14 (D0)
Z: U4.11 (D3)

Notes on the sheet:
F-REG
PROGRAM EEPROM
NIBBLE SELECT
MICROCODE EEPROM
I-REG
CONTROL UNIT 1
Bit 0
CYCLE COUNTER
