jorenheit/bfcpu/doc/circuits/stack_pointer_register.kicad_sch

## KiCad design doc/circuits/stack_pointer_register.kicad_sch (2025-01-12)

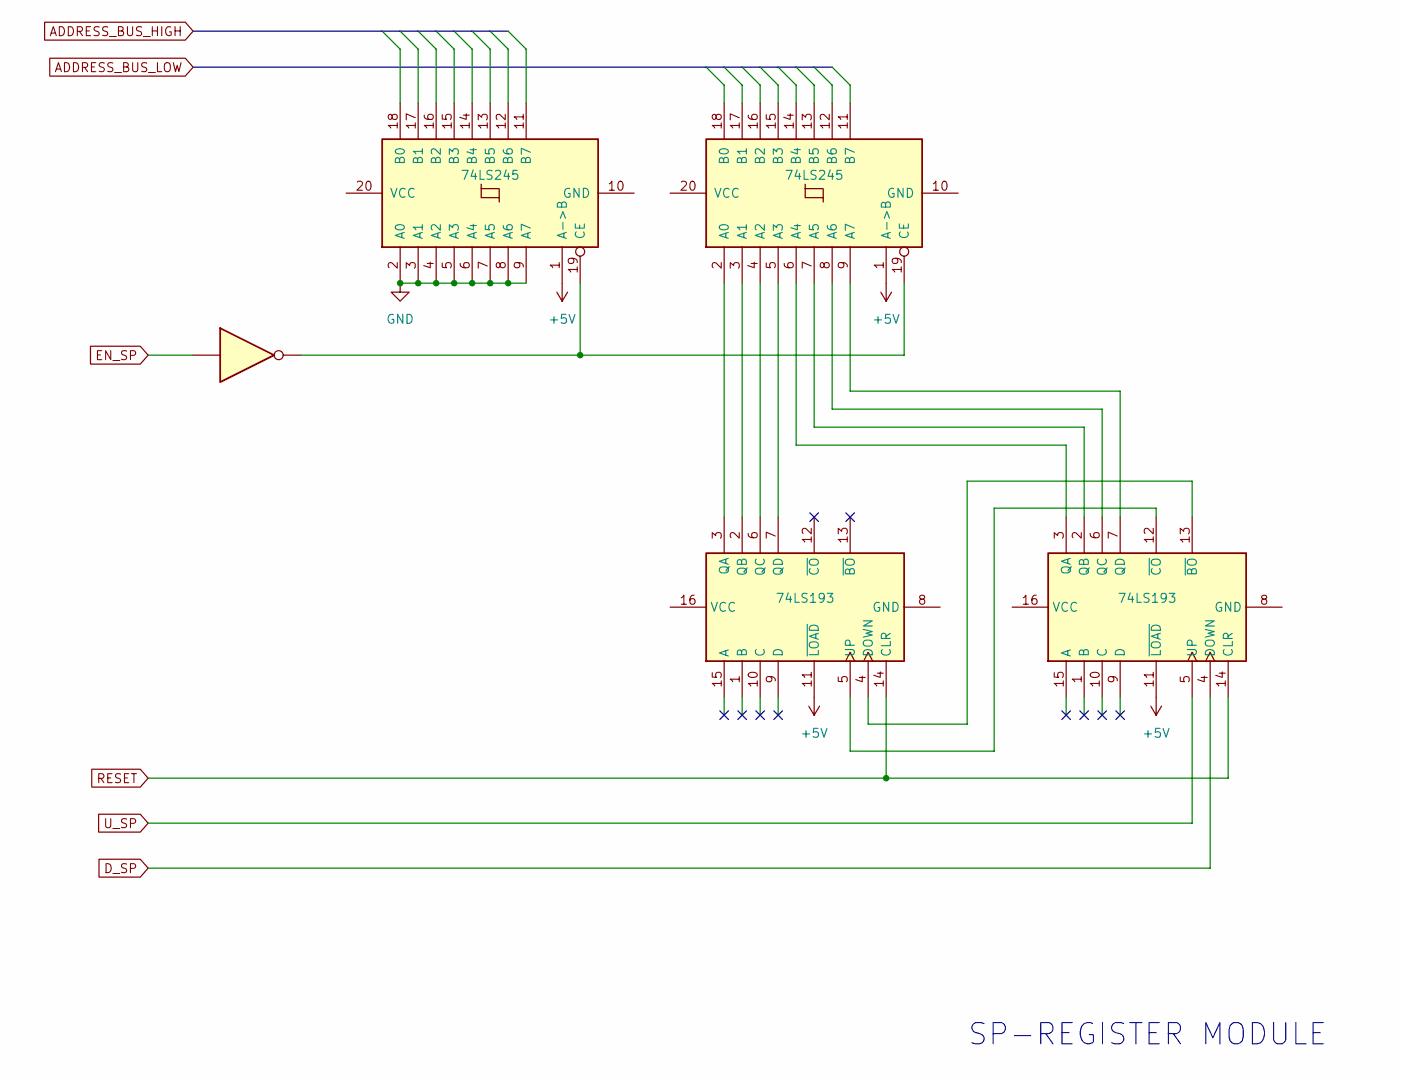
[picture p193: schematic stack_pointer_register.kicad_sch]

Parts:
U1, U7: 74LS245
U2: 74LS04
U6, U8: 74LS193

Connections:
+5V: U1.1 (A->B), U6.11 (~LOAD), U7.1 (A->B), U8.11 (~LOAD)
D_SP: U8.4 (DOWN)
EN_SP: U2.1
GND: U1.2 (A0), U1.3 (A1), U1.4 (A2), U1.5 (A3), U1.6 (A4), U1.7 (A5), U1.8 (A6), U1.9 (A7)
unnamed: U1.19 (CE), U2.2, U7.19 (CE)
unnamed: U6.2 (QB), U7.3 (A1)
unnamed: U6.3 (QA), U7.2 (A0)
unnamed: U6.4 (DOWN), U8.13 (~BO)
unnamed: U6.5 (UP), U8.12 (~CO)
unnamed: U6.6 (QC), U7.4 (A2)
unnamed: U6.7 (QD), U7.5 (A3)
unnamed: U7.6 (A4), U8.3 (QA)
unnamed: U7.7 (A5), U8.2 (QB)
unnamed: U7.8 (A6), U8.6 (QC)
unnamed: U7.9 (A7), U8.7 (QD)
RESET: U6.14 (CLR), U8.14 (CLR)
U_SP: U8.5 (UP)

Notes on the sheet:
SP-REGISTER MODULE
