jorenheit/bfcpu/src/bflash/bflash.py

#!/usr/bin/env python3

import argparse
import serial
import time
import threading
import math
import readline
import os

DUMP_REQUEST = b"\0"
FLASH_REQUEST = b"\1"
PROGRAMMER_READY = b"\2"
PROGRAMMER_FINISHED = b"\3"

ready = threading.Event()
done = threading.Event()

def show_percentage(current, total, previous, msg):
    new_percentage = math.floor(current / total * 10) * 10
    if new_percentage > previous:
        print(f"{msg} {new_percentage}%")
        return new_percentage
    return previous


def write_data(ser, file):
    data = bytearray(file.read())
    data_length = len(data).to_bytes(4, byteorder='little')

    while not ready.is_set() and not done.is_set():
        time.sleep(0.5)

    if done.is_set():
        return

    ser.write(FLASH_REQUEST)
    ser.write(data_length)

    CHUNK_SIZE = 50
    for i in range(0, len(data), CHUNK_SIZE):
        ready.clear()
        chunk = data[i:i+CHUNK_SIZE]
        ser.write(chunk)
        ser.flush()
        ready.wait()

    ser.flush()

    

def read_data(ser, file):
    while not ready.is_set() and not done.is_set():
        time.sleep(0.5)

    ser.write(DUMP_REQUEST)
    data_length = int.from_bytes(ser.read(4), byteorder='little')
    print("Getting ", data_length, " bytes")
    data = bytearray()
    percentage = 0
    for i in range(0, data_length):
        percentage = show_percentage(i, data_length, percentage, "Downloading... ")
        data += ser.read()
    print("Downloading... 100%")

    file.write(data)


def serial_monitor(ser, keep_alive):
    try:
        while True:
            c = ser.read()
            if c == PROGRAMMER_READY:
                ready.set()
                if not keep_alive:
                    return
            elif c == PROGRAMMER_FINISHED:
                done.set()
                break
            else:
                print(c.decode(), end="")
    except Exception as e:
        print(f"Error in serial_monitor: {e}")


def input_with_autocomplete(prompt, completer):
    readline.set_completer(completer)
    readline.parse_and_bind('tab: complete')
    try:
        return input(prompt)
    finally:
        readline.set_completer()


def filename_completer(text, state):
    files = [f for f in os.listdir('.') if os.path.isfile(f)]
    files = [f for f in files if f.startswith(text)]
    return files[state] if state < len(files) else None


def handle(port, baudrate, worker, filename, file_flags, msg, serial_monitor_keep_alive):
    try:
        if not filename:
            filename = input_with_autocomplete(msg, filename_completer).strip()
        
        with serial.Serial(port, baudrate, timeout=None) as ser, \
             open(filename, file_flags) as file:
            
            workerThread  = threading.Thread(target=worker, \
                                             args=(ser, file))
            monitorThread = threading.Thread(target=serial_monitor, \
                                             args=(ser, serial_monitor_keep_alive))
            
            workerThread.start()
            monitorThread.start()
            
            workerThread.join()
            monitorThread.join()
            
    except FileNotFoundError:
        print(f"Error: File '{filename}' not found.")
    except serial.SerialException as e:
        print(f"Error: {e}. Check if the specified serial port is valid.")


def prompt():
    while True:
        choice = input_with_autocomplete("Enter 'D' to dump the current ROM to a file or 'F' to flash a file onto the ROM: ", \
                                         filename_completer).lower()
        if choice in ["d", "f"]:
            return choice
        else:
            print("Invalid choice. Please enter 'D', 'F'")


def main():
    parser = argparse.ArgumentParser(description='Application to dump/flash ROM over serial connection.')
    parser.add_argument('port', help='Serial port name')
    parser.add_argument('baudrate', type=int, help='Baud rate for the serial connection')
    parser.add_argument('--dump', '-d', metavar='file', nargs=1, help='Dump ROM to file')
    parser.add_argument('--flash', '-f', metavar='file', nargs=1, help='Flash file onto ROM')
    
    args = parser.parse_args()
    
    if (args.dump and args.flash):
        print("Please provide either --dump (-d) or --flash (-f) but not both.")
        return
    elif (args.dump):
        choice = "d"
        fname = args.dump[0]
    elif (args.flash):
        choice = "f"
        fname = args.flash[0]
    else:
        choice = prompt()
        fname = None
        
    if choice == "d":
        handle(port=args.port,\
               baudrate=args.baudrate,\
               worker=read_data,\
               filename=fname,\
               file_flags="wb",\
               msg="Enter the file to dump ROM into: ",\
               serial_monitor_keep_alive=False)
        
    elif choice == "f":
        handle(port=args.port,\
               baudrate=args.baudrate,\
               worker=write_data,\
               filename=fname,\
               file_flags="rb",\
               msg="Enter the file to flash onto ROM: ",\
               serial_monitor_keep_alive=True)


if __name__ == "__main__":
    main()
