jorenheit/bfcpu/src/io_module/lcdmenu.h

#pragma once

#include "settings.h"
#include "button.h"
#include "lcdbuffer.h"
#include "lcdscreen.h"
#include "menu.h"

class LCDMenu {

  // Actions contains the functions that are available from within the menu-nodes.
  class Actions {
    Settings &_settings;
    LCDBuffer &_lcdBuf;
    KeyboardBuffer &_kbBuf;

  public:
    Actions(Settings &s, LCDBuffer &buf1, KeyboardBuffer &buf2):
      _settings(s),
      _lcdBuf(buf1),
      _kbBuf(buf2)
    {}

    inline void clear()                                   { _lcdBuf.clear(); _kbBuf.clear(); }
    inline void setEchoEnabled(bool const val)            { _settings.echoEnabled = val; }
    inline void setAutoscrollEnabled(bool const val)      { _settings.autoscrollEnabled = val; }
    inline void setDisplayMode(::DisplayMode const mode)  { _settings.displayMode = mode; }
    inline void setInputMode(::InputMode const mode)      { _settings.inputMode = mode; }
    inline void setDelimiter(char const delim)            { _settings.delimiter = delim; }
    inline void restoreDefaults()                         { _settings = {}; }
  };

  MenuActions(Actions);

  // Define submenu nodes
  SubMenu(MainMenu,    "Settings",      { /* No action on select */            });
  SubMenu(Echo,        "Echo",          { /* No action on select */            });
  SubMenu(Autoscroll,  "Autoscroll",    { /* No action on select */            });
  SubMenu(DisplayMode, "Display Mode",  { /* No action on select */            });
  SubMenu(DecMode,     "Decimal",       { actions.setDisplayMode(DECIMAL);     });
  SubMenu(HexMode,     "Hexadecimal",   { actions.setDisplayMode(HEXADECIMAL); });
  SubMenu(SetRNGSeed,  "Set RNG Seed",  { /* No action on select */            });
  SubMenu(InputMode,   "Input Mode",    { /* No action on select */            });
  SubMenu(SelectSlot,  "Select Slot",   { /* No action on select */            });

  // Define leaf nodes
  MenuLeaf(Clear,          "Clear Buffers", item.exit(),   { actions.clear();                     });
  MenuLeaf(EchoOn,         "On",            item.home(),   { actions.setEchoEnabled(true);        });
  MenuLeaf(EchoOff,        "Off",           item.home(),   { actions.setEchoEnabled(false);       });
  MenuLeaf(AutoscrollOn,   "On",            item.home(),   { actions.setAutoscrollEnabled(true);  });
  MenuLeaf(AutoscrollOff,  "Off",           item.home(),   { actions.setAutoscrollEnabled(false); });
  MenuLeaf(TextMode,       "Text",          item.home(),   { actions.setDisplayMode(ASCII);       });
  MenuLeaf(CommaDelim,     ",",             item.home(),   { actions.setDelimiter(',');           });
  MenuLeaf(SemiDelim,      ";",             item.home(),   { actions.setDelimiter(';');           });
  MenuLeaf(BarDelim,       "|",             item.home(),   { actions.setDelimiter('|');           });
  MenuLeaf(SpaceDelim,     "[SPACE]",       item.home(),   { actions.setDelimiter(' ');           });
  MenuLeaf(Defaults,       "Defaults",      item.exit(),   { actions.restoreDefaults();           });
  MenuLeaf(BufferedInput,  "Buffered",      item.home(),   { actions.setInputMode(BUFFERED);      });
  MenuLeaf(ImmediateInput, "Immediate",     item.home(),   { actions.setInputMode(IMMEDIATE);     });
  MenuLeaf(Exit,           "Exit",          item.exit(),   { /* No action on select */            });
  
  // Bind value-select menu's to variables that store the setting
  ValueSelect(SeedSelecter, rngSeedPtr);  
  ValueSelect(SlotSelecter, slotPtr);

  // Build the final menu-type:
  using Menu = MainMenu <
    SelectSlot<
      SlotSelecter<0, N_SLOTS - 1>
    >,
    Clear,
    Echo<
      EchoOn,
      EchoOff
    >,
    Autoscroll<
      AutoscrollOn,
      AutoscrollOff
    >,
    DisplayMode<
      TextMode,
      DecMode <
        CommaDelim,
        SemiDelim,
        BarDelim,
        SpaceDelim
      >,
      HexMode<
        CommaDelim,
        SemiDelim,
        BarDelim,
        SpaceDelim
      >
    >,
    InputMode<
      BufferedInput,
      ImmediateInput
    >,
    SetRNGSeed<
      SeedSelecter<RNG_MIN_SEED, RNG_MAX_SEED>
    >,
    Defaults,
    Exit
  >;

  Menu _menu;
  Menu::Pointer _current = nullptr;
  uint8_t _selectedLine = 1;

  Settings &_settings;
  LCDScreen &_screen;
  Actions _actions;
  unsigned long _lastActiveTime = 0;

public:
  LCDMenu(LCDScreen &scr, Settings &s, LCDBuffer &lcdBuf, KeyboardBuffer &kbBuf);
  void enter();
  bool active() const;
  void handleButtons(ButtonState const up, ButtonState const down, ButtonState const both);
  void display();
  void saveSettings();
  void loadSettings();
  void exit();
};
