jorenheit/bfcpu/src/io_module/lcdscreen.h

#pragma once

#include "LiquidCrystal_74HC595.h"
#include "settings.h"

class LCDScreen {
  Settings const &settings;
  LiquidCrystal_74HC595 lcd;
  unsigned long tempTimeout = 0;

public:
  LCDScreen(Settings const &s);

  void begin();
  void display(LCDBuffer::View const &view, bool forced = false); 
  void displayTemp(char const *lines[], uint8_t const n, size_t const timeout);
  void abortTemp();
  void enableCursor();
  void disableCursor();

  template <typename ... Args>
  void displayTemp(size_t const timeout, Args ... args) {
    static_assert(sizeof ... (Args) <= VISIBLE_LINES, "Too many lines");
    char const *lines[] = {args ...}; 
    displayTemp(lines, sizeof ... (args), timeout);
  }

  template <typename ... Args>
  void displayTemp(size_t const timeout, char const *fmtString, Args ... args) {
    char line[LINE_SIZE + 1];
    memset(line, ' ', LINE_SIZE + 1);
    snprintf(line, sizeof(line), fmtString, args ...);
    displayTemp(timeout, line);
  }
};
