jorenheit/bfcpu/src/io_module/lcdscreen.ino

#include "lcdscreen.h"

LCDScreen::LCDScreen(Settings const &s):
  settings(s),
  lcd(LINE_SIZE, VISIBLE_LINES)
{}

void LCDScreen::begin() {
  lcd.begin();
  displayTemp(TEMP_MESSAGE_TIMEOUT, "Loading slot: %d", settings.programSlot);
}

void LCDScreen::display(LCDBuffer::View const &view, bool forced) {
  static bool tempDisplayActive = false;
  static size_t lastViewID = 0;
  static unsigned long lastViewTime = 0;

  if (tempTimeout && (millis() < tempTimeout)) {
    tempDisplayActive = true;
    return;
  }

  if (tempDisplayActive) {
    // temp display was active but has now has timed out (or was cancelled) -> reset and force display update
    tempDisplayActive = false;
    tempTimeout = 0; 
    forced = true;
  }

  if ((view.id == lastViewID || (millis() - lastViewTime) < DISPLAY_FRAMETIME_MILLIS) && !forced) 
    return;

  lastViewID = view.id;
  for (uint8_t line = 0; line != VISIBLE_LINES; ++line) {
    lcd.setCursor(0, line);
    lcd.print(view.lines[line]);
  }

  // Display cursor at the position where the next character will be printed (if in view).
  if (view.cursorRow < VISIBLE_LINES) {
    lcd.setCursor(view.cursorCol, view.cursorRow);
    enableCursor();
  }
  else {
    // Cursor not in view -> turn off
    disableCursor();
  }
}

void LCDScreen::displayTemp(char const *lines[], uint8_t const n, size_t const timeout)
{
  static char emptyLine[LINE_SIZE + 1];
  static bool initialized = false;
  if (!initialized) {
    memset(emptyLine, ' ', LINE_SIZE);
    emptyLine[LINE_SIZE] = 0;
    initialized = true;
  } 

  for (uint8_t idx = 0; idx != VISIBLE_LINES; ++idx) {
    lcd.setCursor(0, idx);
    lcd.print(idx < n ? lines[idx] : emptyLine);
  }
  disableCursor();
  tempTimeout = millis() + timeout;
}

void LCDScreen::abortTemp() {
  tempTimeout = 0;
}

void LCDScreen::enableCursor() {
  lcd.cursor();
  lcd.blink();
}

void LCDScreen::disableCursor() {
  lcd.noCursor();
  lcd.noBlink();
}
