jorenheit/bfcpu/src/io_module/keyboardbuffer.h

#pragma once
#include "settings.h"
#include "PS2Keyboard.h"


class KeyboardBuffer {   
  PS2Keyboard kb;

  using RB = RingBuffer<char, KB_RING2>;
  RB ringBuf;
  Settings const &settings;

public:
  KeyboardBuffer(Settings const &s):
    settings(s)
  {}

  void begin();
  void update();
  char get();
  void clear();
  char peek() const;
  RB::IndexType available() const; 
};
