jorenheit/bfcpu/src/io_module2/button.h

#pragma once
#include "settings.h"
#include "common.h"

template <int Pin>
class Button {
public:
  void begin() {
    pinMode(Pin, INPUT);
  }

  bool pressed() const {
    static unsigned long lastPressedTime = millis();
    unsigned long const currentTime = millis();
    if (currentTime - lastPressedTime < BUTTON_DEBOUNCE_DELAY)
      return false;

    if (digitalRead<Pin>()) {
      lastPressedTime = currentTime;
      return true;
    }
    return false;
  }
};
