jorenheit/bfcpu/doc/img/pics/20241211_155425.jpg

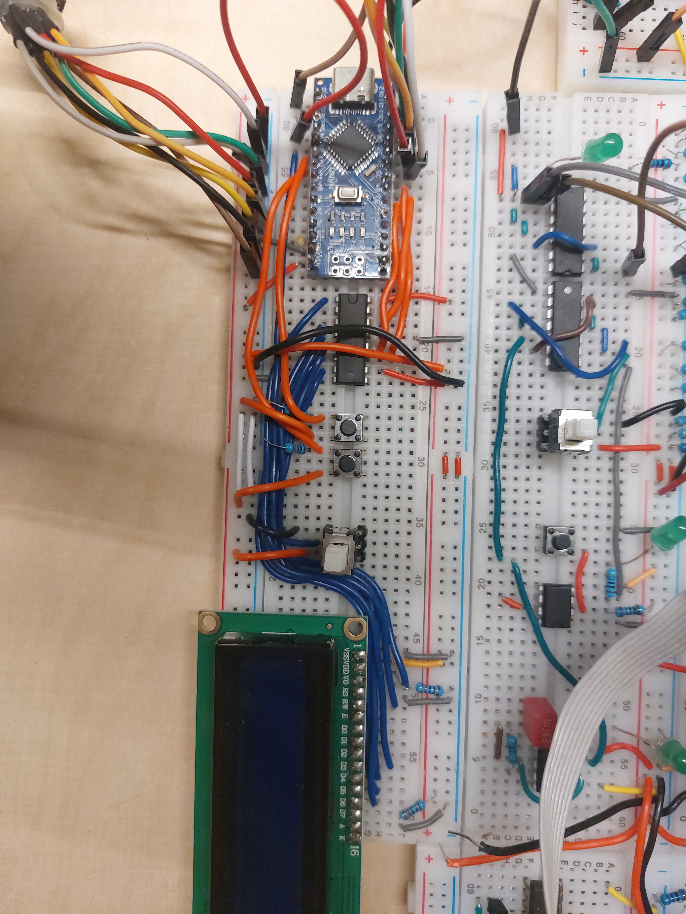
doc/img/pics/20241211_155425.jpg
