jorenheit/bfcpu/doc/img/pics/20241212_222240.jpg

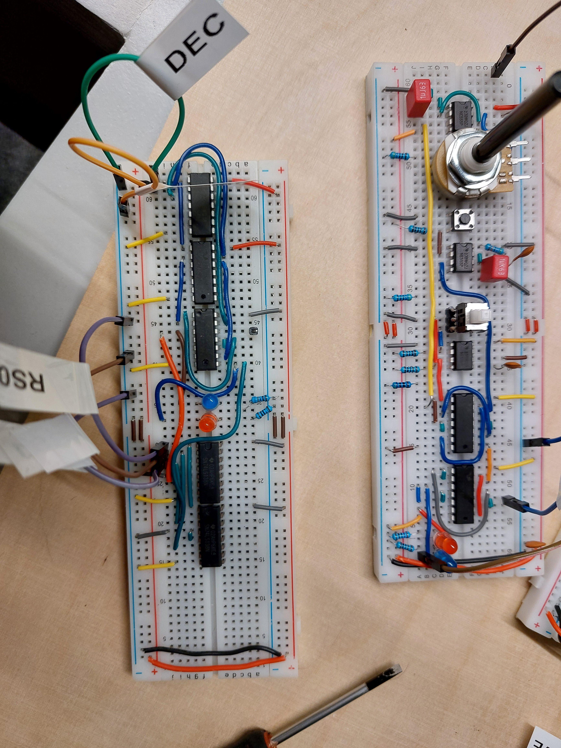
doc/img/pics/20241212_222240.jpg
