jorenheit/bfcpu/doc/img/pics/1000041102.jpg

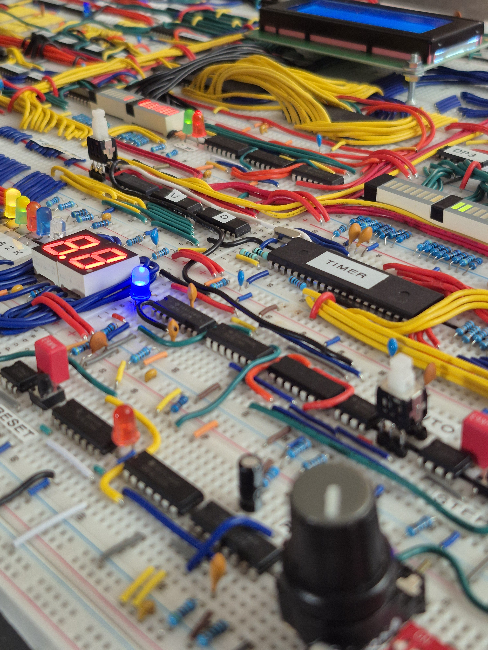
doc/img/pics/1000041102.jpg
