jorenheit/bfcpu/doc/img/pics/1000041104.jpg

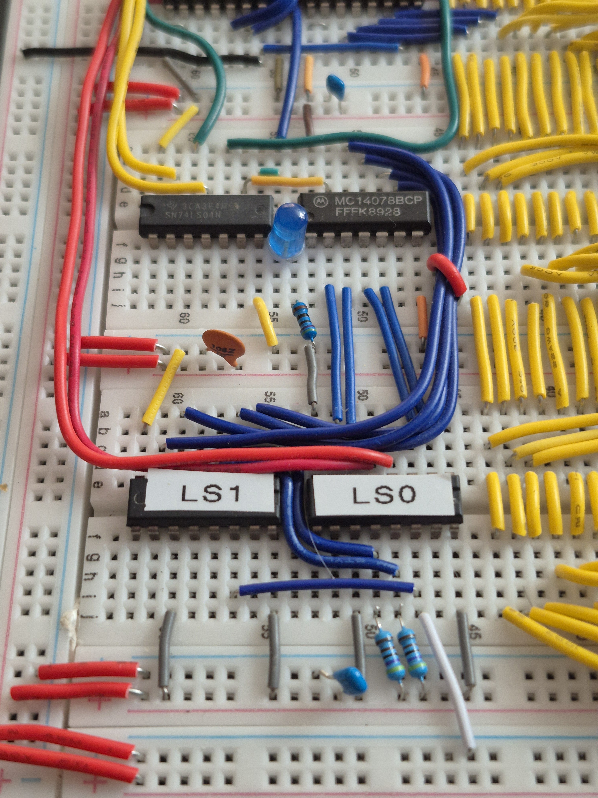
doc/img/pics/1000041104.jpg
